mckayreedmoore/mini-moonboard/fea/code_aster_trial/contact_3d_mixed_reversed/README.md

# Reversed-order 3-D contact control

This Code_Aster 17.4 coupon repeats the frozen `mixed-active-open` geometry and loading while reversing the order of the two slave TRIA6 names in `GROUP_MA SLAVE`. The only mesh-data change from `fea/code_aster_trial/contact_3d_mixed/` is `ST00001 ST00002` to `ST00002 ST00001`; coordinates, PENTA15/TRIA6 connectivity, material, contact formulation, constraints, and time history remain unchanged.

`ST00002` is the raised, open face and comes first. `ST00001` is the flat, active face and comes last. The open face has the same 0.477881 mm minimum initial AUTO-sample gap and the same 0.447881 mm clearance after a hypothetical rigid 0.03 mm closure as the baseline order. This control tests whether the shared nodes’ final `CONT_NOEU` status and `RN` depend on the last contact face processed. Read the RN-to-cut residual as a diagnostic; this control does not require recovering a particular force increment and makes no capacity or joint-acceptance claim.

The paired active-open fixture completed at [contact-3d-mixed-attempt02](../../../docs/wood-joints-mvp/hypotheses/code-aster-candidate-checks-2026-09-27/contact-3d-mixed-attempt02/). Its independent audit found all three shared nodes open/zero after the later open face, with a 676.258 N RN-to-cut z residual. This reversed-order run is a diagnostic control; interpret it alongside that frozen result and the Code_Aster v17 documentation for [`CONT_NOEU`](https://code-aster.org/doc/v17/manuals/man_u/u2/u2.04.04/M_thodologies.html) and [`LAGS_C`](https://code-aster.org/doc/v17/manuals/man_u/u2/u2.04.04/R_solution.html).

After both native attempts are complete, `compare_order_control.py` verifies frozen input hashes, confirms only the `SLAVE` group order changed in the mesh, and compares the shared-node fields and remote reactions. The parent owns readiness review, serialized native execution, and final interpretation. Solver convergence and an order-control result do not establish joint mechanics or candidate acceptance.
