mckayreedmoore/mini-moonboard/docs/wood-joints-mvp/hypotheses/wj24-owner-design-review-2026-09-24/README.md

# WJ24 owner-directed design-review viewer

This archive records the local WJ24 viewer after switching the same URL to the isolated `owner_wood_joints_design_review_scene/v1` branch. The current revision is `lower-rear-blocks-below-plus-bottom-support-up-one-row-v1`: the middle rear blocks sit below their rails and the bottom support is raised one hold row. The current report lists lower-edge support, wire routing, and provisional G2/G6 hold-clearance items for design review. No acceptance, capacity, installation, fabrication, assembly, structural, or climbing release is asserted.

The final viewer source is [snapshotted here](snapshots/wood-joints-wj24-viewer.html.snapshot), SHA-256 `3afb271aa1403e839f6382f78d6a120e1f00429c2bd3ec870fa7c923ec138669`. Its scene payload is 9,335,595 bytes, SHA-256 `bf68c4247e1a99b1c7d5bad02b0fe5f6b9ddec34a47e1dca6d41edd2ad731389`. The source-bound revision report is [snapshotted here](snapshots/owner-wood-joints-review-report.json.snapshot), SHA-256 `bf8392ff07d213525e7032802979c887c9de53540361844aa84cc9e740ce1c33`. The scene binds source inventory SHA-256 `07af4c3eb642cf3887595fe4415eb65404cdcf74d66c5c7bb182847ef21c2d78` and parent scene SHA-256 `b80baec6b4435f4cfad724efdc25df787d04251f1a1b7203ba63782fb4b485f0`.

The overlay contains 568 solids: 16 shared hosts, 28 candidate parts, 520 hardware occupancy envelopes, and four panel replacements. The pinned baseline has 725 hashed assets; 537 render once and 188 replaced visuals are suppressed. The 66 panel-screw visual identities comprise 62 unchanged axes and four moved axes, whose baseline STL instances receive explicit display translations. Twelve starting frame-bolt arrangements remain in the baseline. These display envelopes and transforms describe nominal CAD geometry only.

The parent-run Chromium evidence is in [browser-evidence](browser-evidence/). It verified the current design-review status, 537 visible / 188 suppressed baseline visuals, all three camera buttons, all five layer controls, and the 390×844 mobile layout. The result records no page errors or failed requests. The parent visually checked the full-frame image and confirmed the middle blocks below their rails and the raised bottom support are visible. The associated screenshots and [browser-check output](browser-evidence/browser-check.json) came from the cumulative geometry before a later caption-only refresh to the two hold-clearance findings; the parent confirmed the geometry was unchanged and did not require a rerun. The final scene and report snapshots here include that refreshed text. The viewer’s frame-to-kicker-options link was then moved directly below the revision summary so it is easy to find; the archived final HTML includes that placement. The earlier browser session used the separately preserved [browser-session HTML snapshot](snapshots/wood-joints-wj24-viewer.html.browser-session.snapshot), SHA-256 `e42a6b97216c6119da89d8c90bd5b4399b4f9f3acecd426d159281f649d9a6e2`.

The new design-review branch reads only its current `revision_report`, checks the raw report and source-inventory hashes, validates the model inventory against the displayed solids and baseline replacement policy, and leaves the older diagnostic branch intact for its archived payload. Its visible status explicitly says that earlier static or diagnostic passes do not carry into this revision. The [separate frame-to-kicker options page](../../../../site/wood-joints-kicker-options.html) remains exploratory; no alternative is selected.

The previous integrated-static viewer review and its export-time/final snapshots remain unchanged in the [original WJ24 viewer archive](../wj24-viewer-review/README.md). This new folder supplements that record; it does not replace it. Screen-reader verification remains pending.
