mckayreedmoore/mini-moonboard/docs/wood-joints-mvp/hypotheses/hl35-candidate/README.md

# HL35 replacement candidate

The owner now requests a thinner successor closer to the selected
screw-and-angle frame, with structural through-bolts retained. The solid
6×8 center, 6×6 bottom rails and shaped 6×10 header below are no longer the
desired development direction. The [contract](../../../../hl35-candidate.json)
records the restored single-2×6/split-center comparison basis and open
connector selection. The [earlier kerf-right viewer](../../../../site/index.html?model=compact-floor-flush-kerf-right)
is a geometry reference with original screw hardware, not a through-bolted
successor. The [thin bolted viewer](../../../../site/index.html?model=thin-bolted-development)
now exports the original-size timber proposal with 24 B104ZN and 12 B103ZN
fittings, 70 complete bolt stacks and 66 Hillman axes. Its separate
[contract](../../../../thin-bolted-candidate.json) binds the reviewed v4 model.
The owner has viewed it and requested parallel numerical MVP work with six
GPT-6.1 Sol agents at xhigh. Geometry, access, compatible mechanics and
resistance remain distinct gates; no candidate is selected or released.
Use the [active ledger](../../completion-ledger.md#hl35-replacement-candidate)
for current results and exact missing inputs. Preserve all failed HL35 studies
and source bindings below.

The owner requested a separate candidate using HL35s instead of the wood
corner blocks on October 6, 2026, with an attempt to complete it overnight.
The candidate is **`compact-floor-flush-hl35-development`**, now at revision
**`hl35-deeper-header-seat-and-bearing-audit-v8`**, with disposition **REVISE**.
The [contract](../../../../hl35-candidate.json) remains separate from both
selected authority and the preserved reviewed wood-joint model.

Open the [preserved enlarged-frame viewer](../../../../site/index.html?model=hl35-counterbore-development),
[assessment](counterbore-fit-v8/README.md) and [preview](counterbore-fit-v8/overview.png).
It maps all 24 former block duties to 22 joints with **30 HL35s / 112 structural
planning bolt axes / 66 Hillman screws**. Eight screw moves and three wire
proposals are recorded only in this candidate; panel outlines, holds, T-nuts
and LED endpoints remain at their reviewed datums.

**Four lower outer corner joints still require revision.** The deeper washer
seats clear all checked bolt/angle, metal/metal, screw and service intersections,
but remove wood under neighboring angles. After the recesses, **112 / 120**
minimum-wood probes and **52 / 60** nominal flange seats meet the full-support
geometry comparison. The other eight flange seats retain about **86–87%**
of their nominal bearing area. This is a failed geometry criterion, not an
accepted reduced-area joint. The full catalog, wood resistance, force/moment
paths, machining and physical access remain unqualified.

The receiving-stock proposal includes a solid 6×8 center, 6×6 bottom rails,
4×6 service/top rails and a shaped 6×10 header. At an explicitly assumed
500 kg/m³, its sixteen finished receivers alone are approximately **342 lb**,
including about **69 lb center** and **62 lb header**. Legs/runners, plywood,
holds and all hardware are excluded. Heavy individual members are a drawback
for the owner's transport goal; no total mass, purchase schedule or climber
rating is supplied.

The overnight candidate-creation and bounded assessment attempt is documented;
it did not produce a build-ready design. Next redesign the four lower corner
interfaces to separate bolt/washer paths from neighboring bearing wood, then
resolve complete joint and practical machining/assembly methods before new
candidate-specific force and resistance work. The original panel concerns and
unverified no-slip floor assumption remain. No native solve or release exists.

The [first direct-swap viewer](../../../../site/index.html?model=hl35-development),
[v7 failed complete-tip query](final-fit-v7/hardware-closure.json) and all distinct
failed inputs remain preserved. Earlier claims of zero clashes covered the
listed subset; the supplemental v7 check found eight bolt/angle and four
bolt/unrelated-timber contacts. V8 includes those checks and the missing
after-recess wood assessment, rather than transferring the narrower result.

## First direct replacement: preserved failed input

The builder reconstructs the sixteen reviewed raw receiving profiles from
their authenticated snapshot. The four previously changed host positions are
retained: the two center kicker posts and two bottom rails. It removes the
24 wood blocks and their 92 candidate bolt arrangements. The starting twelve
frame-bolt arrangements and the current 66 Hillman axes remain: 58 original
axes and eight previously owner-directed moves, with no additional screw moves.
The owned panel policy, kerf-right outlines and G2 LED datum stay explicit.

Each old structural duty receives an angle on each side of its upright.
Four flange holes per angle give 192 attachments. Opposed post-flange holes
share through-bolts; four additional pairs of header attachments coincide
across duties. The model therefore has **140 new proposed physical bolt axes**
and **152 including the twelve starting axes**, rather than 192 new bolts.
Those are planning axes, including rejected paths through insufficient or
absent wood. They are not a purchase schedule or 152 qualified connections.
Each new axis has five conditional metal display roles: shaft, head, two
washers and nut. Actual products, shanks, thread windows and tools are unverified.

The fit audit uses exact CadQuery solid intersections, with a bounding-box
filter only to skip disjoint objects. It checks a nominal bearing skin behind
each flange, a complete 88.9 mm receiving-wood cylinder at every flange hole,
angle-to-angle and angle-to-raw-wood/panel intersections, and the preserved
63.5 mm screw-length envelopes. A source-bound cylinder is a geometry check;
neither its clearance diameter nor its penetration is a drilling instruction.

| Check | Direct replacement | Unadopted 3½-inch stock sensitivity |
|---|---:|---:|
| Joint duties requiring fit revision | 24 / 24 | 22 / 24 |
| Attachments lacking full 88.9 mm receiving wood | 152 / 192 | 36 / 192 |
| Flanges lacking full nominal rectangular bearing | 80 / 96 | 80 / 96 |
| Angle pairs with positive solid intersections | 5 | 5 |
| Angle-to-raw-timber/panel intersections | 0 | 12 |
| Preserved screw envelopes intersecting angle plates | 0 / 66 | 0 / 66 |
| New raw member-to-member intersections | Not a changed-stock trial | 8 |
| Recorded screw receivers absent at their original axes | 0 | 4 |

Every direct-replacement duty fails the minimum receiving-wood comparison.
Twenty-two also lack a full nominal bearing seat. Five pairs of inner angle
envelopes collide: top center, principal/header, bottom center and both service
rows. Each pair has 38,485.887 mm³ nominal overlap at the assumed plate geometry.
The 101.9 mm space between the original thin center principals cannot fit
two 82.55 mm inward-reaching flange envelopes at the same station.

The thickness-only sensitivity enlarges thin receivers to 88.9 mm, deepens
the header downward and shortens the kicker posts to its new underside. It
also realigns the angles to the changed member faces. It reduces the minimum
thickness failures, but retains unsupported opposing seats and inner collisions,
introduces eight member intersections, and loses four original upper kicker
receiver identities. Those axes may be geometrically received by a revised
header, but that reassignment and its complete load path are not adopted here.
The two center-post/header duties with no reported local fit finding remain
**UNQUALIFIED**, rather than accepted joints. The sensitivity is not the
displayed candidate or an approved stock/cut change.

## Catalog basis and limits

**HL35** is the manufacturer model name; the owner's “HL35s” is interpreted as
the plural. A distinct “HL35S” Simpson SKU has not been verified.
The readable manufacturer-authored
[C-C-2021 HL page, page 292](https://device.report/m/566c4ff6a72fec5f888f79af5915ebe858e6abbfae5c10476d7cc776ab45e1b9.pdf)
gives 3¼-inch flange reaches, 5-inch bend length, four ½-inch bolts,
3½-inch minimum receiving wood and 2½-inch hole pitch. It also requires
centered bearing on a sufficiently wide member and opposing connectors for
lateral loads in both directions. Its tabulated 740 lb uplift and 1,310 lb F1
values are at the stated 160% duration basis. These are reference entries,
**not adopted climbing capacities**.

The manufacturer [current catalog landing page](https://www.strongtie.com/resources/literature/wood-construction-connectors-catalog?source=topnav)
identifies C-C-2026. An available
[manufacturer-authored current HL page](https://dhcsupplies.s3.us-east-2.amazonaws.com/Documents/simpson-strong-tie/hl-angles.pdf)
is hosted by a supplier. Its exact current page and factory CAD must be
authenticated and read before adopting a product-specific resistance table.
The older readable page identifies 8-gauge HL35, while retailer descriptions
and historical repository envelopes use 7 gauge. This discrepancy is unresolved.
The model consequently uses an explicit **5 mm planning occupancy envelope**,
with no inferred steel yield strength or delivered thickness.

The horizontal flange hole offset is not fully dimensioned in the cited
drawing; **50.8 mm is a provisional symmetric coordinate**, inherited as an
explicit assumption from the earlier HL35 fit study. Bend radius, factory
hole dimensions, coating and tolerances are unmeasured. No custom steel
fabrication is proposed.

Two connectors may allow the cited uplift treatment when the complete
installation is applicable. **Their lateral rating may not be doubled.**
Rotating an angle with a sloped member also rotates its catalog force axes;
global horizontal or vertical force cannot simply be assigned to F1/uplift.
The HL35 table does not supply an arbitrary transverse or six-component moment
capacity. A complete joint must establish force and moment transfer through
the actual bolt group, bearing/contact and receivers, without inventing those
missing capacities or treating each angle as an independent duplicate joint.

## Remaining development work

The direct swap and thickness-only trials failed. The later revisions resolve
their nominal fit questions through changed receivers, explicit screw shifts,
offset rails, full metal checks and service-clearance proposals. The
[current packet](counterbore-fit-v8/README.md) distinguishes those usable geometry results
from the remaining engineering work; repeating any unchanged failed trial
would not add evidence.

Next establish actual product identity and installation direction,
current catalog/wood method applicability, signed force/moment paths, bolt
spacing and loaded edges, full metal/thread/washer/tool clearances and individual
member removal. The service envelopes need a practical machining/feeding plan
and net-member checks. Fresh whole-frame demand must retain the original **250 lb**,
**2× downward**, **300 N horizontal**, **100 mm hold lever** basis, with new
member/hardware dead load. The old panel head and rolling-shear deficits do
not disappear by changing the structural connector. No native solve is ready
or performed for this candidate. No-slip floor support remains unverified.

## Evidence and reproduction

The [current assessment](counterbore-fit-v8/fit-assessment.json) and
[manifest](counterbore-fit-v8/manifest.json) bind the current experiment. The preserved
[first fit assessment](fit-assessment.json) records every duty, flange, hole,
physical axis, preserved screw and intersection. The
[stock sensitivity](thickness-sensitivity.json) retains the separate failed
experiment. The [manifest](manifest.json) binds input/output bytes and the
CadQuery version; the two earlier authority files remain unchanged.

```bash
.venv/bin/python -m scripts.hl35_candidate --thickness-trial
.venv/bin/python -m scripts.hl35_counterbore_candidate
.venv/bin/pytest -q tests/test_hl35_candidate.py
node scripts/check_hl35_scene.mjs /PATH/TO/three.module.js
```

The Three.js check uses an existing dependency, performs no installation, and
authenticates/loads the actual parent and candidate scenes. It checks complete
planning stacks, shared physical axes, all 66 screws and rejection of invalid
release flags, duplicate roles, distorted transforms and incorrect bindings.
The geometry controls separately check closed-form angle volume, real solid
intersection, incomplete receiving thickness and source/axis preservation.

Active: the v8 candidate, contract, current viewer, reproduction helpers and
remaining engineering gates. The v1–v7 packets are closed failed experiments;
their helpers remain dependencies and their exact bound bytes remain available.
The reviewed wood model and corrected original-load results are preserved
references. Aluminum is a separate unselected concept. Before any later removal
of closed HL35 exports, follow the repository's external archive/restore/prune
procedure and recheck current consumers. No archive, pruning, commit or push
occurred in this task.
