mckayreedmoore/mini-moonboard/docs/wood-joints-mvp/hypotheses/mvp-integration-2026-10-01/README.md

# Current wood-joint MVP integration

For the October 1 account handoff, start at
[NEXT-AGENT-HANDOFF-2026-10-01.md](../../NEXT-AGENT-HANDOFF-2026-10-01.md).
It records the latest verified packets, stopped workers, unfinished code,
native limits, ownership, quota restrictions and precise restart points.

On October 1 the owner directed the primary to complete the full conditional
MVP-E and keep two secondary chats working on disjoint tasks, verifying each
result before integration and assigning more work when a lane finishes.
This continues the endpoint in the [completion handoff](../../luna-max-completion-handoff.md#1-endpoint-and-authority):
the same reviewed revision, complete joint duties, six valid frame cases,
47 criterion dispositions, fit/service/transport, source-backed materials and
cost, a coherent conditional shop package, and independent final review.
Finishing a source join or method fixture does not complete that endpoint.

The development revision is `led-clearance-2x6-runner-seated-blocks-v1` under
`compact-floor-flush-wood-joints-development`. The selected angle-frame
candidate remains separate. Preserve the 92 candidate bolt axes, twelve
starting frame-bolt arrangements and 66 Hillman axes, including the eight
previously directed moves. Report required changes before altering geometry.

## Current ownership

| Owner | Current task | Verification and handoff |
| --- | --- | --- |
| Primary, `01a0f821-5e03-7781-bb0e-0d15efebcbe2`, tmux `main:9.3` | Washer/contact result validation, A12 source-comparison validation, integration and remaining MVP scheduling | Check pinned solver documentation, analytical oracles, exact input freeze and independent reviews before each bounded launch. Verify raw outputs and retain failed attempts. |
| First secondary, `01a0f822-102c-74f1-bf9b-6d33a0b66ab3`, tmux `main:9.1` | Whole-boundary center-post, cleat and header actions, after verified backing audit | Preserve every boundary port, signed source action and direct-seat/cleat route distinction; no force allocation or joint qualification. |
| Second secondary, `01a0f823-860d-7b63-a57d-1917507f3b53`, tmux `main:9.2` | Finished directional edges for twelve retained bolt arrangements, after verified conditional resistance references | Authenticate finished profiles and a directional ray method, retain other cuts and distinguish stock-box distances from finished edges; send a concrete plan before any CAD extraction. |

The corrected contact preparation worker has finished and stopped. Both
preparation folders and the refused first contact freeze remain unchanged.
The primary froze attempt02 separately, obtained three fresh readiness
reviews, and executed one serialized 60-second, 1-GiB, one-CPU contact fixture.
Its frozen resultant audit and three independent result reviews pass; the
primary authenticated the final result chain. Reviewers write only their own review files and cannot launch a
solver, change a shared helper or edit the native ledger.

The A12 preparation worker has also finished and stopped. The primary froze
its final 22-input runner under `parent-input-freeze-02.json`, obtained three
independent readiness reviews, and executed the single bounded two-body
source recovery. It finished in 5.23 seconds with two factorizations and zero
refinement corrections. Both numerical method screens pass, but the recovered
table force remains outside the unchanged native RF interval. All 27 original
force-interval failures and the raw-H STOP remain. No source force is adopted;
three independent result reviews pass and the primary authenticated the
final result. This was source-matrix
recovery, not a new native solve or complete frame state.

The [exact-47 evidence audit](criterion-evidence-audit.md) passed the primary's
ID-parity, pending-status and local-reference checks. The completed
quarter-inch source packet passed the primary's byte-identical replay,
receipt hashes, seven tests and Ruff. Its wording corrections are integrated
in the [current additive source record](source-wording-reconciliation.md);
older pinned packets stay byte-preserved. Neither material scenario is
adopted and no joint resistance gate closes.

The final panel packet passed primary's full exact replay, 30 tests, Ruff
and all 171 byte/size/hash pins. Its report is
`0ac0e30d582322f8919277aabec3af134c7bf5ecb2b0523d649622bcd4a47534`.
The final review record explicitly defers a direct cross-checkout action-API
guard and optional synthetic combination; the supported producer route and
complete independent raw-source oracle cover the present join. Neither the
failed reduced mapping nor unqualified Hillman laws become accepted by the
successful physical-body endpoint projection.

The existing mechanics receipts, operators and failed-run limits remain
controlling. The shared native slot was observed idle with no live solver
on October 1 before preparation. Native readiness, input freezes, single-run
reservations, execution and final response acceptance stay parent-owned.
One new affine annulus known-answer run has now executed in
`../washer-annular-affine-native-2026-10-01-attempt01/`, under freeze
`093ab967c805858b33e3d0530cadab25625cc3b8c69f696d3c39885302fa6817`.
All three independent pre-run reviews passed or had an explicitly satisfied
parent control condition. The single run used one CPU, 1 GiB and a 60-second
limit, exited successfully and returned the native slot to idle. Its frozen
elastic displacement, stress, reaction and energy gates pass. Three independent
result reviews pass and the primary authenticated their exact hashes with
the raw outputs and execution record. This is a hypothetical software fixture,
not a contact, washer bending, material or candidate resistance qualification.
The separate first finite-sector contact attempt is frozen at
`6ccdd8cee4c499c7438aef8c07a6ee9cba8d11beb145fdb1719cde9f4b7e95c4`
and is refused before launch. The primary found that its actual deck omits
every support and gauge `*BOUNDARY` card: the generator constructs the
restraint lines but never emits them. No launch is consumed, its original
inputs remain unchanged, and the parent refusal supersedes earlier packet-ready
reviews. A separate corrected preparation packet with an actual-deck constraint test
passed fresh independent readiness review. Its native attempt02 is frozen at
`87894949d0f9aa45ca479fa290fb2ae8c354884d290b9ac0e13e2a902522c8aa`.
The single run, `wj-washer-finite-sector-contact-20261001-a02`, exited zero in
5.60 seconds and returned the native slot to idle. The frozen audit passes
with whole-model force residual `7.27e-7 N` and moment residual
`0.000715 N·mm`; both are below the original `0.1` limits. Frictionless shear
resultants are zero. The primary output receipt binds raw results, exact
oracle/verifier/coordinate identities and the execution record; independent
result reviews pass and the primary authenticated their hashes in final
parent result `8fa2c65a09395f177123ce77e7305a81f690f5e843bc69b1ff7b1e0cc9d1deea`.
The frozen verifier includes one free gauge-x RF component of `1.015614e-15 N`;
independent constrained-DOF-only reconstruction also passes, so this detail has
no effect at any declared gate. A future packet should mask constrained DOFs.
This supplies only hypothetical contact resultant/output-method evidence.
A separate source-only worker now prepares
`../current-washer-conditional-3d-contract-2026-10-01/`: candidate-specific
local-stack inputs, full/partial-seat geometry, supported or explicitly
hypothetical material/contact branches, and concrete method/sensitivity gates.
It cannot generate a native freeze or launch. A second source-only worker
completed `../a12-source-comparison-next-method-2026-10-01/`. Its saved-data
replay matches the retained force; rationalized high-precision endpoint
arithmetic shifts it by only `-3.65e-12 N`. The computed-length half-ULP scale
is not an end-to-end force-error bound. The original RF miss remains. The
worker also prepared `../ccx223-matrix-output-precision-preflight-2026-10-01/`:
a one-token stiffness-output patch and a host-C 16-value round-trip check.
Primary reproduced both checks, authenticated their pins, and verified the
patch dry-run. Mass output remains unchanged at 14 significant digits.
All three fresh independent source reviews pass. The primary authenticated
the stable packets and review hashes in
[source-next-method-parent-validation.json](source-next-method-parent-validation.json).
This does not identify export rounding as the RF discrepancy's cause or
authorize a candidate export.
The worker now prepares an isolated build/coupon packet without executing
Docker, a build, native analysis or source-matrix recovery.
Do not duplicate an old coordinator run or infer a new usable case from its
partial operator diagnostics.

The final retained-bolt source join passed the primary's byte-identical
producer and independent raw-token oracle replays, eight tests, Ruff, all
143 input pins and seven final code/review pins. Its report is
`f068cd5afc93c2b7027624b1fbec94ccb419f664833d920d2959f79bed661cc1`;
the raw oracle receipt is
`c6d43017d67f864dfc25e6a77832a542a97257a1da23f4ca3a12e82d6a829ea9`.
The verified join covers 252 signed bolt states, 504 combined receiver
wrenches and 168 complete body states. It supplies current demands only;
the missing response cases remain open. The next retained-bolt resistance
packet also passed primary byte-identical producer/oracle replay, all final
file/artifact pins, nine tests, Ruff and three final independent reviews. Its
report is `c3250f067c4590ee43f7ec7a5765d056d87e6ff5adb42837ed27710d9b4d4eb1`.
Its conditional single-fastener reference ratios peak at 0.746679, 0.359216
and 0.0705113 for upper/front/rear arrangements under the 45-ksi scenario;
all adjusted resistance fields remain null. Every saved group is oblique to
its row, so the existing aligned-row Cg method is not applicable. These are
unqualified component references, not joint passes. The second secondary now
owns finished directional edges for the same twelve arrangements.

The final center-backing packet passed primary's exact producer replay, all
302 input hashes and sizes, 42 tests, Ruff and byte-identical independent
geometry/duty oracle replays. The final three-review record and all 17 listed
artifact hashes authenticate. Parent validation is recorded in
[center-backing-parent-validation.json](center-backing-parent-validation.json).
The report is `79f7058b9067d4c0a34206d04f6c6580c005a603a42388dd00bb54ac070979ad`.
The disclosed stale historical prose pin still refuses the broad atlas closure;
only its unchanged numerical dependency chain is reused. The future authority
updater is explicitly deferred: changed prose requires a new source review.
The first secondary now owns the five center receiver bodies' whole-boundary
actions in a separate source-only packet. No direct-seat/cleat force split,
new member or criterion acceptance follows from the backing audit.

The primary verified the exact right-corner metadata plan and 180 byte,
size and hash pins, plus ten source-only tests. The
[CAD reservation](right-corner-cad-reservation.json) binds 902 point identities,
271 planes, the whole 338-interface boundary and current local code. One
300-second, 4-GiB, one-process extraction finished in 71.20 seconds, with
peak RSS 862,356 KiB. All 271 planes and 5,691 source-action cuts remain;
one terminal plane has null properties. Primary reproduced the independent
saved-point/cut and contact oracles, 13 tests and Ruff, and authenticated final
review and output hashes. The three independent reviews close with an explicit
defer of a separate pre-CAD lock/Python guard; runtime observations and exact
numerical oracle coverage are retained in the final record. No retry is authorized.
An empty or lower-dimensional terminal section remains distinct from a
kernel failure and supplies no invented section properties.

## Completion and resource boundaries

The exact criterion register still records 47 pending entries. Three
authenticated rear diagnostic exports are usable within their documented
scope; forward, left and right cases remain unresolved. The newer section,
seat and panel packets supply additional prerequisites, not six-case or
resistance acceptance. The criterion-evidence audit will reconcile those
prerequisites without altering criterion authority or importing historical
passes.

The owner explicitly prohibits credit use if included usage runs out. Stop
on included-usage exhaustion; do not enable a paid or API fallback. This
constraint applies to both secondary chats and their workers. Continue local
work on `master` while preserving other owners' edits; quiet-hours commit and
push restrictions remain in force. Physical receiving, fabrication, drilling,
candidate selection, floor qualification and climbing release remain outside
this goal. Actual inspection cells remain blank.

At 20:48 UTC the current permission profile changed. The primary's tmux
socket and direct quota RPC are unavailable, and its earlier preparation
agents no longer appear in the live tree. Fresh local `token_count` quota
events still report 97% included weekly use without a reached limit. The
read-only fallback `/tmp/mini-moonboard-included-usage-rollout-check.py`
reports only quota fields and refuses missing, older-than-120-second or
exhausted evidence; it changes no account or billing setting. The ordinary-
usage RPC flag remains unobserved under this profile. Two replacement
Luna/max workers prepare only the isolated STI17 build/coupon and exact washer
crop/mesh packets. Neither can run Docker, CAD, meshing or native analysis.
The two existing tmux chats' local records show they are holding new delegation
while resolving the quota-query restriction. New direct assignments cannot
be delivered through the current transport. Their completed packets and
already assigned scopes remain preserved.

By 21:29 UTC both existing secondary chats were progressing on their already
assigned scopes using fresh local quota evidence. Included weekly usage was
98%, with no reached limit recorded; the ordinary-usage RPC remained
unavailable. The first has produced the center receiver boundary draft and
is checking it independently against saved DAT and deck sources. Its draft
contains 212 interface groups and 105 body balances; final raw verification
and review are pending. The second has completed the numerical edge checks
and 39 tests, and is running a fresh fourth review after correcting refusal
coverage and external checker-pin handling. Primary independently reproduced
its current report and byte-identical raw-oracle receipt
`faa735bc0c386373c4639e7d7e9dcf88dbc97e28552ddc1719a66075f8efc028`.
This is provisional verification while final review remains open.

The STI17 build/coupon scripts are present and remain unexecuted. Their
source-level refusal tests and lint corrections precede independent review.
The washer preparation now uses the explicit hypothetical
[nut profile](conditional-nut-profile.json). The separate
[hardware geometry oracle](conditional_hardware_geometry_oracle.py) agrees
with independent section quadrature; no CAD or delivered-product geometry
has been established. The washer worker is preparing the concrete R75/H1
five-solid mesh producer, without running it.

The pinned 2.23 `*EL PRINT` documentation defaults stress output to the local
material frame (`GLOBAL=NO`). The existing rotated matrix coupon does not
print stress, and the affine annulus has no material orientation. Neither
qualifies that distinction. The proposed nontrivial rotated-orthotropic
[stress-frame oracle](orthotropic-stress-frame-parent-oracle.json) therefore
remains an unobserved analytical known answer for a separate small output
fixture. Candidate source-normal stress interpretation requires this explicit
frame check. No new native run, build, mesh or criterion acceptance follows
from these preparation records.

The retained edge packet subsequently completed its fourth independent review
with no current defect and an explicit defer of duplicating the mandatory
raw oracle inside pytest. Primary authenticated 165 source pins and 23 final
file/artifact pins, the exact report and byte-identical oracle receipt, all
39 tests and Ruff in
[retained-finished-edges-parent-validation.json](retained-finished-edges-parent-validation.json).
Nominal directional samples are integrated; NDS applicability, through-depth
minima, adjustment factors and joint resistance remain unresolved.
The second secondary's next assignment is recorded in
[the shared dispatch](secondary-next-assignment-2026-10-01.md); direct tmux
delivery remains unavailable.

The small [stress-frame preparation](../orthotropic-stress-frame-preparation-2026-10-01/README.md)
now contains an unfrozen input generator and pure numerical reader, with
16 synthetic tests passing. It requests 4,608 stress rows across three frame
selections and 800 displacement rows. An execution-provenance wrapper,
independent review and parent freeze are still required before readiness.
The standard read-only Docker image inspection at 21:35 UTC failed on the
current socket permissions. No new build, mesh or native execution occurred.
