mckayreedmoore/mini-moonboard/docs/wood-joints-mvp/hypotheses/washer-finite-sector-contact-native-2026-10-01-attempt01/README.md

# Frozen finite-sector contact method attempt

This parent-owned attempt contains the exact prepared hypothetical two-body
annular fixture. It is a separate method check after the single affine run.
No native launch is authorized until three independent readiness reviews,
completed affine result reviews and a parent readiness receipt bind this
freeze and the one-launch, 60-second, 1-GiB, one-CPU bounds. The primary
currently reserves heavy execution for the right-corner CAD extraction.

The load is positive inward pressure of 2 MPa on one quarter of the polygonal
upper surface: initial area 18.36880475352431 mm², force -36.73760950704862 N
in z and origin moment (-96.67494650869216, 96.67494650869219, 0) N·mm.
The final oracle integrates the same pressure over the deformed quadratic
face coordinates, since DSLOAD is follower pressure. Contact CF/CFN/CFS,
upper gauge reactions and lower support reactions retain their distinct
semantics and fixed gates. The gauges do not share pressure nodes.

Both bodies are diagnostic isotropic linear-elastic solids with Poisson
ratio zero. The receiver is not wood. The normal penalty is an assumed
software law, not wood indentation stiffness. The result scope is load
transfer, moments and output extraction; pressure distribution, washer
bending stress, strain, crushing, plasticity, partial-seat resistance, actual
properties and candidate acceptance remain outside this check. Preserve a
failed launch or fixed gate; no retry of this freeze is authorized.
