mckayreedmoore/mini-moonboard/docs/wood-joints-mvp/mvp-acceleration-2026-09-28/nds-screen/README.md

# Preserved preliminary calculation draft

The agent created these two draft files in a separate directory while the
parent assembled the final packet. They are preserved as preliminary work,
not adopted candidate evidence. The completed, checked calculation and its
limitations are in the [assessment packet](../../hypotheses/mvp-acceleration-2026-09-28/nds-screen/README.md).
