mckayreedmoore/mini-moonboard/docs/round-reinforcement-browser/selected-t-nut.png

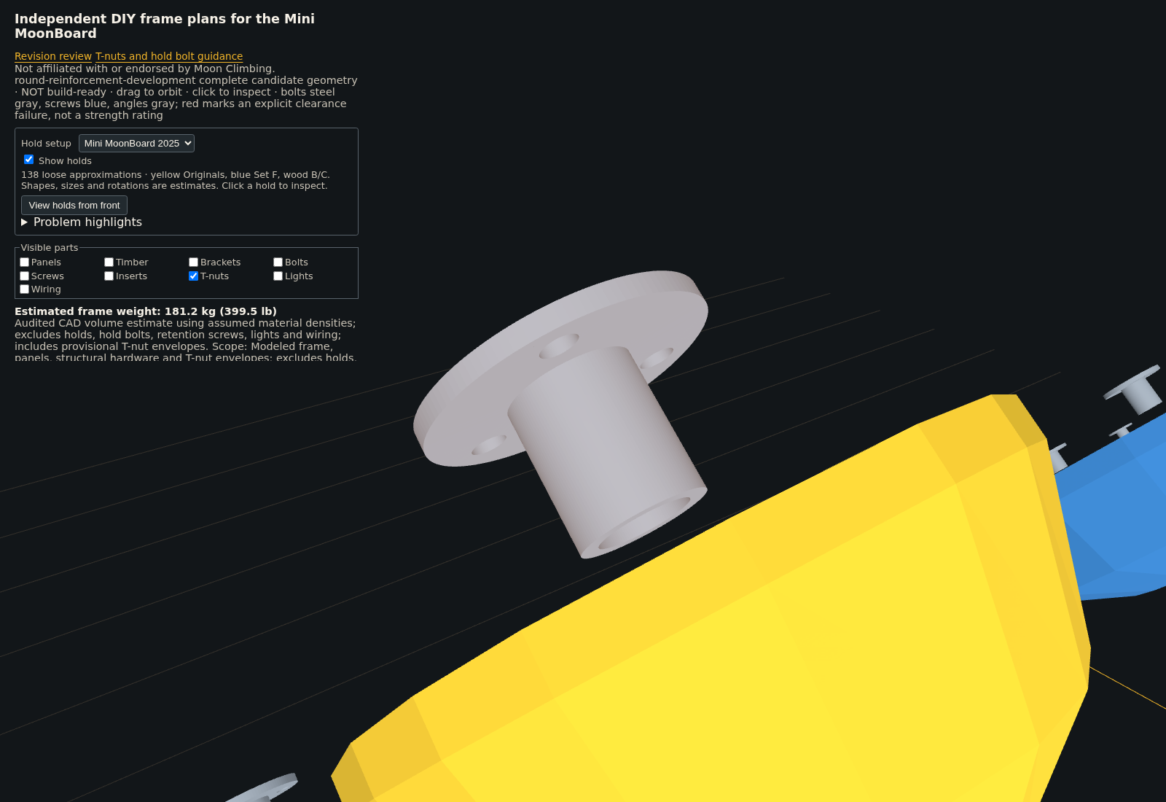
docs/round-reinforcement-browser/selected-t-nut.png
