mckayreedmoore/mini-moonboard/docs/round-reinforcement-review/lower-frame.png

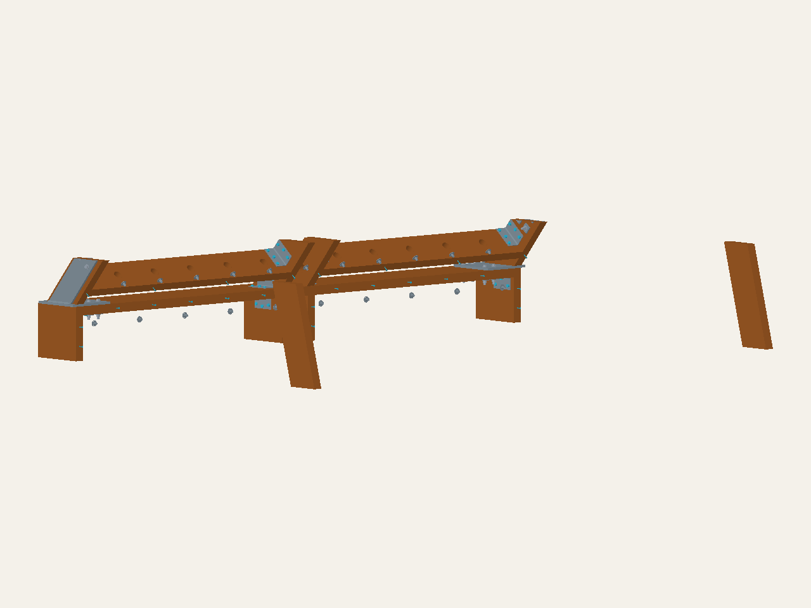
docs/round-reinforcement-review/lower-frame.png
