mckayreedmoore/mini-moonboard/docs/wood-joints-mvp/hypotheses/bottom-support-above-tnuts-2026-09-24/viewer.png

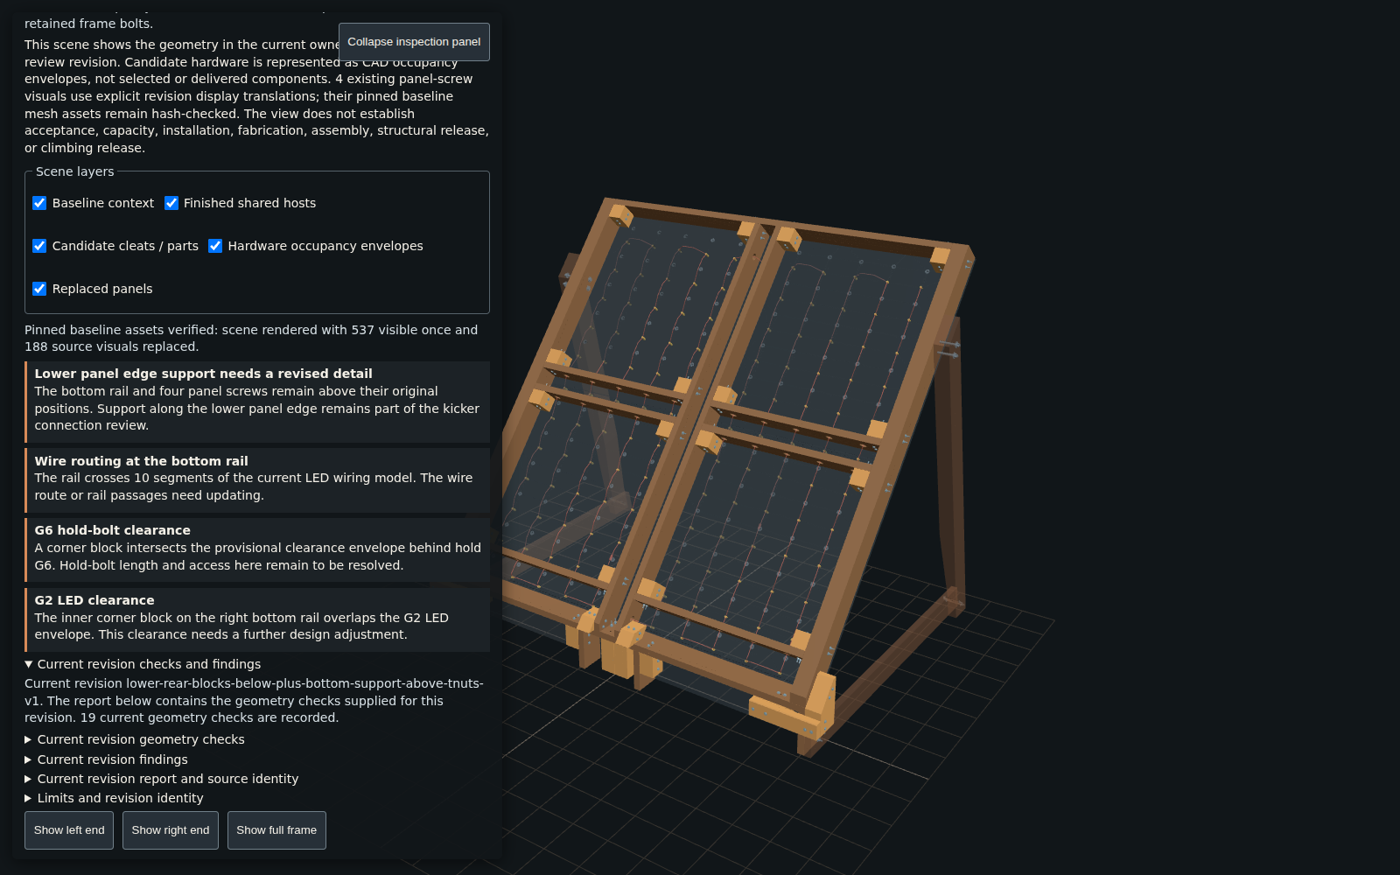
docs/wood-joints-mvp/hypotheses/bottom-support-above-tnuts-2026-09-24/viewer.png
