mckayreedmoore/mini-moonboard/docs/wood-joints-mvp/hypotheses/hl35-candidate/thin-frame-comparison/eoere-successor-v1/source-drawing.jpg

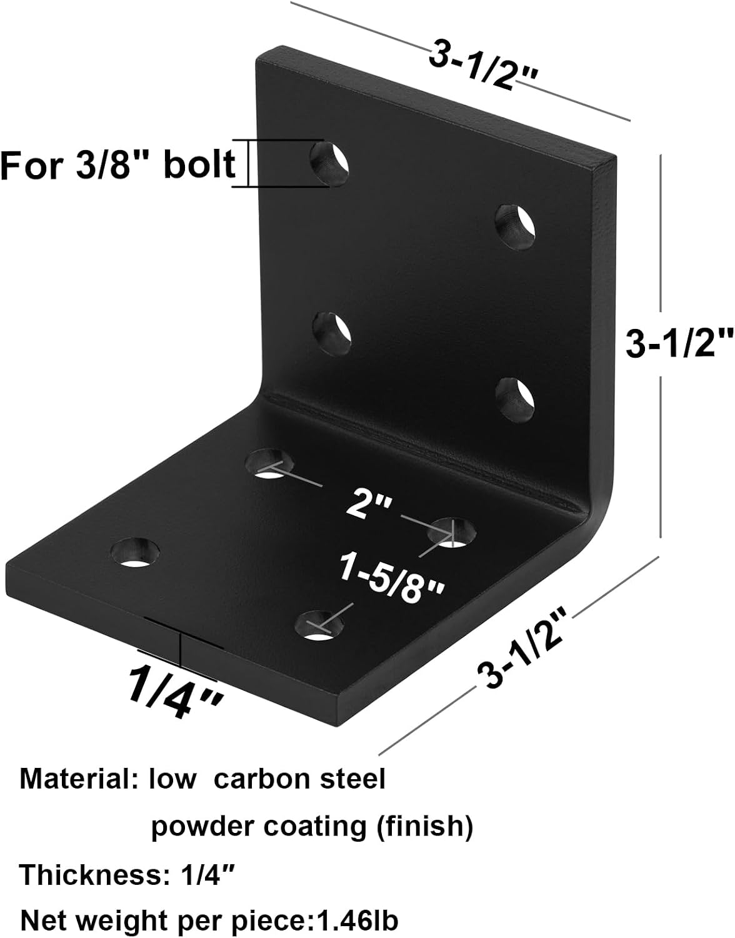
docs/wood-joints-mvp/hypotheses/hl35-candidate/thin-frame-comparison/eoere-successor-v1/source-drawing.jpg
