mckayreedmoore/mini-moonboard/docs/wood-joints-mvp/hypotheses/midpoint-clearance-2026-09-24/maps.png

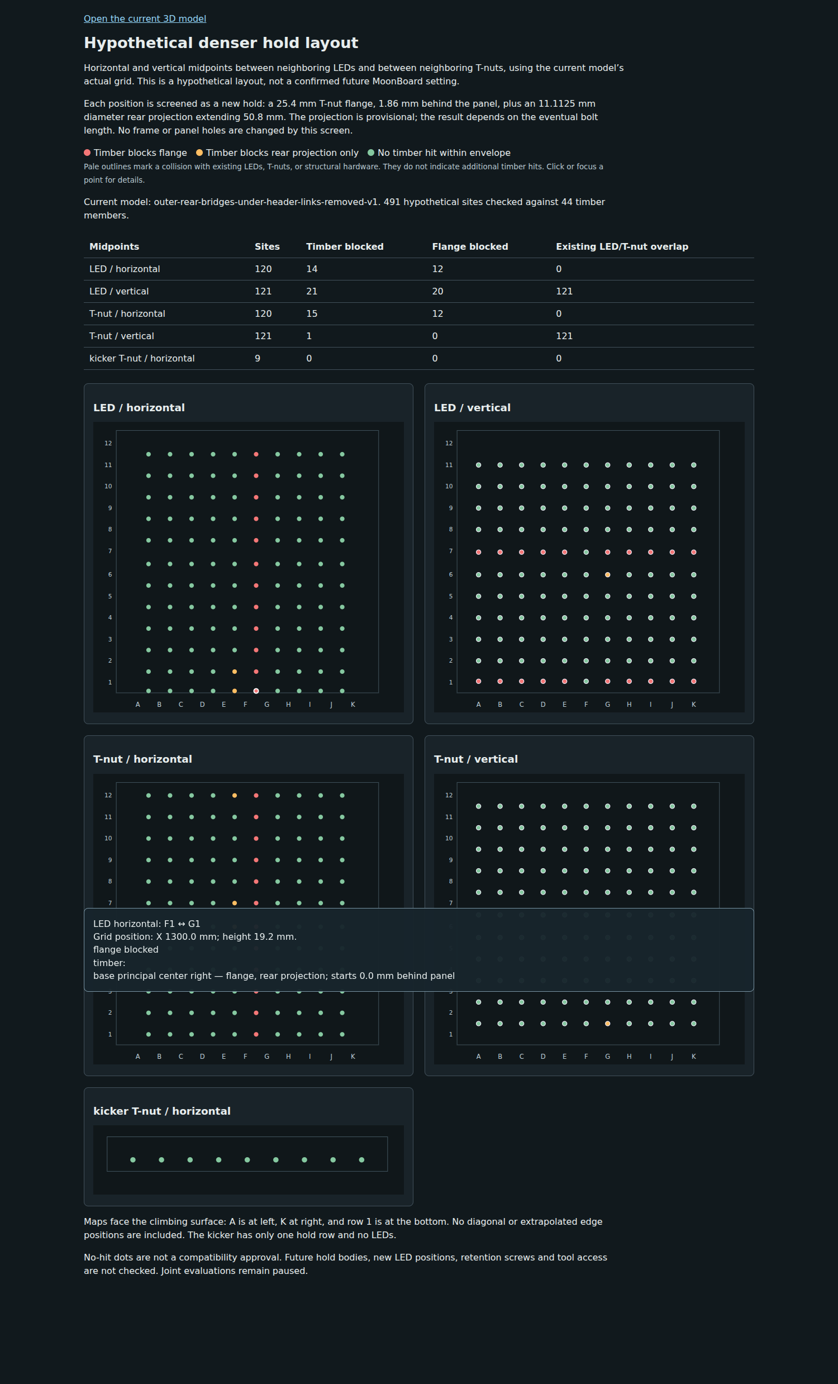
docs/wood-joints-mvp/hypotheses/midpoint-clearance-2026-09-24/maps.png
