mckayreedmoore/mini-moonboard/docs/wood-joints-mvp/hypotheses/outer-links-removed-2026-09-24/viewer.png

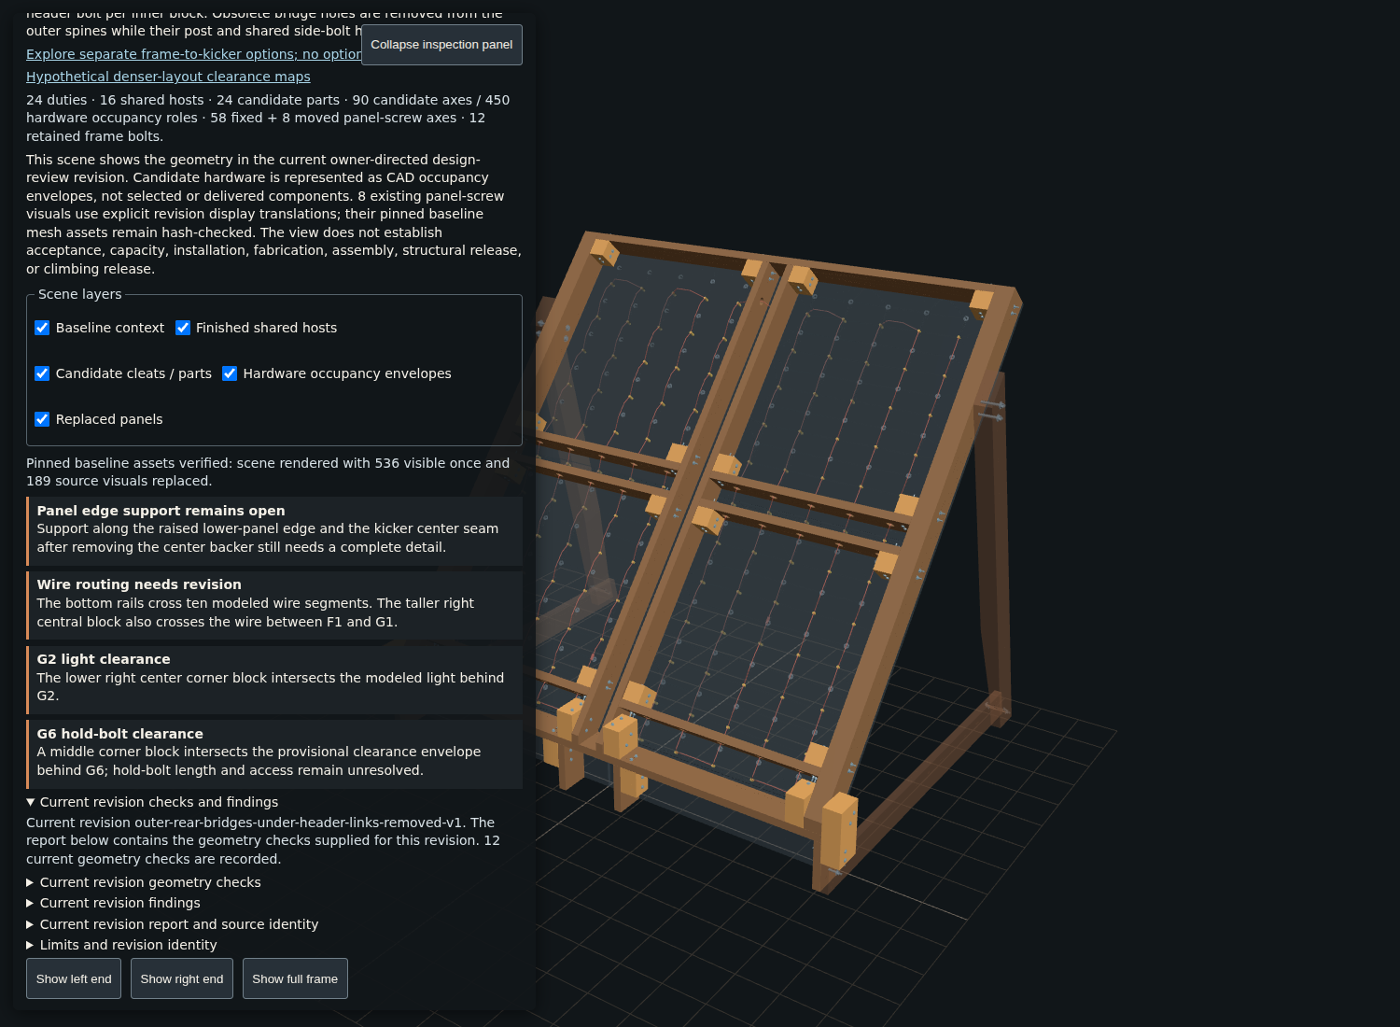
docs/wood-joints-mvp/hypotheses/outer-links-removed-2026-09-24/viewer.png
