mckayreedmoore/mini-moonboard/docs/wood-joints-mvp/hypotheses/owner-geometry-review-2026-09-24/browser/mobile.png

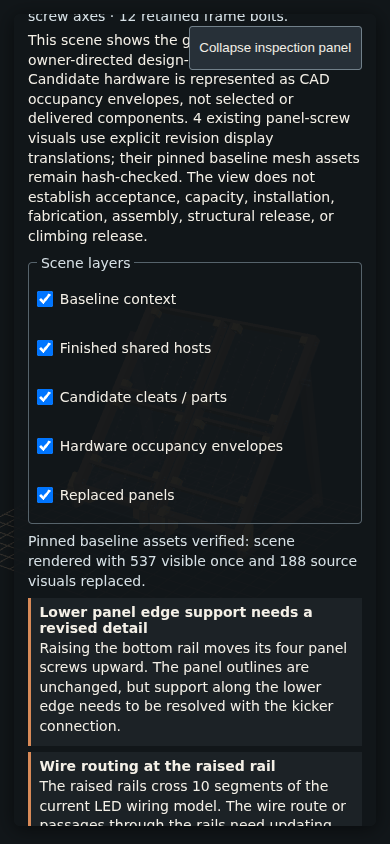
docs/wood-joints-mvp/hypotheses/owner-geometry-review-2026-09-24/browser/mobile.png
