mckayreedmoore/mini-moonboard/docs/wood-joints-mvp/hypotheses/wj24-viewer-review/browser-evidence/final/desktop-left-end.png

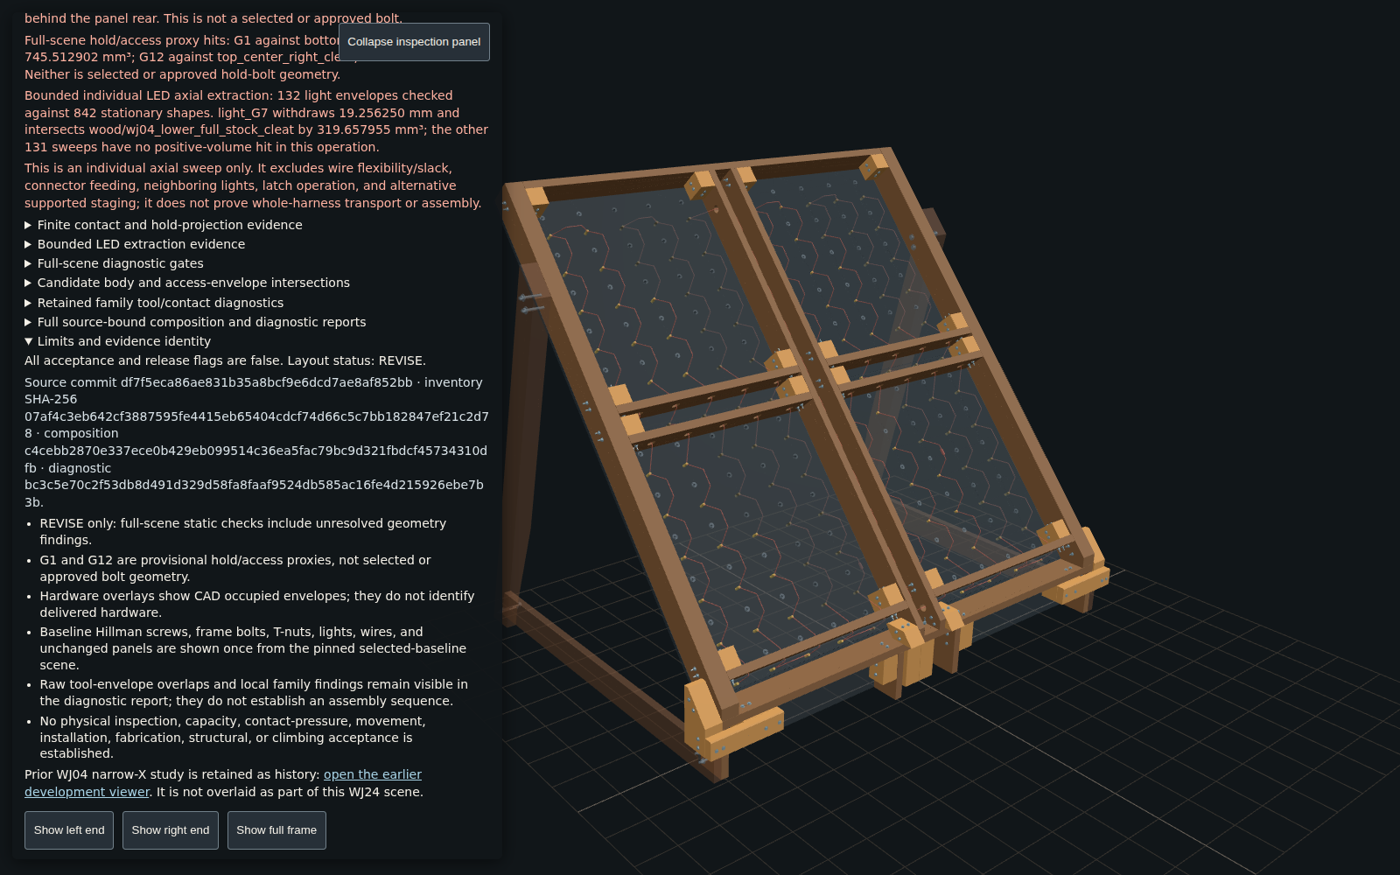
docs/wood-joints-mvp/hypotheses/wj24-viewer-review/browser-evidence/final/desktop-left-end.png
