mckayreedmoore/mini-moonboard/docs/wood-joints-mvp/hypotheses/wj24-viewer-review/browser-evidence/final/desktop-right-end.png

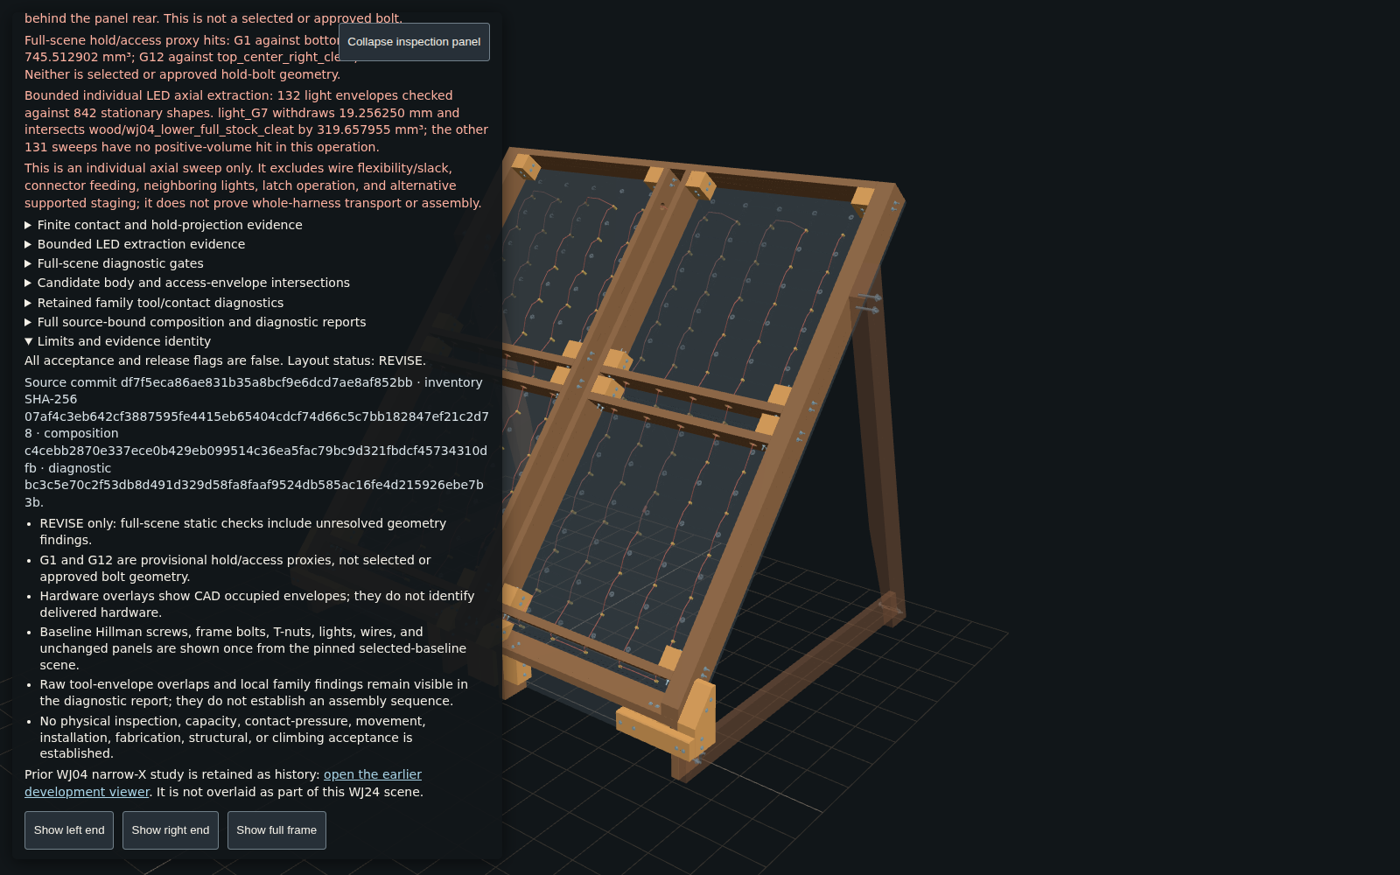
docs/wood-joints-mvp/hypotheses/wj24-viewer-review/browser-evidence/final/desktop-right-end.png
