mckayreedmoore/mini-moonboard/docs/wood-joints-mvp/hypotheses/wj24-viewer-review/browser-evidence/final/keyboard-arrow-down.png

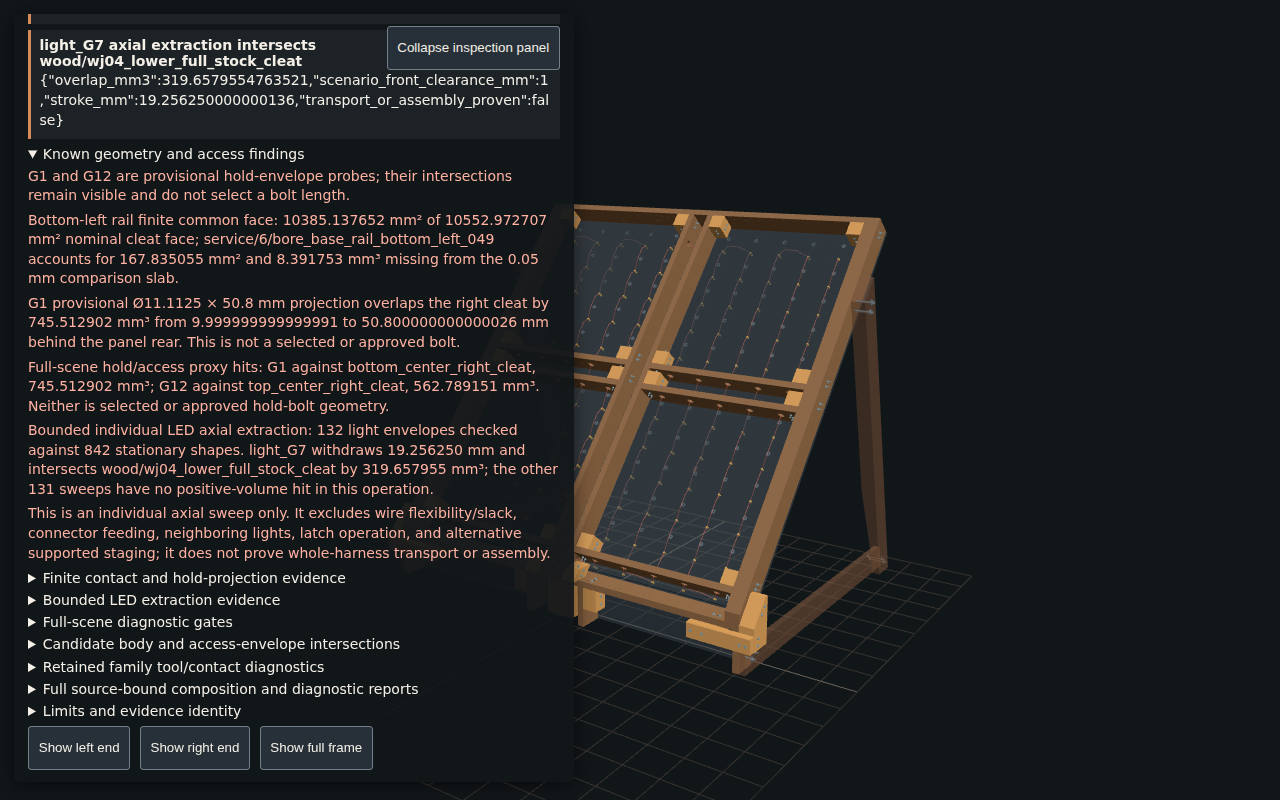
docs/wood-joints-mvp/hypotheses/wj24-viewer-review/browser-evidence/final/keyboard-arrow-down.png
