mckayreedmoore/mini-moonboard/docs/wood-joints-mvp/hypotheses/wj24-viewer-review/browser-evidence/final/keyboard-arrow-right.png

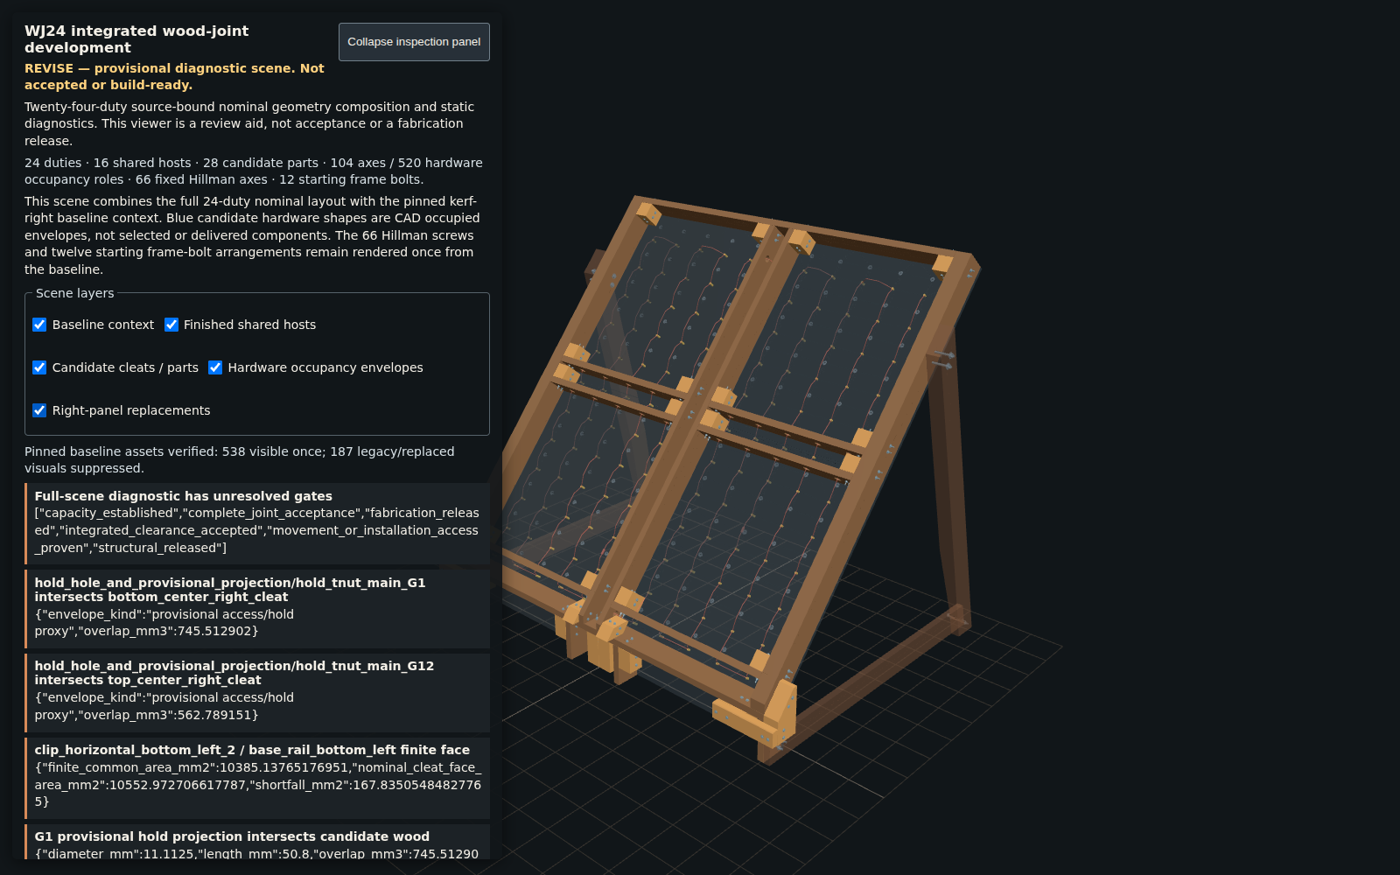
docs/wood-joints-mvp/hypotheses/wj24-viewer-review/browser-evidence/final/keyboard-arrow-right.png
