mckayreedmoore/mini-moonboard/docs/wood-joints-mvp/hypotheses/wj24-viewer-review/browser-evidence/final/layer-finished_host-hidden.png

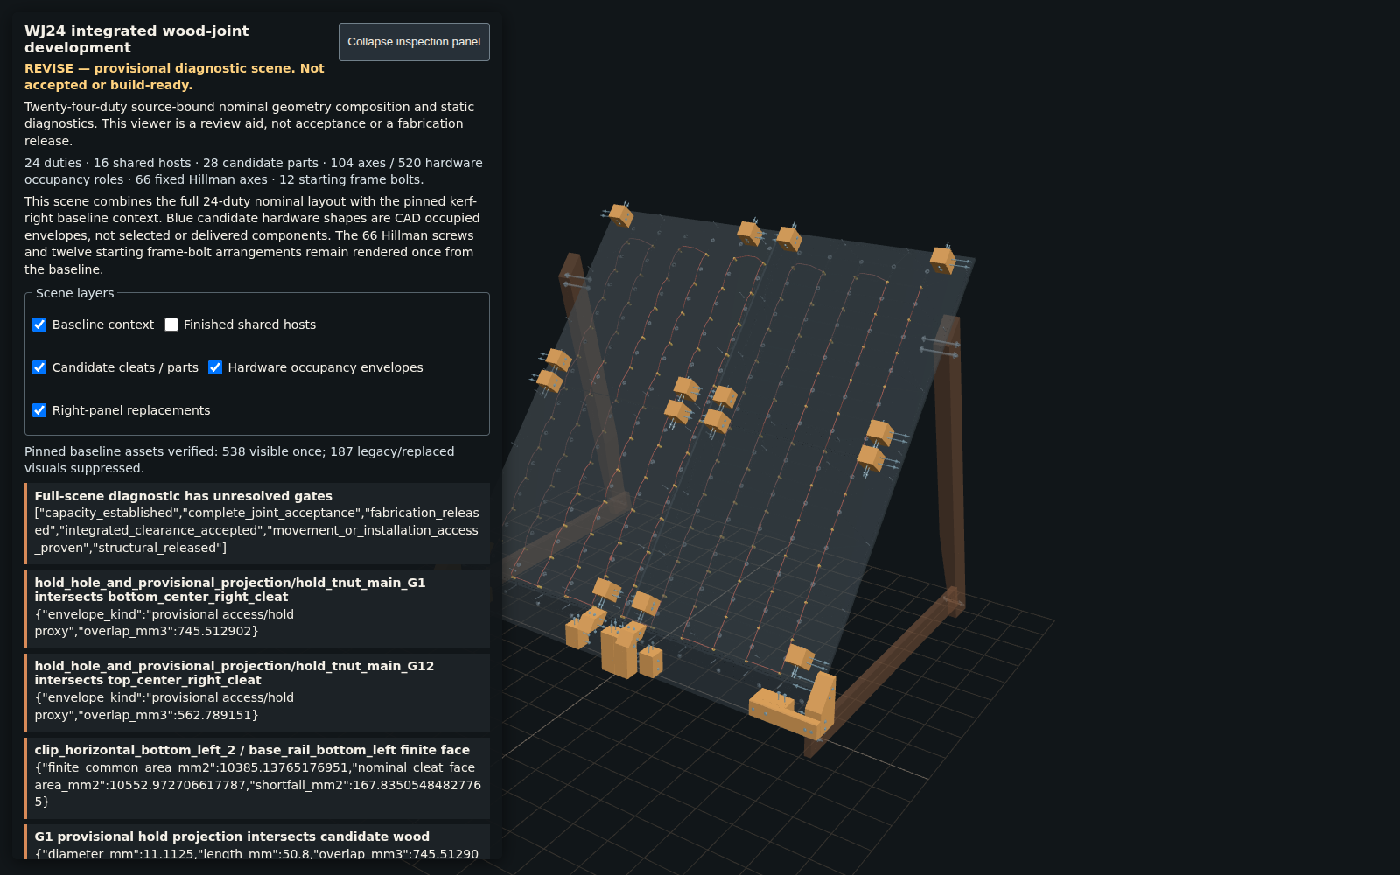
docs/wood-joints-mvp/hypotheses/wj24-viewer-review/browser-evidence/final/layer-finished_host-hidden.png
