mckayreedmoore/mini-moonboard/docs/wood-joints-mvp/hypotheses/wj24-viewer-review/browser-evidence/final/mobile-390.png

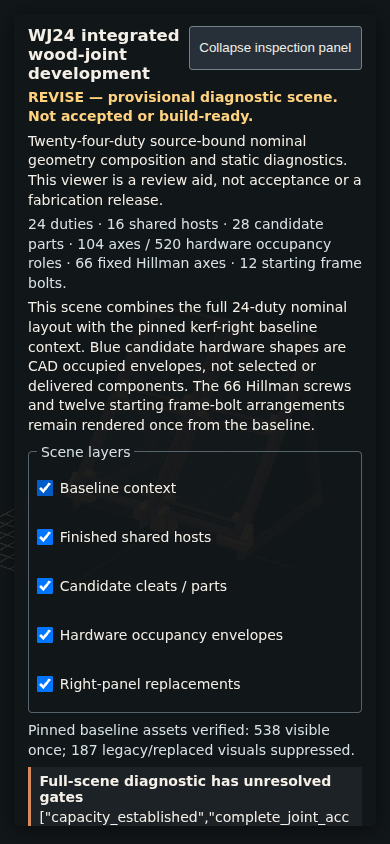
docs/wood-joints-mvp/hypotheses/wj24-viewer-review/browser-evidence/final/mobile-390.png
