mckayreedmoore/mini-moonboard/docs/wood-joints-mvp/hypotheses/wj24-viewer-review/browser-evidence/intermediate/mobile-collapsed-before-final-resize.png

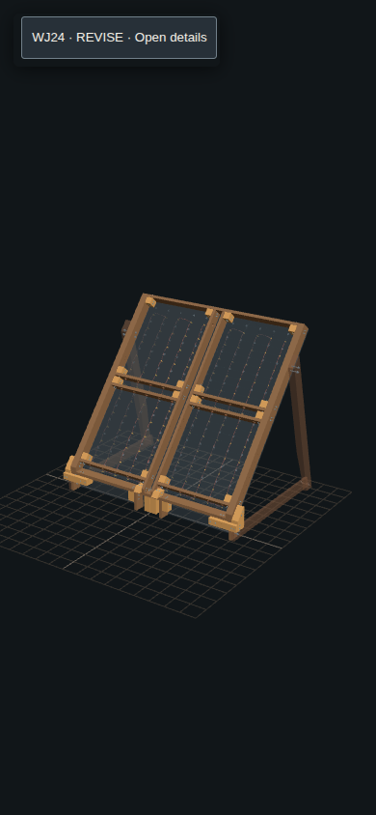
docs/wood-joints-mvp/hypotheses/wj24-viewer-review/browser-evidence/intermediate/mobile-collapsed-before-final-resize.png
