mckayreedmoore/mini-moonboard/exports/base-bearing-concept/base-bearing-concept_front.png

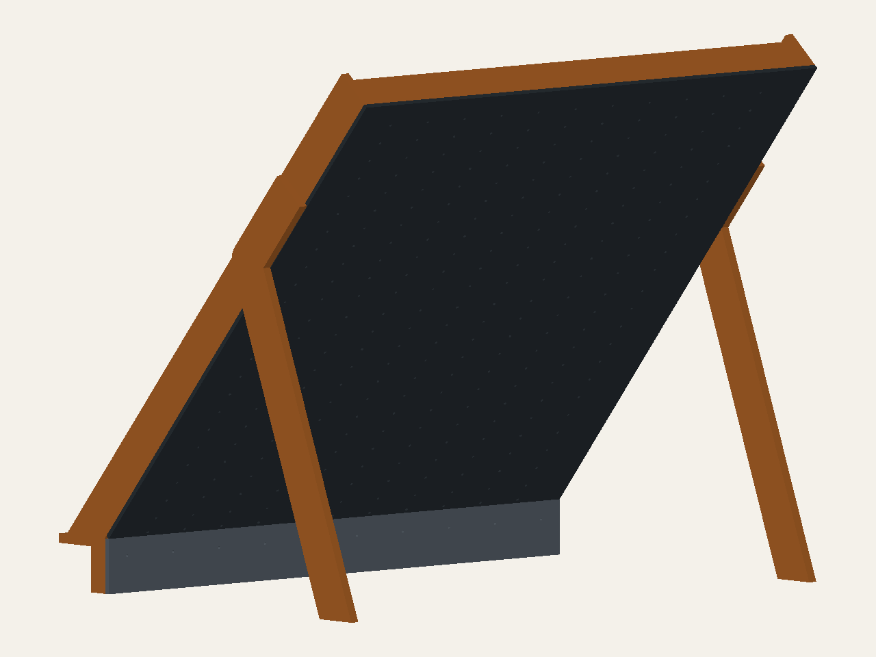
exports/base-bearing-concept/base-bearing-concept_front.png
