mckayreedmoore/mini-moonboard/exports/footprint-frame/2x8-foot100_rear.png

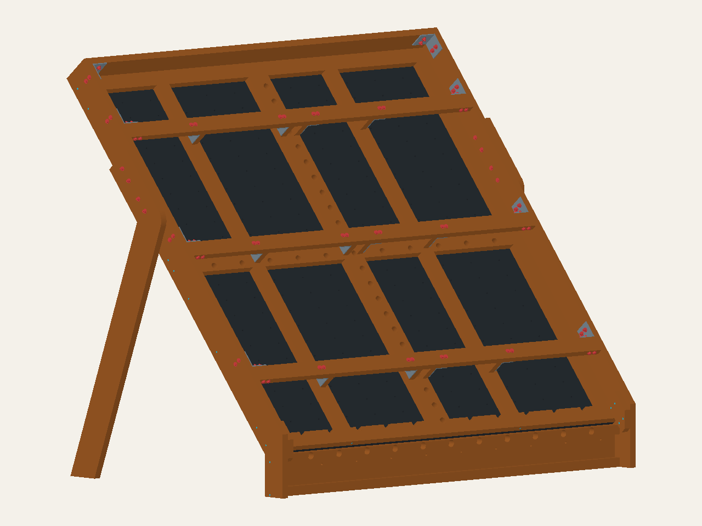
exports/footprint-frame/2x8-foot100_rear.png
