mckayreedmoore/mini-moonboard/exports/hybrid-full/2x10_front.png

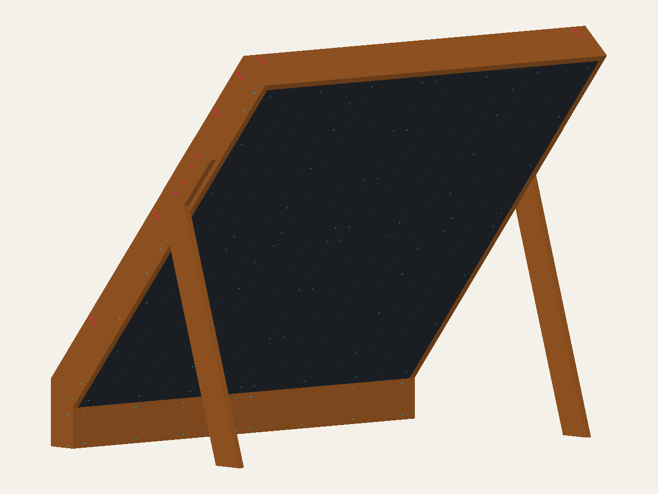
exports/hybrid-full/2x10_front.png
