mckayreedmoore/mini-moonboard/exports/panel-plate-trial/section.png

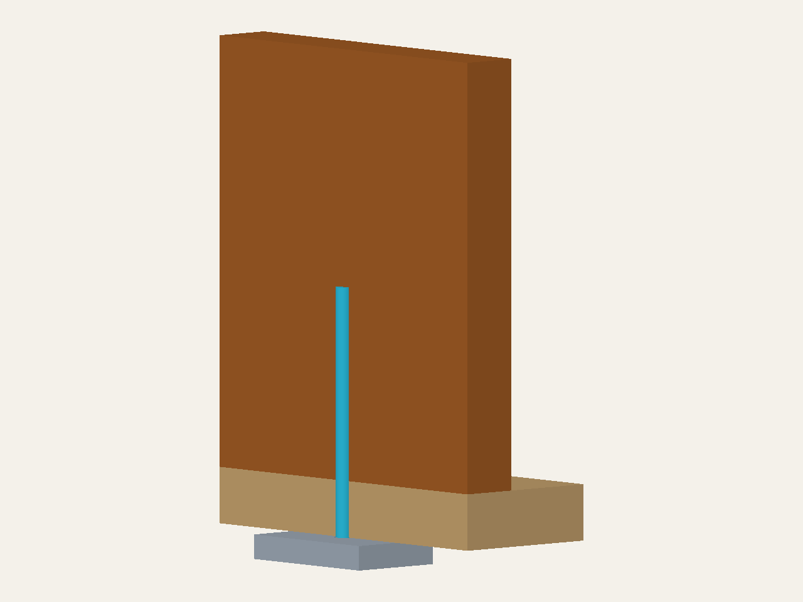
exports/panel-plate-trial/section.png
