mckayreedmoore/mini-moonboard/exports/round-insert-development/base-connection.png

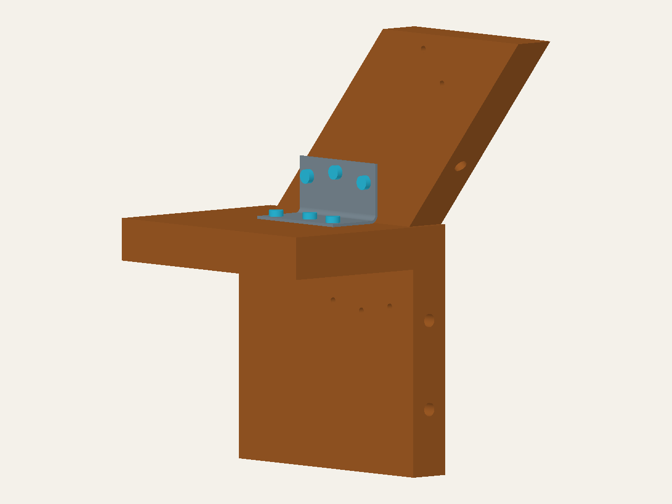
exports/round-insert-development/base-connection.png
