mckayreedmoore/mini-moonboard/exports/round-insert-development/bolt-ends-cutaway.png

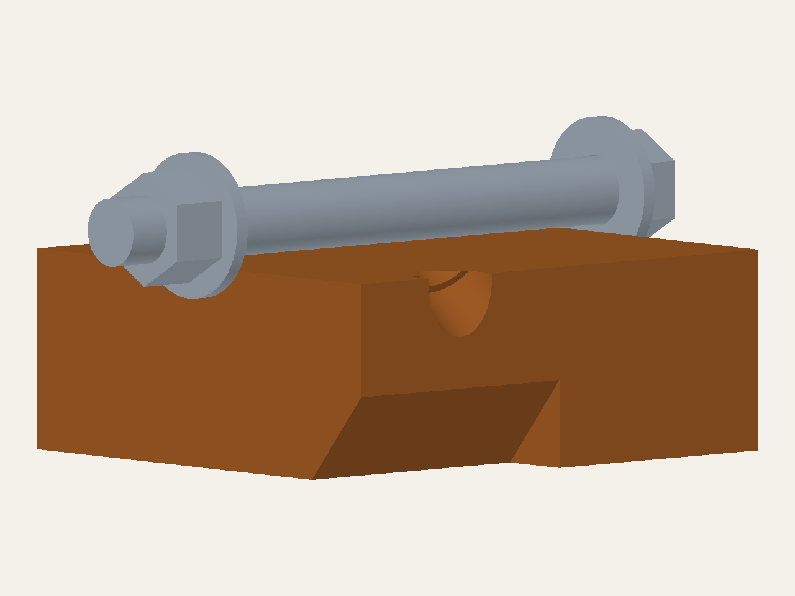
exports/round-insert-development/bolt-ends-cutaway.png
