mckayreedmoore/mini-moonboard/exports/round-insert-development/open-frame.png

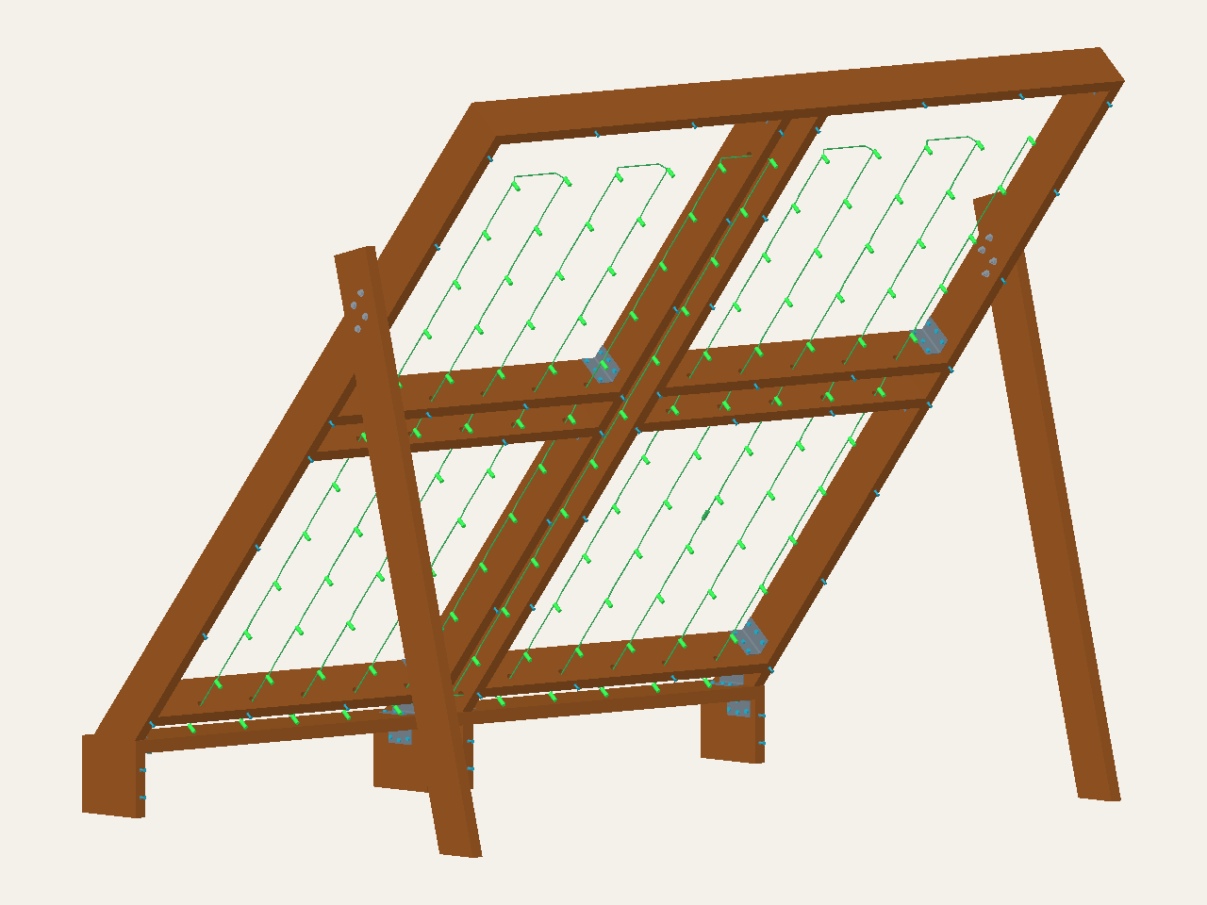
exports/round-insert-development/open-frame.png
