mckayreedmoore/mini-moonboard/docs/current-panel-screw-purchase.md

# Purchased panel screw record

The owner purchased Lowe's item 755741, Fas-n-Tite/Hillman model 42605,
UPC 00038902075949, for the 66 panel and kicker attachment locations in
`compact-floor-flush-development`. The retailer identifies it as a #10 ×
2 1/2-inch carbon-steel exterior deck screw with a gray ceramic coating, coarse
thread, flat head and #2 Phillips drive. It is sold for wood-to-wood use and is
listed as compatible with ACQ, CA and CCA treated lumber.

This purchase does not replace any of the 144 Simpson SDS25112 screws installed
through the 24 ML24Z angles. It therefore neither supplies nor changes the
missing ML24Z separation or force-parallel-couple resistance.

## Current disposition

The purchased screw is selected for the 66 attachments within the owner's
accepted panel-construction scope. Public product information does not provide
actual major/root/shank or head dimensions, thread length, bending yield,
withdrawal, lateral, head-pull-through or plywood-specific design values.
Hillman states in its product Q&A that no tensile-strength rating is listed for
this product. Do not transfer values from SPAX or from other Hillman
structural-screw families.

CAD axis intersections confirm that all 66 screws enter the 139.7 mm wide
dimension of their nominal 2x6 receivers. A 63.5 mm screw through the assumed
18.25625 mm panel has 45.24375 mm nominal timber penetration and terminates
94.45625 mm before the receiver's rear face. No rear tip projection occurs.

The current viewer now shows 66 nominal-length Hillman 42605 screw visuals,
using nominal #10 body diameter. Actual head, thread and pilot dimensions are
unpublished and not represented. Historical archives retain their own SPAX
stiffness assumptions; fresh floor-runner cases use the recorded proxy
connection stiffness, not invented model 42605 stiffness or resistance.
This is not a claim that model 42605 has SPAX resistance or stiffness.

The owner has selected a **lead-hole pilot plus plywood-face countersink** for
all 66 axes so the flat head seats flush. The chosen tool is Lowe’s item
1208451, Kobalt 80277, a 4-piece countersink/twist set. Retailer copy lists
#6 (3/32 in), #8 (7/64 in), **#10 (1/8 in pilot)** and #12 (1/8 in) inserts;
the matching #10 bit is also sold as 1/8 in pilot with a **3/8 in
countersink**. Use the **#10 / 1/8 in** insert on Hillman 42605. That is an
owner tool choice labeled for #10 wood screws, not a Hillman structural value
and not a transfer of SPAX “no lead holes.” Occupied CAD 4.1402 mm is not the
pilot. The hole remains a lead hole. Do not use this 1/8 in insert for
SDS25112 (those use 5/32 in through the ML24Z). Record the offcut trial on the
[shop checklist](floor-flush-shop-checklist.md) before the 66 production holes.

Sources also include:

- [Kobalt 4-piece countersink set, Lowe’s 1208451](https://www.lowes.com/pd/Kobalt-4-Piece-1-8-in-x-1-5-8-in-High-Speed-Steel-Twist-Drill-Bit-Set/1208451)

Sources:

- [Lowe's product listing](https://www.lowes.com/pd/Hillman-10-x-2-1-2-in-Ceramic-Deck-Screws-50-Count/999995042)
- [Hillman response stating that no tensile-strength rating is listed](https://www.lowes.com/questions/fas-n-tite-42605-deck-screws/999995042/f4fd545e-48c7-5ada-90ea-db1169f463ee)
