mckayreedmoore/mini-moonboard/fea/results/diagnostics/wj04-full-stock-patch-geometry-v1/wood/wj04_lower_full_stock_cleat.step

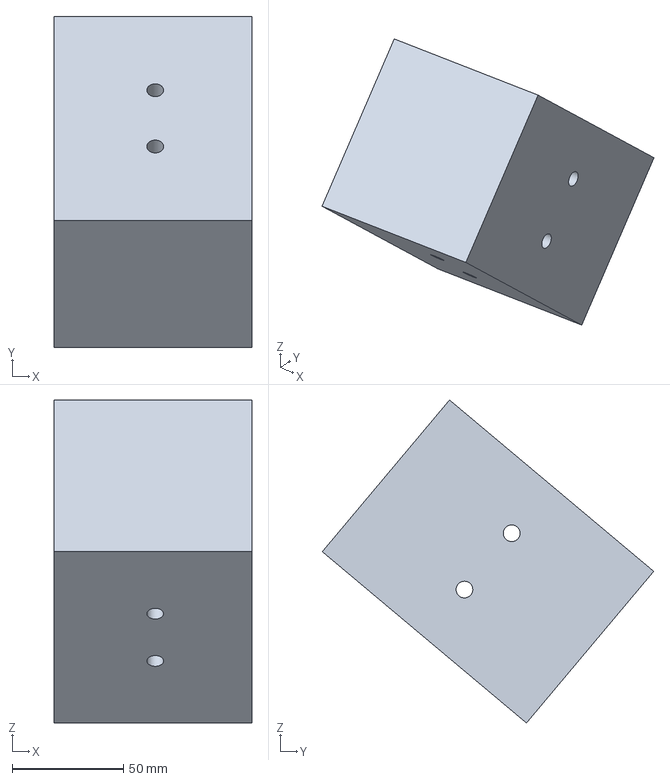
[picture p40: CAD file, 2026-09-25]
fea/results/diagnostics/wj04-full-stock-patch-geometry-v1/wood/wj04_lower_full_stock_cleat.step
88.9 x 148.8 x 145.0 mm
