mckayreedmoore/mini-moonboard/site/hybrid/lower-transition-development/models/transition_main_angle_right.stl

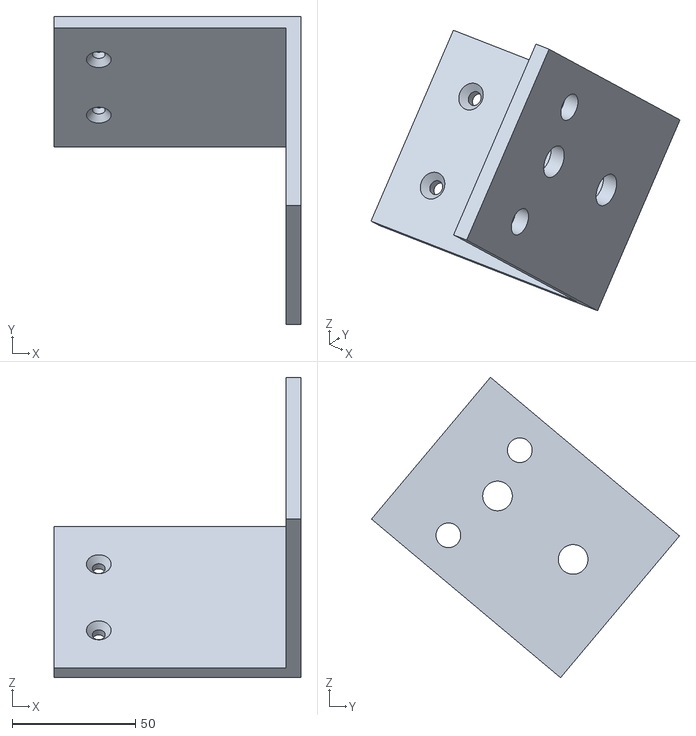
[picture p41: CAD file, 2026-09-07]
site/hybrid/lower-transition-development/models/transition_main_angle_right.stl
100.0 x 124.8 x 121.7
