mckayreedmoore/mini-moonboard/site/hybrid/bearing-lean-frame/models/lean_beam_lower_full.stl

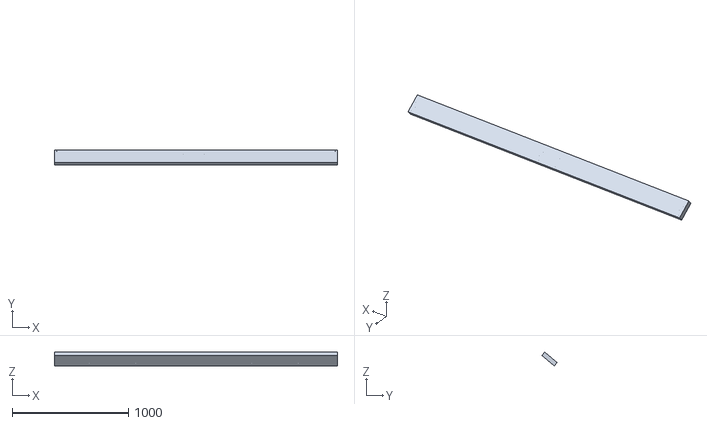
[picture p42: CAD file, 2026-09-08]
site/hybrid/bearing-lean-frame/models/lean_beam_lower_full.stl
2438.4 x 131.5 x 119.0
