mckayreedmoore/mini-moonboard/site/hybrid/compact-floor-flush-kerf-right/models/hold_tnut_main_E2.stl

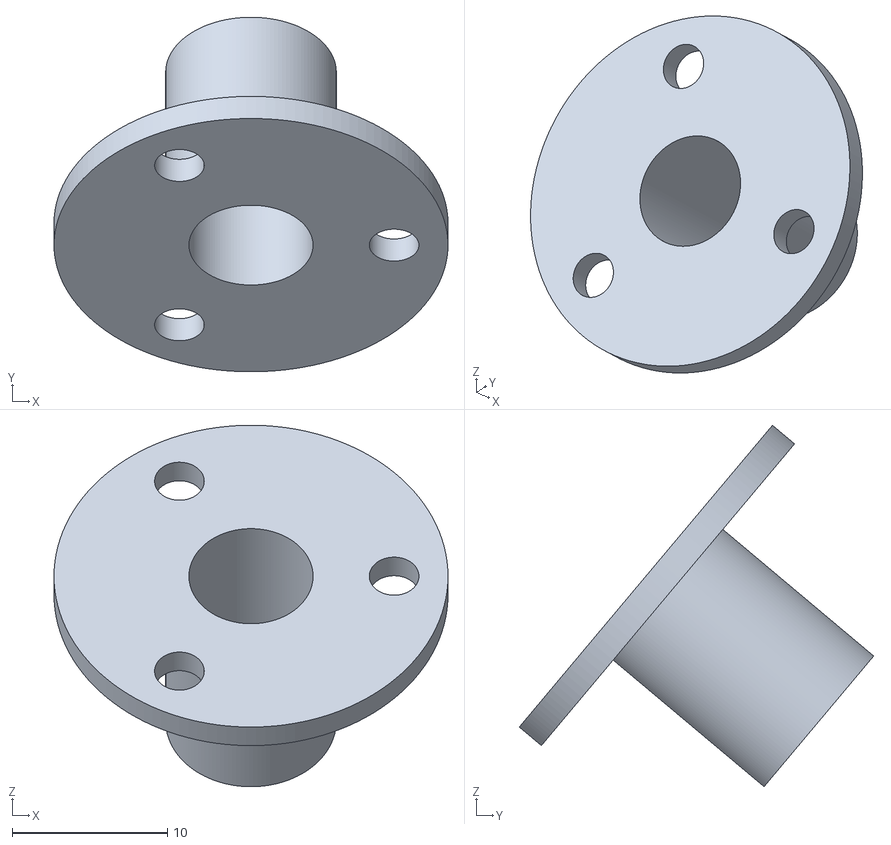
[picture p43: CAD file, 2026-09-13]
site/hybrid/compact-floor-flush-kerf-right/models/hold_tnut_main_E2.stl
25.4 x 22.8 x 23.3
