mckayreedmoore/mini-moonboard/docs/floor-flush-build-package.md

# Flush-end floor-beam revision

**Mechanics applicability:** the current model relocates two split-center header
clips from Y=-135 to Y=-124.9 mm (10.1 mm). Numerical pass statements below describe the
preceding clip stations in the frozen six-case evidence. Current-layout mechanics
are unverified. See the [checked applicability record](current-candidate-status.md)
and [exact disclosure](../current-candidate-applicability.json). The selected
candidate identity is unchanged; no historical pass or fabrication release transfers.

Selected DIY frame. See the [shop checklist](floor-flush-shop-checklist.md) for
cut and inspect steps.

Current work is governed by the [floor-runner MVP master
plan](floor-runner-mvp-master-plan.md) and [frozen criteria
ledger](floor-runner-mvp-criteria.md). [Six fresh no-slip cases](floor-runner-mvp-evidence.json)
converge and meet all 36 frozen checks. The [24-angle ledger](floor-runner-mvp-angle-demands.json)
records unlisted separation and parallel-couple demands without assigning
catalog capacity. The finite-friction A12-left result below is historical.
The [completion ledger](floor-runner-mvp-completion-ledger.md) separates
calculated and nominal artifact evidence from browser checks, installation
observations and analytical limitations.

`compact-floor-flush-development` implements the owner's requested finish of
`compact-floor-taper-development`: floor-runner front ends terminate at the
outer-post plane; rear ends follow the rear legs' inclined back faces. Lower
rim ends terminate at the post/header plane, and leg tops terminate at the
rear faces of the rims. Whole kicker panels and the 1:12 leg recess remain.

The old 7 mm rim-end and 18 mm leg-top reserves are removed. Current
receiver/placement, end-cut/bearing, bracket listed-force, floor contact and
assembled-response checks are documented in the six-case evidence. The
preserved taper cases do not qualify this revision. Existing bracket stations are retained. Front and rear runner bolt
pairs are also relocated to preserve end distances within the shortened beams.
The upper bolt pair is relocated downward and slightly rotated within the
joined timber, retaining 56 mm pitch. Current forces support the adopted
force-directed edge and connection checks under the frozen criteria.

Work tracking is in the [floor-runner MVP master plan](floor-runner-mvp-master-plan.md).
Check delivered bolts and lumber against the shop checklist; a passing
calculation does not skip that.

## Workshop planning and procurement

The [candidate-specific assembly guide](floor-flush-assembly-guide.md) and
[shop checklist](floor-flush-shop-checklist.md) consolidate the 20 timber
pieces, six panels, 24 angles, 144 angle screws, 66 panel screws and twelve
complete bolt stacks. They record the current cut datums, hole-type
instructions, saw options, delivered-hardware checks and proposed assembly
order. Use them with the matching
[construction sheets](floor-flush-construction/). Fill inspection cells when
you see the real parts.

If you **buy 4×4** plywood, use
[https://github.com/mckayreedmoore/mini-moonboard/tree/master/docs/floor-flush-construction](https://github.com/mckayreedmoore/mini-moonboard/tree/master/docs/floor-flush-construction).
If you **cut 4×8** sheets, use
[https://github.com/mckayreedmoore/mini-moonboard/tree/master/docs/floor-flush-construction-kerf-right](https://github.com/mckayreedmoore/mini-moonboard/tree/master/docs/floor-flush-construction-kerf-right).
See [which plywood packet](https://github.com/mckayreedmoore/mini-moonboard/blob/master/docs/floor-flush-width-option.md).
3D models:
[https://mckayreedmoore.github.io/mini-moonboard/](https://mckayreedmoore.github.io/mini-moonboard/)
and
[https://mckayreedmoore.github.io/mini-moonboard/?model=compact-floor-flush-kerf-right](https://mckayreedmoore.github.io/mini-moonboard/?model=compact-floor-flush-kerf-right).
Do not mix the folders.

## FR-3 shop acceptance rules

FR-3 nominal CAD/shop geometry is complete; these rules make delivered-item
inspection decisions reproducible without claiming a fabrication
release. For each mirrored front runner/post pair, use a registered paired-hole
fixture and accept only finished 39.0–40.0 mm centre pitch, pair midpoint within
0.5 mm of the datum, and each hole within 0.5 mm perpendicular to the pair
line. Reject and reassess otherwise; never elongate holes. Apply the same
receiver, edge/end-distance and maximum-washer-seat checks to all 24 receivers.

Inspect delivered bolts against the recorded budgets: minimum full-body lengths
to first thread transition are 158.928 mm upper, 69.317 mm front and 78.842 mm
rear; extra thread/runout budgets are 1.600, 5.359 and 7.518 mm; and shortest
stack tip budgets beyond the nut are 2.743, 10.033 and 9.017 mm. Measure actual
shank, runout, grip, nut engagement and washer dimensions. Require complete,
flat seating of the maximum washer envelope on sound stock; reject incompatible
hardware or unsupported/rocking seats and do not improvise spacers.

The 1:12 recess must have sound, check-free stock, a smooth continuous
transition, no overcut, and no split or damaged bearing surface. Reject or
reassess defects. Contain all 66 purchased Hillman 42605 panel/kicker screws in
their receivers with no tip protrusion; do not transfer SPAX capacity claims.
Place two 48 × 72 × 5 inch pads side by side with the seam front-to-back; pads
remain non-structural and viewer/layout items. Record those observations on the
[shop checklist](floor-flush-shop-checklist.md); do not fill the form from CAD.

## Historical finite-friction force evidence

The historical finite-friction A12-left case converged with 72 explicit timber face contacts and
18 clearance monitors. Its [assessment](floor-flush-a12-left-assessment.json)
meets 37 of 38 implemented criteria, with bolt lateral ratio 0.8792 and sampled
net-member ratio 0.7488. Its historical rim projected-seat scalar is negative
and now retained as a non-adopted sensitivity. The
[cut-method review](history/flush-cut-method-review.md) and
[taper-method review](history/taper-method-applicability-review.md) preserve earlier
method questions. This historical one-case response does not replace the six
fresh current no-slip cases.

## Initial geometry result

All 24 bolt receivers fit the requested geometry, including complete washer
seats. This does not establish joint resistance. The lower rim ends have
102.805 mm retained normal depth. The historical quarter-depth projected-seat
screen has a **negative 4.970 mm margin** on both rims. It remains recorded as
a non-adopted sensitivity because its mapping to this supported terminal bevel
was not established. Adopted retained-section, bearing, contact and gross/net
checks are frozen in the [criteria ledger](floor-runner-mvp-criteria.md).
With the original upper axes, the upper leg bolt had only 67.102 mm adjusted
distance to the newly flush end. The revised pair addresses that geometric
shortfall; the old force response does not establish its resistance.

The complete bracket envelopes remain within the header footprint. Listed
SDS/ML24Z force interactions pass in all six current cases; unlisted separation
and couple actions are disclosed, not manufacturer-qualified.

## Relocated upper bolt layout

Both sides use the same Y/Z positions, mirrored only through the board width.
The pair centre is Y = 1134.25 mm, Z = 1761.5 mm in assembly coordinates. Its
56 mm separation follows the normalized Y/Z direction (18, 53). This is fresh
stock drilling; do not add these holes to timber drilled for an older pattern.
The candidate retains four half-inch upper bolts and twelve bolt stacks total.

Layout screening uses 7D end distances with the existing 3 mm inward-boundary
allowance, 4D on both rear-leg depth edges, and the preceding six cases' rim
load direction (4D loaded, 1.5D unloaded). Current joint forces and directional
edge checks are recorded in the six-case evidence. A screen assuming 4D on both rim edges is more restrictive
and is not claimed to pass for this pair.

## Relocated runner bolt layouts

Front pair: centre Y = -91.5625 mm, Z = 84.1375 mm, with 39.5 mm spacing
along the normalized Y/Z direction (1, 1). Rear pair: Y/Z = (1551, 69) and
(1517, 97.5) mm. Both sides mirror these locations through the board width.
Both runner pairs are screened for 7D end distances, 4D on both depth edges
and at least 4D pair spacing, with the existing 3 mm boundary allowance.
Bolt lengths and wood grips are unchanged. Current joint force, local
resistance and receiver-fit checks are recorded; delivered bolt dimensions
and finished-hole positions remain inspection conditions.

## Preserved construction basis

Solid 4x6 legs and rims, compact 2x6 header/posts, two full 2x6 outboard runners,
66 panel/kicker screws and twelve complete bolt stacks remain. Upper bolts
retain 56 mm pitch. The main-face datum remains 277 mm above the floor, including
127 mm pad allowance and 150 mm exposed kicker. Two 48 x 72 x 5-inch crash pads
sit side by side with their centre seam running front to back. They remain
separate from the structural assembly and weight.

The [preceding taper hardware requirements](floor-runner-taper-hardware.md)
provide the initial bolt specification: four half-inch x 8-inch upper bolts,
four three-eighths x 4-inch front bolts and four three-eighths x 4.5-inch rear
bolts. Actual shank coverage, nut seating and washers must meet the documented
conditions; those specifications alone do not qualify the shortened ends.

Previous tapered and exterior-brace designs remain available as historical
comparisons. Use the model identifier, not a generic "floor beam" label, to
identify a drawing or analysis.
