mckayreedmoore/mini-moonboard/docs/round-reinforcement-browser/assembly-rear.png

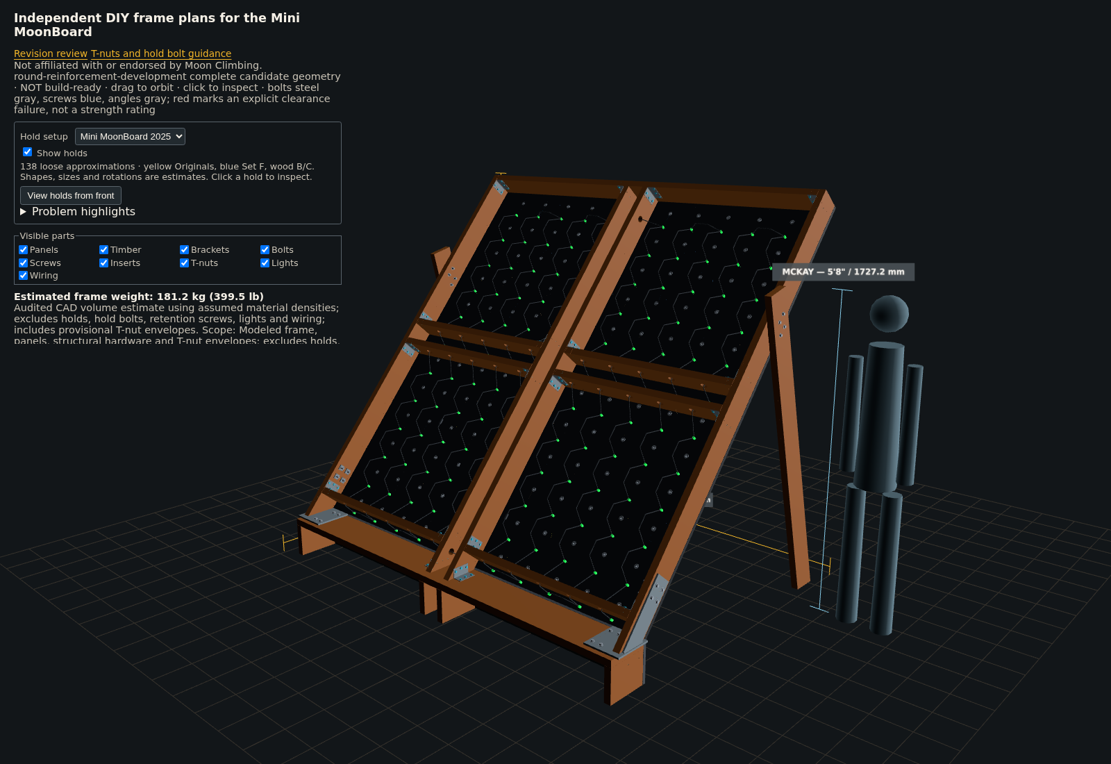
docs/round-reinforcement-browser/assembly-rear.png
