mckayreedmoore/mini-moonboard/fea/results/clear-space-exterior-trials/README.md

# Superseded exterior-brace trial

The first exterior brace used the preceding 40 mm splice-pair spacing. Its first actual native case passed strength but failed the thicker 4x6 member spacing comparison by 7.625 mm. Preserve this as a failed geometric trial; it does not qualify the revised splice.

The revised 51 mm splice A12-left run seeded from the forward case repeated a contact set without convergence. `contact-seeded-a12-left` retains that numerically rejected diagnostic; it is excluded from current case acceptance. A fresh-contact retry uses identical geometry, loads, material properties and numerical limits.

The all-contact cold start also cycled (`contact-cold-a12-left`). The existing one-contact-per-floor-body strategy subsequently cycled too; its final rejected result is retained as the current exterior A12-left diagnostic. No numerical tolerances or physical stiffnesses were relaxed. The exterior branch remains unaccepted; the completed floor-rail route is unaffected.
