mckayreedmoore/mini-moonboard/fea/results/clear-space-floor-trials/README.md

# Superseded floor-rail trials

The 1910 mm trial exceeded the retained member slenderness limit. The subsequent
1880 mm trials included floor rails and their kicker cutouts in CAD but retained
full rectangular kicker panels in the native idealization. These are diagnostic
iterations only. They do not qualify the actual notched kicker assembly; use the
new explicit-cutout cases in `../clear-space-floor`.
