mckayreedmoore/mini-moonboard/docs/wood-joints-mvp/hypotheses/evaluation-resume-2026-09-24/README.md

# Evaluation resumed on the reviewed geometry

The owner explicitly approved resuming joint evaluation after reviewing
`led-clearance-2x6-runner-seated-blocks-v1`, commit `b1e8707d`. The current
[geometry snapshot](geometry-snapshot.json) binds 40 changed timber/block
solids and 92 candidate bolt stacks to the saved scene and report. It is an
input snapshot, not a geometry or structural pass. Four unchanged source
frame timbers and the panels remain in the complete scene; the 40-member
snapshot is not the full board inventory.

Thirteen newly assigned Luna/max workers and reused review workers cover
fastener geometry, receivers, access, retained frame bolts, loads and mechanics
methods. The available thread slots have been used for implementation and
independent review. The parent owns current CAD, input freezing, integration
and serialized native execution. Completed reviews do not need to remain busy
when their dependent inputs are not ready.

## Completed evaluation checkpoints

- [Current rigid-motion preflight](ordinary-rigid-preflight-attempt01/README.md):
  the declared maximum-restraint, closed-face tangent still has 52 free
  rigid-body motions after six global gauges. The timber projection spans
  four independent motions, including slip; accessory spins are distinct.
  Independent matrix reconstruction agrees. Open bolt-hole clearances and
  assumed axial engagement do not define a unique initial force-controlled
  stiffness. This diagnoses the stated model, not failure of the assembled
  board. Clearance seating and engagement must be represented before general
  current-joint response can be interpreted.
- [Current contact classification](ordinary-patch-contact-classification-attempt01/README.md):
  three wood interfaces, sixteen hardware seats and sixteen open radial bore
  walls are classified. Four displayed nuts have no internal bore, so their
  solid interiors cannot supply physical metal occupancy or thread behavior.
  Mesh-area lumping and its geometric tolerance remain separate from response
  accuracy. Complete contact and engagement laws are still pending.
- [Current material map](ordinary-patch-materials-attempt01/README.md):
  source-bound grain and elastic scenarios now cover the nineteen mesh owners,
  with two radial/tangential alternatives and explicitly limited nut branches.
  Four focused tests pass, including reading authenticated mesh artifacts from
  the archive on a fresh checkout. These are input assignments, not native
  response or measured material properties.
- [Complete timber/panel contact graph](../../current-contact-graph.md):
  all 44 timbers and six panels are inventoried, with all 1,225 unordered
  member pairs classified. The 147 exact BRep candidates yield 115 finite
  opposed face contacts and no positive-volume overlaps; six tangencies have
  no finite bearing area. All 92 candidate bolt, twelve retained frame bolt,
  and 66 panel-screw memberships reconcile. Attempt 02 corrects one unchanged
  plywood panel's kind label; pair geometry and contact states are unchanged.
  Graph connectivity does not establish force transfer or capacity.
- [Scalar axial MPC benchmark](axial-mpc-benchmark-attempt01/parent-audit.json):
  the independent guided elastic-bar fixture reproduces the 0.005 mm
  extension under 1,000 N, the area-weighted force transfer and all 32 stress
  and strain integration-point values within its frozen tolerances. Fixture
  support forces and moments balance the applied load. This validates one
  numerical axial mean constraint, not physical thread engagement or current
  joint response. The reference node's printed RF is zero; the independently
  checked bolt-face forces carry the transfer and must not be double-counted
  as additional external load.
- [Current ordinary-joint mesh audit](ordinary-patch-mesh-attempt02/parent-audit.json):
  the pinned Gmsh run completed in 13.50 seconds and produced 19 disjoint body
  owners, 116,162 nodes and 57,643 C3D10 elements. Independent saved-deck
  reconstruction verifies exterior TRI6 ownership and all 807,002 Gauss5
  Jacobians as positive. Maximum relative body-volume error is
  `5.6912050e-5` (about 0.0057%). The two distortion warnings precede high-order
  optimization; the audit checks the final deck. Attempt 01 preserves a
  container-launch failure because the image has `python3`, not `python`.
  This establishes mesh geometry at the sampled integration points only;
  contact behavior, materials, response and capacity remain unaccepted.
  Subsequent classification identifies the four nuts as solid display
  envelopes without internal bores; their physical mechanics representation
  remains unresolved despite successful meshing.
- [Current ordinary-joint inputs](ordinary-patch-inputs-attempt01/inventory.json):
  exact STEP export of the bottom-center right cleat, rail and principal,
  four current bolt stacks and all three finite wood contacts. The 27 STEP
  artifacts preserve the 20 source hardware roles and four verified
  head/shaft unions; the physical mesh inventory is three wood and sixteen
  metal bodies. The exporter uses current live axis datums rather than stale
  historical stack rows. All artifact hashes and eight focused exporter tests
  pass. These are geometry inputs, not contact laws or joint response.
- [Geometry replay](geometry-replay-audit.json): the current construction
  entrypoint reproduces 683 shape metric records, and all 40 changed finished
  timber/block solids have negligible symmetric difference from the reviewed
  live geometry. This reuses the live historical starting assembly; it does
  not claim a new from-scratch composition or full viewer-report reproduction.
- [Receiver screen](receiver-screen-attempt04.json): all 66 modeled screw
  envelopes intersect their raw receivers. The 22 checked panel/receiver
  pairs and 52 named frame/block interfaces have finite planar contact.
  These measurements do not prove screw engagement, force transfer or
  continuous backing beneath the central kicker seam. Attempts 01–03 remain
  as development evidence; attempt 01 was rejected for double translation.
- [Contact-output benchmark](contact-benchmark-attempt01/reaudit02/audit-record.json):
  both native cases completed and the corrected auditor passes their frozen
  outputs, including the 100 N force, moment, location and fixture equilibrium.
  The original parser rejection and all raw outputs are preserved. This is
  a solver-output method check, not a candidate-joint solve or capacity result.
- [Current load contract](current-load-cases.json): six load cases use the
  explicitly extracted [current face and midplane datums](current-load-datums.json).
  These are applied forces and moments, not member demands or reactions.
- [Access screen](access-screen-attempt03-exact-components.json): all 92
  candidate stacks were screened against 1,231 live scene obstacles. Exact
  source-cylinder and annular-cylinder sweeps remove most intersections from
  attempt02's box enclosures. All shaft/head/head-washer withdrawal paths are
  clear in this CAD screen; four nut and two nut-washer axial-slide paths
  retain overlaps. Provisional wrench results are unchanged. The twelve
  retained frame-bolt operations, real tools, capture and full staging remain
  outside this result. No geometry changed during the screen.
- [Grip screen](grip-screen-attempt02.json): all 92 finite shaft envelopes
  cover the independent long-probe intersections with their raw receivers
  and span their modeled nut envelopes. Twenty-eight axes, including all 16
  priority axes, lack an exact match to the existing partial-thread length
  comparators. This does not select a purchased bolt or establish actual
  shank length, thread transition or engagement.

The historical representative mesh and contact inputs predate the current
24-block, 92-axis geometry. Current receiver and joint evidence must be
regenerated or explicitly reconciled before use. All release flags remain
false. The original selected angle-frame authority is unchanged.
