mckayreedmoore/mini-moonboard/docs/wood-joints-mvp/hypotheses/evaluation-resume-2026-09-24/ordinary-contact-iteration-audit-attempt01/endpoint-pair-counts.csv

pair_id | category | master_owner | slave_owner | first_aligned_step | first_aligned_increment | first_aligned_attempt | first_aligned_iteration | last_aligned_step | last_aligned_increment | last_aligned_attempt | last_aligned_iteration | first_aligned_contact_element_count | last_aligned_contact_element_count | count_delta
base_rail_bottom_right_to_base_principal_center_right::wood_to_wood | wood_wood_finite_interface | W02_BASE_PRINCIPAL_CENTER_RIGHT | W01_BASE_RAIL_BOTTOM_RIGHT | 1 | 1 | 1 | 1 | 1 | 1 | 1 | 34 | 1319 | 65 | -1254
bottom_center/clip_horizontal_bottom_right_1/principal_1/head_washer_to_first_receiver | head_washer_to_first_receiver | W00_BOTTOM_CENTER_RIGHT_CLEAT | M09_A02_HEAD_WASHER | 1 | 1 | 1 | 1 | 1 | 1 | 1 | 34 | 5316 | 3115 | -2201
bottom_center/clip_horizontal_bottom_right_1/principal_1/head_washer_to_head | head_washer_to_head | M08_A02_BOLT_HEAD_PLUS_SHAFT_UNION | M09_A02_HEAD_WASHER | 1 | 1 | 1 | 1 | 1 | 1 | 1 | 34 | 7436 | 2394 | -5042
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
