mckayreedmoore/mini-moonboard/docs/wood-joints-mvp/hypotheses/evaluation-resume-2026-09-24/ordinary-contact-iteration-audit-attempt01/iteration-pair-counts.csv

step | increment | attempt | iteration | pair_id | category | master_owner | slave_owner | contact_element_count | active_face_pair_signature_count
1 | 1 | 1 | 1 | base_rail_bottom_right_to_base_principal_center_right::wood_to_wood | wood_wood_finite_interface | W02_BASE_PRINCIPAL_CENTER_RIGHT | W01_BASE_RAIL_BOTTOM_RIGHT | 1319 | 54
1 | 1 | 1 | 1 | bottom_center/clip_horizontal_bottom_right_1/principal_1/head_washer_to_first_receiver | head_washer_to_first_receiver | W00_BOTTOM_CENTER_RIGHT_CLEAT | M09_A02_HEAD_WASHER | 5316 | 242
1 | 1 | 1 | 1 | bottom_center/clip_horizontal_bottom_right_1/principal_1/head_washer_to_head | head_washer_to_head | M08_A02_BOLT_HEAD_PLUS_SHAFT_UNION | M09_A02_HEAD_WASHER | 7436 | 312
1 | 1 | 1 | 1 | bottom_center/clip_horizontal_bottom_right_1/principal_1/nut_washer_to_last_receiver | nut_washer_to_last_receiver | W02_BASE_PRINCIPAL_CENTER_RIGHT | M10_A02_NUT_WASHER | 4381 | 199
1 | 1 | 1 | 1 | bottom_center/clip_horizontal_bottom_right_1/principal_1/nut_washer_to_nut | nut_washer_to_nut | M11_A02_NUT | M10_A02_NUT_WASHER | 6782 | 284
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
