mckayreedmoore/mini-moonboard/docs/wood-joints-mvp/hypotheses/evaluation-resume-2026-09-24/ordinary-contact-iteration-audit-attempt01/pair-switching-transitions.csv

step | increment | attempt | iteration_before | iteration_after | iteration_gap | comparison_status | pair_id | category | master_owner | slave_owner | contact_element_count_before | contact_element_count_after | contact_element_count_delta | retained_face_pair_signature_multiplicity | appeared_face_pair_signature_multiplicity | disappeared_face_pair_signature_multiplicity
1 | 1 | 1 | 1 | 2 | 1 | cvg_aligned | base_rail_bottom_right_to_base_principal_center_right::wood_to_wood | wood_wood_finite_interface | W02_BASE_PRINCIPAL_CENTER_RIGHT | W01_BASE_RAIL_BOTTOM_RIGHT | 1319 | 1241 | -78 | 1059 | 182 | 260
1 | 1 | 1 | 1 | 2 | 1 | cvg_aligned | bottom_center/clip_horizontal_bottom_right_1/principal_1/head_washer_to_first_receiver | head_washer_to_first_receiver | W00_BOTTOM_CENTER_RIGHT_CLEAT | M09_A02_HEAD_WASHER | 5316 | 4715 | -601 | 3303 | 1412 | 2013
1 | 1 | 1 | 1 | 2 | 1 | cvg_aligned | bottom_center/clip_horizontal_bottom_right_1/principal_1/head_washer_to_head | head_washer_to_head | M08_A02_BOLT_HEAD_PLUS_SHAFT_UNION | M09_A02_HEAD_WASHER | 7436 | 7044 | -392 | 4254 | 2790 | 3182
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
