mckayreedmoore/mini-moonboard/docs/wood-joints-mvp/hypotheses/evaluation-resume-2026-09-24/aligned-first-knot-contact-audit-attempt01/pair-contact-forces.csv

pair_index | set_pair | pair_id | category | master_owner | slave_owner | reports_observed | report_state | cf_force_x_n | cf_force_y_n | cf_force_z_n | cf_force_magnitude_n | cf_centroid_x_mm | cf_centroid_y_mm | cf_centroid_z_mm | cf_mean_normal_x | cf_mean_normal_y | cf_mean_normal_z | cf_area_mm2 | cf_normal_force_signed_n | cf_shear_force_magnitude_n | cfn_force_x_n | cfn_force_y_n | cfn_force_z_n | cfn_centroid_xyz_mm | cfn_mean_normal_xyz | cfn_area_mm2 | cfn_normal_force_signed_n | cfn_shear_force_magnitude_n | cfn_duplicate_of_cf | cfs_force_x_n | cfs_force_y_n | cfs_force_z_n | cfs_centroid_xyz_mm | cfs_mean_normal_xyz | cfs_area_mm2 | cfs_normal_force_signed_n | cfs_shear_force_magnitude_n | cfs_force_zero | cf_fields_complete | complete_triplet
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
