mckayreedmoore/mini-moonboard/docs/wood-joints-mvp/hypotheses/evaluation-resume-2026-09-24/aligned-first-knot-penalty-contact-comparison-attempt01/contact-comparison.csv

pair_index | set_pair | pair_id | category | master_owner | slave_owner | quantity | comparison_status | baseline_time_s | child_time_s | baseline_force_vector_n | child_force_vector_n | delta_vector_child_minus_baseline_n | abs_linf_delta_n | baseline_linf_force_n | relative_linf_delta | triage_flag_r_gt_10pct | baseline_report_fields_complete | child_report_fields_complete | baseline_CFN_is_CF_duplicate | child_CFN_is_CF_duplicate | CFN_counted_separately_not_added
1 | WJCP_001 | bottom_center_right_cleat_to_base_rail_bottom_right::wood_to_wood | wood_wood_finite_interface | W01_BASE_RAIL_BOTTOM_RIGHT | W00_BOTTOM_CENTER_RIGHT_CLEAT | CF | matched_force_vector | 0.001 | 0.001 | [9.172473e-17,0.0002489072,0.000296636] | [-1.151316e-17,0.0006217101,0.0007409253] | [-1.0323789e-16,0.00037280289999999997,0.0004442893] | 0.0004442893 | 0.000296636 | 1.4977592065696677 | True | True | True |  |  | False
1 | WJCP_001 | bottom_center_right_cleat_to_base_rail_bottom_right::wood_to_wood | wood_wood_finite_interface | W01_BASE_RAIL_BOTTOM_RIGHT | W00_BOTTOM_CENTER_RIGHT_CLEAT | CFN | matched_force_vector | 0.001 | 0.001 | [9.172473e-17,0.0002489072,0.000296636] | [-1.151316e-17,0.0006217101,0.0007409253] | [-1.0323789e-16,0.00037280289999999997,0.0004442893] | 0.0004442893 | 0.000296636 | 1.4977592065696677 | True | True | True | True | True | True
1 | WJCP_001 | bottom_center_right_cleat_to_base_rail_bottom_right::wood_to_wood | wood_wood_finite_interface | W01_BASE_RAIL_BOTTOM_RIGHT | W00_BOTTOM_CENTER_RIGHT_CLEAT | CFS | matched_force_vector | 0.001 | 0.001 | [0.0,0.0,0.0] | [0.0,0.0,0.0] | [0.0,0.0,0.0] | 0.0 | 0.0 | 0.0 | False | True | True |  |  | False
2 | WJCP_002 | bottom_center_right_cleat_to_base_principal_center_right::wood_to_wood | wood_wood_finite_interface | W02_BASE_PRINCIPAL_CENTER_RIGHT | W00_BOTTOM_CENTER_RIGHT_CLEAT | CF | matched_force_vector | 0.001 | 0.001 | [0.002506931,-8.320125e-18,-2.69594e-18] | [0.0144352,1.535387e-20,1.067087e-19] | [0.011928269,8.33547887e-18,2.8026487000000003e-18] | 0.011928269 | 0.002506931 | 4.75811619865086 | True | True | True |  |  | False
2 | WJCP_002 | bottom_center_right_cleat_to_base_principal_center_right::wood_to_wood | wood_wood_finite_interface | W02_BASE_PRINCIPAL_CENTER_RIGHT | W00_BOTTOM_CENTER_RIGHT_CLEAT | CFN | matched_force_vector | 0.001 | 0.001 | [0.002506931,-8.320125e-18,-2.69594e-18] | [0.0144352,1.535387e-20,1.067087e-19] | [0.011928269,8.33547887e-18,2.8026487000000003e-18] | 0.011928269 | 0.002506931 | 4.75811619865086 | True | True | True | True | True | True
2 | WJCP_002 | bottom_center_right_cleat_to_base_principal_center_right::wood_to_wood | wood_wood_finite_interface | W02_BASE_PRINCIPAL_CENTER_RIGHT | W00_BOTTOM_CENTER_RIGHT_CLEAT | CFS | matched_force_vector | 0.001 | 0.001 | [0.0,0.0,0.0] | [0.0,0.0,0.0] | [0.0,0.0,0.0] | 0.0 | 0.0 | 0.0 | False | True | True |  |  | False
3 | WJCP_003 | base_rail_bottom_right_to_base_principal_center_right::wood_to_wood | wood_wood_finite_interface | W02_BASE_PRINCIPAL_CENTER_RIGHT | W01_BASE_RAIL_BOTTOM_RIGHT | CF | matched_force_vector | 0.001 | 0.001 | [0.007460538,2.348462e-18,1.266474e-18] | [0.008097693,1.190455e-18,1.68472e-18] | [0.0006371549999999995,-1.158007e-18,4.182460000000001e-19] | 0.0006371549999999995 | 0.007460538 | 0.08540335831008428 | False | True | True |  |  | False
3 | WJCP_003 | base_rail_bottom_right_to_base_principal_center_right::wood_to_wood | wood_wood_finite_interface | W02_BASE_PRINCIPAL_CENTER_RIGHT | W01_BASE_RAIL_BOTTOM_RIGHT | CFN | matched_force_vector | 0.001 | 0.001 | [0.007460538,2.348462e-18,1.266474e-18] | [0.008097693,1.190455e-18,1.68472e-18] | [0.0006371549999999995,-1.158007e-18,4.182460000000001e-19] | 0.0006371549999999995 | 0.007460538 | 0.08540335831008428 | False | True | True | True | True | True
3 | WJCP_003 | base_rail_bottom_right_to_base_principal_center_right::wood_to_wood | wood_wood_finite_interface | W02_BASE_PRINCIPAL_CENTER_RIGHT | W01_BASE_RAIL_BOTTOM_RIGHT | CFS | matched_force_vector | 0.001 | 0.001 | [0.0,0.0,0.0] | [0.0,0.0,0.0] | [0.0,0.0,0.0] | 0.0 | 0.0 | 0.0 | False | True | True |  |  | False
4 | WJCP_004 | bottom_center/clip_horizontal_bottom_right_1/rail_1/head_washer_to_head | head_washer_to_head | M00_A00_BOLT_HEAD_PLUS_SHAFT_UNION | M01_A00_HEAD_WASHER | CF | matched_force_vector | 0.001 | 0.001 | [2.016365e-18,-0.0001059173,-0.0001262273] | [2.336692e-18,-0.0002953555,-0.000351991] | [3.2032700000000005e-19,-0.00018943819999999996,-0.00022576370000000002] | 0.00022576370000000002 | 0.0001262273 | 1.7885489113686186 | True | True | True |  |  | False
4 | WJCP_004 | bottom_center/clip_horizontal_bottom_right_1/rail_1/head_washer_to_head | head_washer_to_head | M00_A00_BOLT_HEAD_PLUS_SHAFT_UNION | M01_A00_HEAD_WASHER | CFN | matched_force_vector | 0.001 | 0.001 | [2.016365e-18,-0.0001059173,-0.0001262273] | [2.336692e-18,-0.0002953555,-0.000351991] | [3.2032700000000005e-19,-0.00018943819999999996,-0.00022576370000000002] | 0.00022576370000000002 | 0.0001262273 | 1.7885489113686186 | True | True | True | True | True | True
4 | WJCP_004 | bottom_center/clip_horizontal_bottom_right_1/rail_1/head_washer_to_head | head_washer_to_head | M00_A00_BOLT_HEAD_PLUS_SHAFT_UNION | M01_A00_HEAD_WASHER | CFS | matched_force_vector | 0.001 | 0.001 | [0.0,0.0,0.0] | [0.0,0.0,0.0] | [0.0,0.0,0.0] | 0.0 | 0.0 | 0.0 | False | True | True |  |  | False
5 | WJCP_005 | bottom_center/clip_horizontal_bottom_right_1/rail_1/head_washer_to_first_receiver | head_washer_to_first_receiver | W00_BOTTOM_CENTER_RIGHT_CLEAT | M01_A00_HEAD_WASHER | CF | matched_force_vector | 0.001 | 0.001 | [-1.54321e-17,0.0001065706,0.0001270059] | [-1.408746e-16,0.0002959624,0.0003527143] | [-1.254425e-16,0.00018939180000000002,0.0002257084] | 0.0002257084 | 0.0001270059 | 1.7771489356006296 | True | True | True |  |  | False
5 | WJCP_005 | bottom_center/clip_horizontal_bottom_right_1/rail_1/head_washer_to_first_receiver | head_washer_to_first_receiver | W00_BOTTOM_CENTER_RIGHT_CLEAT | M01_A00_HEAD_WASHER | CFN | matched_force_vector | 0.001 | 0.001 | [-1.54321e-17,0.0001065706,0.0001270059] | [-1.408746e-16,0.0002959624,0.0003527143] | [-1.254425e-16,0.00018939180000000002,0.0002257084] | 0.0002257084 | 0.0001270059 | 1.7771489356006296 | True | True | True | True | True | True
5 | WJCP_005 | bottom_center/clip_horizontal_bottom_right_1/rail_1/head_washer_to_first_receiver | head_washer_to_first_receiver | W00_BOTTOM_CENTER_RIGHT_CLEAT | M01_A00_HEAD_WASHER | CFS | matched_force_vector | 0.001 | 0.001 | [0.0,0.0,0.0] | [0.0,0.0,0.0] | [0.0,0.0,0.0] | 0.0 | 0.0 | 0.0 | False | True | True |  |  | False
6 | WJCP_006 | bottom_center/clip_horizontal_bottom_right_1/rail_1/nut_washer_to_nut | nut_washer_to_nut | M03_A00_NUT | M02_A00_NUT_WASHER | CF | matched_force_vector | 0.001 | 0.001 | [-2.710199e-18,9.888899e-05,0.0001178513] | [-7.903625e-19,0.0002894224,0.0003449202] | [1.9198365000000003e-18,0.00019053341,0.00022706889999999998] | 0.00022706889999999998 | 0.0001178513 | 1.9267407317526406 | True | True | True |  |  | False
6 | WJCP_006 | bottom_center/clip_horizontal_bottom_right_1/rail_1/nut_washer_to_nut | nut_washer_to_nut | M03_A00_NUT | M02_A00_NUT_WASHER | CFN | matched_force_vector | 0.001 | 0.001 | [-2.710199e-18,9.888899e-05,0.0001178513] | [-7.903625e-19,0.0002894224,0.0003449202] | [1.9198365000000003e-18,0.00019053341,0.00022706889999999998] | 0.00022706889999999998 | 0.0001178513 | 1.9267407317526406 | True | True | True | True | True | True
6 | WJCP_006 | bottom_center/clip_horizontal_bottom_right_1/rail_1/nut_washer_to_nut | nut_washer_to_nut | M03_A00_NUT | M02_A00_NUT_WASHER | CFS | matched_force_vector | 0.001 | 0.001 | [0.0,0.0,0.0] | [0.0,0.0,0.0] | [0.0,0.0,0.0] | 0.0 | 0.0 | 0.0 | False | True | True |  |  | False
7 | WJCP_007 | bottom_center/clip_horizontal_bottom_right_1/rail_1/nut_washer_to_last_receiver | nut_washer_to_last_receiver | W01_BASE_RAIL_BOTTOM_RIGHT | M02_A00_NUT_WASHER | CF | matched_force_vector | 0.001 | 0.001 | [-6.583577e-17,-9.828088e-05,-0.0001171266] | [-9.177185e-17,-0.0002889535,-0.0003443613] | [-2.593608e-17,-0.00019067262,-0.0002272347] | 0.0002272347 | 0.0001171266 | 1.940077659558119 | True | True | True |  |  | False
7 | WJCP_007 | bottom_center/clip_horizontal_bottom_right_1/rail_1/nut_washer_to_last_receiver | nut_washer_to_last_receiver | W01_BASE_RAIL_BOTTOM_RIGHT | M02_A00_NUT_WASHER | CFN | matched_force_vector | 0.001 | 0.001 | [-6.583577e-17,-9.828088e-05,-0.0001171266] | [-9.177185e-17,-0.0002889535,-0.0003443613] | [-2.593608e-17,-0.00019067262,-0.0002272347] | 0.0002272347 | 0.0001171266 | 1.940077659558119 | True | True | True | True | True | True
7 | WJCP_007 | bottom_center/clip_horizontal_bottom_right_1/rail_1/nut_washer_to_last_receiver | nut_washer_to_last_receiver | W01_BASE_RAIL_BOTTOM_RIGHT | M02_A00_NUT_WASHER | CFS | matched_force_vector | 0.001 | 0.001 | [0.0,0.0,0.0] | [0.0,0.0,0.0] | [0.0,0.0,0.0] | 0.0 | 0.0 | 0.0 | False | True | True |  |  | False
8 | WJCP_008 | bottom_center/clip_horizontal_bottom_right_1/rail_2/head_washer_to_head | head_washer_to_head | M04_A01_BOLT_HEAD_PLUS_SHAFT_UNION | M05_A01_HEAD_WASHER | CF | matched_force_vector | 0.001 | 0.001 | [-5.74594e-19,-2.670913e-05,-3.183071e-05] | [-3.049677e-18,-0.0002297308,-0.0002737825] | [-2.4750830000000002e-18,-0.00020302167,-0.00024195178999999998] | 0.00024195178999999998 | 3.183071e-05 | 7.601206193641297 | True | True | True |  |  | False
8 | WJCP_008 | bottom_center/clip_horizontal_bottom_right_1/rail_2/head_washer_to_head | head_washer_to_head | M04_A01_BOLT_HEAD_PLUS_SHAFT_UNION | M05_A01_HEAD_WASHER | CFN | matched_force_vector | 0.001 | 0.001 | [-5.74594e-19,-2.670913e-05,-3.183071e-05] | [-3.049677e-18,-0.0002297308,-0.0002737825] | [-2.4750830000000002e-18,-0.00020302167,-0.00024195178999999998] | 0.00024195178999999998 | 3.183071e-05 | 7.601206193641297 | True | True | True | True | True | True
8 | WJCP_008 | bottom_center/clip_horizontal_bottom_right_1/rail_2/head_washer_to_head | head_washer_to_head | M04_A01_BOLT_HEAD_PLUS_SHAFT_UNION | M05_A01_HEAD_WASHER | CFS | matched_force_vector | 0.001 | 0.001 | [0.0,0.0,0.0] | [0.0,0.0,0.0] | [0.0,0.0,0.0] | 0.0 | 0.0 | 0.0 | False | True | True |  |  | False
9 | WJCP_009 | bottom_center/clip_horizontal_bottom_right_1/rail_2/head_washer_to_first_receiver | head_washer_to_first_receiver | W00_BOTTOM_CENTER_RIGHT_CLEAT | M05_A01_HEAD_WASHER | CF | matched_force_vector | 0.001 | 0.001 | [-2.25858e-17,2.745864e-05,3.272393e-05] | [-1.038261e-17,0.000230404,0.0002745848] | [1.2203189999999999e-17,0.00020294536,0.00024186086999999998] | 0.00024186086999999998 | 3.272393e-05 | 7.390948153232205 | True | True | True |  |  | False
9 | WJCP_009 | bottom_center/clip_horizontal_bottom_right_1/rail_2/head_washer_to_first_receiver | head_washer_to_first_receiver | W00_BOTTOM_CENTER_RIGHT_CLEAT | M05_A01_HEAD_WASHER | CFN | matched_force_vector | 0.001 | 0.001 | [-2.25858e-17,2.745864e-05,3.272393e-05] | [-1.038261e-17,0.000230404,0.0002745848] | [1.2203189999999999e-17,0.00020294536,0.00024186086999999998] | 0.00024186086999999998 | 3.272393e-05 | 7.390948153232205 | True | True | True | True | True | True
9 | WJCP_009 | bottom_center/clip_horizontal_bottom_right_1/rail_2/head_washer_to_first_receiver | head_washer_to_first_receiver | W00_BOTTOM_CENTER_RIGHT_CLEAT | M05_A01_HEAD_WASHER | CFS | matched_force_vector | 0.001 | 0.001 | [0.0,0.0,0.0] | [0.0,0.0,0.0] | [0.0,0.0,0.0] | 0.0 | 0.0 | 0.0 | False | True | True |  |  | False
10 | WJCP_010 | bottom_center/clip_horizontal_bottom_right_1/rail_2/nut_washer_to_nut | nut_washer_to_nut | M07_A01_NUT | M06_A01_NUT_WASHER | CF | matched_force_vector | 0.001 | 0.001 | [-7.919551e-19,1.805325e-05,2.151502e-05] | [-1.225942e-19,0.0002228802,0.0002656183] | [6.693609e-19,0.00020482695,0.00024410328] | 0.00024410328 | 2.151502e-05 | 11.345714761129667 | True | True | True |  |  | False
10 | WJCP_010 | bottom_center/clip_horizontal_bottom_right_1/rail_2/nut_washer_to_nut | nut_washer_to_nut | M07_A01_NUT | M06_A01_NUT_WASHER | CFN | matched_force_vector | 0.001 | 0.001 | [-7.919551e-19,1.805325e-05,2.151502e-05] | [-1.225942e-19,0.0002228802,0.0002656183] | [6.693609e-19,0.00020482695,0.00024410328] | 0.00024410328 | 2.151502e-05 | 11.345714761129667 | True | True | True | True | True | True
10 | WJCP_010 | bottom_center/clip_horizontal_bottom_right_1/rail_2/nut_washer_to_nut | nut_washer_to_nut | M07_A01_NUT | M06_A01_NUT_WASHER | CFS | matched_force_vector | 0.001 | 0.001 | [0.0,0.0,0.0] | [0.0,0.0,0.0] | [0.0,0.0,0.0] | 0.0 | 0.0 | 0.0 | False | True | True |  |  | False
11 | WJCP_011 | bottom_center/clip_horizontal_bottom_right_1/rail_2/nut_washer_to_last_receiver | nut_washer_to_last_receiver | W01_BASE_RAIL_BOTTOM_RIGHT | M06_A01_NUT_WASHER | CF | matched_force_vector | 0.001 | 0.001 | [2.006105e-17,-1.722867e-05,-2.053233e-05] | [-9.79279e-18,-0.000222323,-0.0002649542] | [-2.985384e-17,-0.00020509433,-0.00024442187] | 0.00024442187 | 2.053233e-05 | 11.904244184659023 | True | True | True |  |  | False
11 | WJCP_011 | bottom_center/clip_horizontal_bottom_right_1/rail_2/nut_washer_to_last_receiver | nut_washer_to_last_receiver | W01_BASE_RAIL_BOTTOM_RIGHT | M06_A01_NUT_WASHER | CFN | matched_force_vector | 0.001 | 0.001 | [2.006105e-17,-1.722867e-05,-2.053233e-05] | [-9.79279e-18,-0.000222323,-0.0002649542] | [-2.985384e-17,-0.00020509433,-0.00024442187] | 0.00024442187 | 2.053233e-05 | 11.904244184659023 | True | True | True | True | True | True
11 | WJCP_011 | bottom_center/clip_horizontal_bottom_right_1/rail_2/nut_washer_to_last_receiver | nut_washer_to_last_receiver | W01_BASE_RAIL_BOTTOM_RIGHT | M06_A01_NUT_WASHER | CFS | matched_force_vector | 0.001 | 0.001 | [0.0,0.0,0.0] | [0.0,0.0,0.0] | [0.0,0.0,0.0] | 0.0 | 0.0 | 0.0 | False | True | True |  |  | False
12 | WJCP_012 | bottom_center/clip_horizontal_bottom_right_1/principal_1/head_washer_to_head | head_washer_to_head | M08_A02_BOLT_HEAD_PLUS_SHAFT_UNION | M09_A02_HEAD_WASHER | CF | matched_force_vector | 0.001 | 0.001 | [-0.00186622,3.75326e-18,-3.930684e-18] | [-0.007228814,4.229215e-19,-6.531331e-18] | [-0.005362594,-3.3303385000000004e-18,-2.600647e-18] | 0.005362594 | 0.00186622 | 2.873505803174331 | True | True | True |  |  | False
12 | WJCP_012 | bottom_center/clip_horizontal_bottom_right_1/principal_1/head_washer_to_head | head_washer_to_head | M08_A02_BOLT_HEAD_PLUS_SHAFT_UNION | M09_A02_HEAD_WASHER | CFN | matched_force_vector | 0.001 | 0.001 | [-0.00186622,3.75326e-18,-3.930684e-18] | [-0.007228814,4.229215e-19,-6.531331e-18] | [-0.005362594,-3.3303385000000004e-18,-2.600647e-18] | 0.005362594 | 0.00186622 | 2.873505803174331 | True | True | True | True | True | True
12 | WJCP_012 | bottom_center/clip_horizontal_bottom_right_1/principal_1/head_washer_to_head | head_washer_to_head | M08_A02_BOLT_HEAD_PLUS_SHAFT_UNION | M09_A02_HEAD_WASHER | CFS | matched_force_vector | 0.001 | 0.001 | [0.0,0.0,0.0] | [0.0,0.0,0.0] | [0.0,0.0,0.0] | 0.0 | 0.0 | 0.0 | False | True | True |  |  | False
13 | WJCP_013 | bottom_center/clip_horizontal_bottom_right_1/principal_1/head_washer_to_first_receiver | head_washer_to_first_receiver | W00_BOTTOM_CENTER_RIGHT_CLEAT | M09_A02_HEAD_WASHER | CF | matched_force_vector | 0.001 | 0.001 | [0.001858126,8.993298e-19,6.466934e-19] | [0.007223932,5.98167e-19,3.348486e-19] | [0.005365806,-3.011628000000001e-19,-3.118448e-19] | 0.005365806 | 0.001858126 | 2.887751422669937 | True | True | True |  |  | False
13 | WJCP_013 | bottom_center/clip_horizontal_bottom_right_1/principal_1/head_washer_to_first_receiver | head_washer_to_first_receiver | W00_BOTTOM_CENTER_RIGHT_CLEAT | M09_A02_HEAD_WASHER | CFN | matched_force_vector | 0.001 | 0.001 | [0.001858126,8.993298e-19,6.466934e-19] | [0.007223932,5.98167e-19,3.348486e-19] | [0.005365806,-3.011628000000001e-19,-3.118448e-19] | 0.005365806 | 0.001858126 | 2.887751422669937 | True | True | True | True | True | True
13 | WJCP_013 | bottom_center/clip_horizontal_bottom_right_1/principal_1/head_washer_to_first_receiver | head_washer_to_first_receiver | W00_BOTTOM_CENTER_RIGHT_CLEAT | M09_A02_HEAD_WASHER | CFS | matched_force_vector | 0.001 | 0.001 | [0.0,0.0,0.0] | [0.0,0.0,0.0] | [0.0,0.0,0.0] | 0.0 | 0.0 | 0.0 | False | True | True |  |  | False
14 | WJCP_014 | bottom_center/clip_horizontal_bottom_right_1/principal_1/nut_washer_to_nut | nut_washer_to_nut | M11_A02_NUT | M10_A02_NUT_WASHER | CF | matched_force_vector | 0.001 | 0.001 | [0.001952292,-9.452305e-19,-1.327101e-18] | [0.007304073,-8.33021e-20,-1.726521e-18] | [0.005351781,8.619283999999999e-19,-3.9942000000000003e-19] | 0.005351781 | 0.001952292 | 2.741281017388792 | True | True | True |  |  | False
14 | WJCP_014 | bottom_center/clip_horizontal_bottom_right_1/principal_1/nut_washer_to_nut | nut_washer_to_nut | M11_A02_NUT | M10_A02_NUT_WASHER | CFN | matched_force_vector | 0.001 | 0.001 | [0.001952292,-9.452305e-19,-1.327101e-18] | [0.007304073,-8.33021e-20,-1.726521e-18] | [0.005351781,8.619283999999999e-19,-3.9942000000000003e-19] | 0.005351781 | 0.001952292 | 2.741281017388792 | True | True | True | True | True | True
14 | WJCP_014 | bottom_center/clip_horizontal_bottom_right_1/principal_1/nut_washer_to_nut | nut_washer_to_nut | M11_A02_NUT | M10_A02_NUT_WASHER | CFS | matched_force_vector | 0.001 | 0.001 | [0.0,0.0,0.0] | [0.0,0.0,0.0] | [0.0,0.0,0.0] | 0.0 | 0.0 | 0.0 | False | True | True |  |  | False
15 | WJCP_015 | bottom_center/clip_horizontal_bottom_right_1/principal_1/nut_washer_to_last_receiver | nut_washer_to_last_receiver | W02_BASE_PRINCIPAL_CENTER_RIGHT | M10_A02_NUT_WASHER | CF | matched_force_vector | 0.001 | 0.001 | [-0.001960431,2.327811e-20,-3.665115e-20] | [-0.00731259,-3.240626e-19,-1.477413e-19] | [-0.005352159,-3.4734071000000003e-19,-1.1109015e-19] | 0.005352159 | 0.001960431 | 2.7300930254622586 | True | True | True |  |  | False
15 | WJCP_015 | bottom_center/clip_horizontal_bottom_right_1/principal_1/nut_washer_to_last_receiver | nut_washer_to_last_receiver | W02_BASE_PRINCIPAL_CENTER_RIGHT | M10_A02_NUT_WASHER | CFN | matched_force_vector | 0.001 | 0.001 | [-0.001960431,2.327811e-20,-3.665115e-20] | [-0.00731259,-3.240626e-19,-1.477413e-19] | [-0.005352159,-3.4734071000000003e-19,-1.1109015e-19] | 0.005352159 | 0.001960431 | 2.7300930254622586 | True | True | True | True | True | True
15 | WJCP_015 | bottom_center/clip_horizontal_bottom_right_1/principal_1/nut_washer_to_last_receiver | nut_washer_to_last_receiver | W02_BASE_PRINCIPAL_CENTER_RIGHT | M10_A02_NUT_WASHER | CFS | matched_force_vector | 0.001 | 0.001 | [0.0,0.0,0.0] | [0.0,0.0,0.0] | [0.0,0.0,0.0] | 0.0 | 0.0 | 0.0 | False | True | True |  |  | False
16 | WJCP_016 | bottom_center/clip_horizontal_bottom_right_1/principal_2/head_washer_to_head | head_washer_to_head | M12_A03_BOLT_HEAD_PLUS_SHAFT_UNION | M13_A03_HEAD_WASHER | CF | matched_force_vector | 0.001 | 0.001 | [-0.001658325,4.704113e-18,-4.812192e-18] | [-0.007027263,-8.288936e-19,-6.642524e-18] | [-0.005368938,-5.5330066e-18,-1.830332e-18] | 0.005368938 | 0.001658325 | 3.237566821943829 | True | True | True |  |  | False
16 | WJCP_016 | bottom_center/clip_horizontal_bottom_right_1/principal_2/head_washer_to_head | head_washer_to_head | M12_A03_BOLT_HEAD_PLUS_SHAFT_UNION | M13_A03_HEAD_WASHER | CFN | matched_force_vector | 0.001 | 0.001 | [-0.001658325,4.704113e-18,-4.812192e-18] | [-0.007027263,-8.288936e-19,-6.642524e-18] | [-0.005368938,-5.5330066e-18,-1.830332e-18] | 0.005368938 | 0.001658325 | 3.237566821943829 | True | True | True | True | True | True
16 | WJCP_016 | bottom_center/clip_horizontal_bottom_right_1/principal_2/head_washer_to_head | head_washer_to_head | M12_A03_BOLT_HEAD_PLUS_SHAFT_UNION | M13_A03_HEAD_WASHER | CFS | matched_force_vector | 0.001 | 0.001 | [0.0,0.0,0.0] | [0.0,0.0,0.0] | [0.0,0.0,0.0] | 0.0 | 0.0 | 0.0 | False | True | True |  |  | False
17 | WJCP_017 | bottom_center/clip_horizontal_bottom_right_1/principal_2/head_washer_to_first_receiver | head_washer_to_first_receiver | W00_BOTTOM_CENTER_RIGHT_CLEAT | M13_A03_HEAD_WASHER | CF | matched_force_vector | 0.001 | 0.001 | [0.001650365,1.133039e-18,1.07142e-19] | [0.007023787,2.070779e-18,1.468237e-18] | [0.005373422,9.3774e-19,1.3610950000000002e-18] | 0.005373422 | 0.001650365 | 3.255899149582062 | True | True | True |  |  | False
17 | WJCP_017 | bottom_center/clip_horizontal_bottom_right_1/principal_2/head_washer_to_first_receiver | head_washer_to_first_receiver | W00_BOTTOM_CENTER_RIGHT_CLEAT | M13_A03_HEAD_WASHER | CFN | matched_force_vector | 0.001 | 0.001 | [0.001650365,1.133039e-18,1.07142e-19] | [0.007023787,2.070779e-18,1.468237e-18] | [0.005373422,9.3774e-19,1.3610950000000002e-18] | 0.005373422 | 0.001650365 | 3.255899149582062 | True | True | True | True | True | True
17 | WJCP_017 | bottom_center/clip_horizontal_bottom_right_1/principal_2/head_washer_to_first_receiver | head_washer_to_first_receiver | W00_BOTTOM_CENTER_RIGHT_CLEAT | M13_A03_HEAD_WASHER | CFS | matched_force_vector | 0.001 | 0.001 | [0.0,0.0,0.0] | [0.0,0.0,0.0] | [0.0,0.0,0.0] | 0.0 | 0.0 | 0.0 | False | True | True |  |  | False
18 | WJCP_018 | bottom_center/clip_horizontal_bottom_right_1/principal_2/nut_washer_to_nut | nut_washer_to_nut | M15_A03_NUT | M14_A03_NUT_WASHER | CF | matched_force_vector | 0.001 | 0.001 | [0.001737724,1.336152e-18,-2.932207e-19] | [0.007086457,2.054021e-18,1.042318e-18] | [0.005348733,7.178690000000002e-19,1.3355386999999999e-18] | 0.005348733 | 0.001737724 | 3.0780106622225394 | True | True | True |  |  | False
18 | WJCP_018 | bottom_center/clip_horizontal_bottom_right_1/principal_2/nut_washer_to_nut | nut_washer_to_nut | M15_A03_NUT | M14_A03_NUT_WASHER | CFN | matched_force_vector | 0.001 | 0.001 | [0.001737724,1.336152e-18,-2.932207e-19] | [0.007086457,2.054021e-18,1.042318e-18] | [0.005348733,7.178690000000002e-19,1.3355386999999999e-18] | 0.005348733 | 0.001737724 | 3.0780106622225394 | True | True | True | True | True | True
18 | WJCP_018 | bottom_center/clip_horizontal_bottom_right_1/principal_2/nut_washer_to_nut | nut_washer_to_nut | M15_A03_NUT | M14_A03_NUT_WASHER | CFS | matched_force_vector | 0.001 | 0.001 | [0.0,0.0,0.0] | [0.0,0.0,0.0] | [0.0,0.0,0.0] | 0.0 | 0.0 | 0.0 | False | True | True |  |  | False
19 | WJCP_019 | bottom_center/clip_horizontal_bottom_right_1/principal_2/nut_washer_to_last_receiver | nut_washer_to_last_receiver | W02_BASE_PRINCIPAL_CENTER_RIGHT | M14_A03_NUT_WASHER | CF | matched_force_vector | 0.001 | 0.001 | [-0.001744951,-1.253718e-19,7.469477e-20] | [-0.007093492,-2.862612e-19,2.379348e-19] | [-0.005348541,-1.608894e-19,1.6324003e-19] | 0.005348541 | 0.001744951 | 3.0651525458308 | True | True | True |  |  | False
19 | WJCP_019 | bottom_center/clip_horizontal_bottom_right_1/principal_2/nut_washer_to_last_receiver | nut_washer_to_last_receiver | W02_BASE_PRINCIPAL_CENTER_RIGHT | M14_A03_NUT_WASHER | CFN | matched_force_vector | 0.001 | 0.001 | [-0.001744951,-1.253718e-19,7.469477e-20] | [-0.007093492,-2.862612e-19,2.379348e-19] | [-0.005348541,-1.608894e-19,1.6324003e-19] | 0.005348541 | 0.001744951 | 3.0651525458308 | True | True | True | True | True | True
19 | WJCP_019 | bottom_center/clip_horizontal_bottom_right_1/principal_2/nut_washer_to_last_receiver | nut_washer_to_last_receiver | W02_BASE_PRINCIPAL_CENTER_RIGHT | M14_A03_NUT_WASHER | CFS | matched_force_vector | 0.001 | 0.001 | [0.0,0.0,0.0] | [0.0,0.0,0.0] | [0.0,0.0,0.0] | 0.0 | 0.0 | 0.0 | False | True | True |  |  | False
20 | WJCP_020 | bottom_center/clip_horizontal_bottom_right_1/rail_1::bottom_center_right_cleat::shaft_to_wood_bore | open_bolt_shank_to_wood_bore | W00_BOTTOM_CENTER_RIGHT_CLEAT | M00_A00_BOLT_HEAD_PLUS_SHAFT_UNION | CF | matched_force_vector | 0.001 | 0.001 | [0.0,0.0,0.0] | [0.0,0.0,0.0] | [0.0,0.0,0.0] | 0.0 | 0.0 | 0.0 | False | True | True |  |  | False
20 | WJCP_020 | bottom_center/clip_horizontal_bottom_right_1/rail_1::bottom_center_right_cleat::shaft_to_wood_bore | open_bolt_shank_to_wood_bore | W00_BOTTOM_CENTER_RIGHT_CLEAT | M00_A00_BOLT_HEAD_PLUS_SHAFT_UNION | CFN | matched_force_vector | 0.001 | 0.001 | [0.0,0.0,0.0] | [0.0,0.0,0.0] | [0.0,0.0,0.0] | 0.0 | 0.0 | 0.0 | False | True | True | True | True | True
20 | WJCP_020 | bottom_center/clip_horizontal_bottom_right_1/rail_1::bottom_center_right_cleat::shaft_to_wood_bore | open_bolt_shank_to_wood_bore | W00_BOTTOM_CENTER_RIGHT_CLEAT | M00_A00_BOLT_HEAD_PLUS_SHAFT_UNION | CFS | matched_force_vector | 0.001 | 0.001 | [0.0,0.0,0.0] | [0.0,0.0,0.0] | [0.0,0.0,0.0] | 0.0 | 0.0 | 0.0 | False | True | True |  |  | False
21 | WJCP_021 | bottom_center/clip_horizontal_bottom_right_1/rail_1::base_rail_bottom_right::shaft_to_wood_bore | open_bolt_shank_to_wood_bore | W01_BASE_RAIL_BOTTOM_RIGHT | M00_A00_BOLT_HEAD_PLUS_SHAFT_UNION | CF | matched_force_vector | 0.001 | 0.001 | [0.0,0.0,0.0] | [0.0,0.0,0.0] | [0.0,0.0,0.0] | 0.0 | 0.0 | 0.0 | False | True | True |  |  | False
21 | WJCP_021 | bottom_center/clip_horizontal_bottom_right_1/rail_1::base_rail_bottom_right::shaft_to_wood_bore | open_bolt_shank_to_wood_bore | W01_BASE_RAIL_BOTTOM_RIGHT | M00_A00_BOLT_HEAD_PLUS_SHAFT_UNION | CFN | matched_force_vector | 0.001 | 0.001 | [0.0,0.0,0.0] | [0.0,0.0,0.0] | [0.0,0.0,0.0] | 0.0 | 0.0 | 0.0 | False | True | True | True | True | True
21 | WJCP_021 | bottom_center/clip_horizontal_bottom_right_1/rail_1::base_rail_bottom_right::shaft_to_wood_bore | open_bolt_shank_to_wood_bore | W01_BASE_RAIL_BOTTOM_RIGHT | M00_A00_BOLT_HEAD_PLUS_SHAFT_UNION | CFS | matched_force_vector | 0.001 | 0.001 | [0.0,0.0,0.0] | [0.0,0.0,0.0] | [0.0,0.0,0.0] | 0.0 | 0.0 | 0.0 | False | True | True |  |  | False
22 | WJCP_022 | bottom_center/clip_horizontal_bottom_right_1/rail_2::bottom_center_right_cleat::shaft_to_wood_bore | open_bolt_shank_to_wood_bore | W00_BOTTOM_CENTER_RIGHT_CLEAT | M04_A01_BOLT_HEAD_PLUS_SHAFT_UNION | CF | matched_force_vector | 0.001 | 0.001 | [0.0,0.0,0.0] | [0.0,0.0,0.0] | [0.0,0.0,0.0] | 0.0 | 0.0 | 0.0 | False | True | True |  |  | False
22 | WJCP_022 | bottom_center/clip_horizontal_bottom_right_1/rail_2::bottom_center_right_cleat::shaft_to_wood_bore | open_bolt_shank_to_wood_bore | W00_BOTTOM_CENTER_RIGHT_CLEAT | M04_A01_BOLT_HEAD_PLUS_SHAFT_UNION | CFN | matched_force_vector | 0.001 | 0.001 | [0.0,0.0,0.0] | [0.0,0.0,0.0] | [0.0,0.0,0.0] | 0.0 | 0.0 | 0.0 | False | True | True | True | True | True
22 | WJCP_022 | bottom_center/clip_horizontal_bottom_right_1/rail_2::bottom_center_right_cleat::shaft_to_wood_bore | open_bolt_shank_to_wood_bore | W00_BOTTOM_CENTER_RIGHT_CLEAT | M04_A01_BOLT_HEAD_PLUS_SHAFT_UNION | CFS | matched_force_vector | 0.001 | 0.001 | [0.0,0.0,0.0] | [0.0,0.0,0.0] | [0.0,0.0,0.0] | 0.0 | 0.0 | 0.0 | False | True | True |  |  | False
23 | WJCP_023 | bottom_center/clip_horizontal_bottom_right_1/rail_2::base_rail_bottom_right::shaft_to_wood_bore | open_bolt_shank_to_wood_bore | W01_BASE_RAIL_BOTTOM_RIGHT | M04_A01_BOLT_HEAD_PLUS_SHAFT_UNION | CF | matched_force_vector | 0.001 | 0.001 | [0.0,0.0,0.0] | [0.0,0.0,0.0] | [0.0,0.0,0.0] | 0.0 | 0.0 | 0.0 | False | True | True |  |  | False
23 | WJCP_023 | bottom_center/clip_horizontal_bottom_right_1/rail_2::base_rail_bottom_right::shaft_to_wood_bore | open_bolt_shank_to_wood_bore | W01_BASE_RAIL_BOTTOM_RIGHT | M04_A01_BOLT_HEAD_PLUS_SHAFT_UNION | CFN | matched_force_vector | 0.001 | 0.001 | [0.0,0.0,0.0] | [0.0,0.0,0.0] | [0.0,0.0,0.0] | 0.0 | 0.0 | 0.0 | False | True | True | True | True | True
23 | WJCP_023 | bottom_center/clip_horizontal_bottom_right_1/rail_2::base_rail_bottom_right::shaft_to_wood_bore | open_bolt_shank_to_wood_bore | W01_BASE_RAIL_BOTTOM_RIGHT | M04_A01_BOLT_HEAD_PLUS_SHAFT_UNION | CFS | matched_force_vector | 0.001 | 0.001 | [0.0,0.0,0.0] | [0.0,0.0,0.0] | [0.0,0.0,0.0] | 0.0 | 0.0 | 0.0 | False | True | True |  |  | False
24 | WJCP_024 | bottom_center/clip_horizontal_bottom_right_1/principal_1::bottom_center_right_cleat::shaft_to_wood_bore | open_bolt_shank_to_wood_bore | W00_BOTTOM_CENTER_RIGHT_CLEAT | M08_A02_BOLT_HEAD_PLUS_SHAFT_UNION | CF | matched_force_vector | 0.001 | 0.001 | [0.0,0.0,0.0] | [0.0,0.0,0.0] | [0.0,0.0,0.0] | 0.0 | 0.0 | 0.0 | False | True | True |  |  | False
24 | WJCP_024 | bottom_center/clip_horizontal_bottom_right_1/principal_1::bottom_center_right_cleat::shaft_to_wood_bore | open_bolt_shank_to_wood_bore | W00_BOTTOM_CENTER_RIGHT_CLEAT | M08_A02_BOLT_HEAD_PLUS_SHAFT_UNION | CFN | matched_force_vector | 0.001 | 0.001 | [0.0,0.0,0.0] | [0.0,0.0,0.0] | [0.0,0.0,0.0] | 0.0 | 0.0 | 0.0 | False | True | True | True | True | True
24 | WJCP_024 | bottom_center/clip_horizontal_bottom_right_1/principal_1::bottom_center_right_cleat::shaft_to_wood_bore | open_bolt_shank_to_wood_bore | W00_BOTTOM_CENTER_RIGHT_CLEAT | M08_A02_BOLT_HEAD_PLUS_SHAFT_UNION | CFS | matched_force_vector | 0.001 | 0.001 | [0.0,0.0,0.0] | [0.0,0.0,0.0] | [0.0,0.0,0.0] | 0.0 | 0.0 | 0.0 | False | True | True |  |  | False
25 | WJCP_025 | bottom_center/clip_horizontal_bottom_right_1/principal_1::base_principal_center_right::shaft_to_wood_bore | open_bolt_shank_to_wood_bore | W02_BASE_PRINCIPAL_CENTER_RIGHT | M08_A02_BOLT_HEAD_PLUS_SHAFT_UNION | CF | matched_force_vector | 0.001 | 0.001 | [0.0,0.0,0.0] | [0.0,0.0,0.0] | [0.0,0.0,0.0] | 0.0 | 0.0 | 0.0 | False | True | True |  |  | False
25 | WJCP_025 | bottom_center/clip_horizontal_bottom_right_1/principal_1::base_principal_center_right::shaft_to_wood_bore | open_bolt_shank_to_wood_bore | W02_BASE_PRINCIPAL_CENTER_RIGHT | M08_A02_BOLT_HEAD_PLUS_SHAFT_UNION | CFN | matched_force_vector | 0.001 | 0.001 | [0.0,0.0,0.0] | [0.0,0.0,0.0] | [0.0,0.0,0.0] | 0.0 | 0.0 | 0.0 | False | True | True | True | True | True
25 | WJCP_025 | bottom_center/clip_horizontal_bottom_right_1/principal_1::base_principal_center_right::shaft_to_wood_bore | open_bolt_shank_to_wood_bore | W02_BASE_PRINCIPAL_CENTER_RIGHT | M08_A02_BOLT_HEAD_PLUS_SHAFT_UNION | CFS | matched_force_vector | 0.001 | 0.001 | [0.0,0.0,0.0] | [0.0,0.0,0.0] | [0.0,0.0,0.0] | 0.0 | 0.0 | 0.0 | False | True | True |  |  | False
26 | WJCP_026 | bottom_center/clip_horizontal_bottom_right_1/principal_2::bottom_center_right_cleat::shaft_to_wood_bore | open_bolt_shank_to_wood_bore | W00_BOTTOM_CENTER_RIGHT_CLEAT | M12_A03_BOLT_HEAD_PLUS_SHAFT_UNION | CF | matched_force_vector | 0.001 | 0.001 | [0.0,0.0,0.0] | [0.0,0.0,0.0] | [0.0,0.0,0.0] | 0.0 | 0.0 | 0.0 | False | True | True |  |  | False
26 | WJCP_026 | bottom_center/clip_horizontal_bottom_right_1/principal_2::bottom_center_right_cleat::shaft_to_wood_bore | open_bolt_shank_to_wood_bore | W00_BOTTOM_CENTER_RIGHT_CLEAT | M12_A03_BOLT_HEAD_PLUS_SHAFT_UNION | CFN | matched_force_vector | 0.001 | 0.001 | [0.0,0.0,0.0] | [0.0,0.0,0.0] | [0.0,0.0,0.0] | 0.0 | 0.0 | 0.0 | False | True | True | True | True | True
26 | WJCP_026 | bottom_center/clip_horizontal_bottom_right_1/principal_2::bottom_center_right_cleat::shaft_to_wood_bore | open_bolt_shank_to_wood_bore | W00_BOTTOM_CENTER_RIGHT_CLEAT | M12_A03_BOLT_HEAD_PLUS_SHAFT_UNION | CFS | matched_force_vector | 0.001 | 0.001 | [0.0,0.0,0.0] | [0.0,0.0,0.0] | [0.0,0.0,0.0] | 0.0 | 0.0 | 0.0 | False | True | True |  |  | False
27 | WJCP_027 | bottom_center/clip_horizontal_bottom_right_1/principal_2::base_principal_center_right::shaft_to_wood_bore | open_bolt_shank_to_wood_bore | W02_BASE_PRINCIPAL_CENTER_RIGHT | M12_A03_BOLT_HEAD_PLUS_SHAFT_UNION | CF | matched_force_vector | 0.001 | 0.001 | [0.0,0.0,0.0] | [0.0,0.0,0.0] | [0.0,0.0,0.0] | 0.0 | 0.0 | 0.0 | False | True | True |  |  | False
27 | WJCP_027 | bottom_center/clip_horizontal_bottom_right_1/principal_2::base_principal_center_right::shaft_to_wood_bore | open_bolt_shank_to_wood_bore | W02_BASE_PRINCIPAL_CENTER_RIGHT | M12_A03_BOLT_HEAD_PLUS_SHAFT_UNION | CFN | matched_force_vector | 0.001 | 0.001 | [0.0,0.0,0.0] | [0.0,0.0,0.0] | [0.0,0.0,0.0] | 0.0 | 0.0 | 0.0 | False | True | True | True | True | True
27 | WJCP_027 | bottom_center/clip_horizontal_bottom_right_1/principal_2::base_principal_center_right::shaft_to_wood_bore | open_bolt_shank_to_wood_bore | W02_BASE_PRINCIPAL_CENTER_RIGHT | M12_A03_BOLT_HEAD_PLUS_SHAFT_UNION | CFS | matched_force_vector | 0.001 | 0.001 | [0.0,0.0,0.0] | [0.0,0.0,0.0] | [0.0,0.0,0.0] | 0.0 | 0.0 | 0.0 | False | True | True |  |  | False
28 | WJCP_028 | bottom_center/clip_horizontal_bottom_right_1/rail_1::shaft_to_head_washer_bore | open_bolt_shank_to_washer_bore | M01_A00_HEAD_WASHER | M00_A00_BOLT_HEAD_PLUS_SHAFT_UNION | CF | matched_force_vector | 0.001 | 0.001 | [0.0,0.0,0.0] | [0.0,0.0,0.0] | [0.0,0.0,0.0] | 0.0 | 0.0 | 0.0 | False | True | True |  |  | False
28 | WJCP_028 | bottom_center/clip_horizontal_bottom_right_1/rail_1::shaft_to_head_washer_bore | open_bolt_shank_to_washer_bore | M01_A00_HEAD_WASHER | M00_A00_BOLT_HEAD_PLUS_SHAFT_UNION | CFN | matched_force_vector | 0.001 | 0.001 | [0.0,0.0,0.0] | [0.0,0.0,0.0] | [0.0,0.0,0.0] | 0.0 | 0.0 | 0.0 | False | True | True | True | True | True
28 | WJCP_028 | bottom_center/clip_horizontal_bottom_right_1/rail_1::shaft_to_head_washer_bore | open_bolt_shank_to_washer_bore | M01_A00_HEAD_WASHER | M00_A00_BOLT_HEAD_PLUS_SHAFT_UNION | CFS | matched_force_vector | 0.001 | 0.001 | [0.0,0.0,0.0] | [0.0,0.0,0.0] | [0.0,0.0,0.0] | 0.0 | 0.0 | 0.0 | False | True | True |  |  | False
29 | WJCP_029 | bottom_center/clip_horizontal_bottom_right_1/rail_1::shaft_to_nut_washer_bore | open_bolt_shank_to_washer_bore | M02_A00_NUT_WASHER | M00_A00_BOLT_HEAD_PLUS_SHAFT_UNION | CF | matched_force_vector | 0.001 | 0.001 | [0.0,0.0,0.0] | [0.0,0.0,0.0] | [0.0,0.0,0.0] | 0.0 | 0.0 | 0.0 | False | True | True |  |  | False
29 | WJCP_029 | bottom_center/clip_horizontal_bottom_right_1/rail_1::shaft_to_nut_washer_bore | open_bolt_shank_to_washer_bore | M02_A00_NUT_WASHER | M00_A00_BOLT_HEAD_PLUS_SHAFT_UNION | CFN | matched_force_vector | 0.001 | 0.001 | [0.0,0.0,0.0] | [0.0,0.0,0.0] | [0.0,0.0,0.0] | 0.0 | 0.0 | 0.0 | False | True | True | True | True | True
29 | WJCP_029 | bottom_center/clip_horizontal_bottom_right_1/rail_1::shaft_to_nut_washer_bore | open_bolt_shank_to_washer_bore | M02_A00_NUT_WASHER | M00_A00_BOLT_HEAD_PLUS_SHAFT_UNION | CFS | matched_force_vector | 0.001 | 0.001 | [0.0,0.0,0.0] | [0.0,0.0,0.0] | [0.0,0.0,0.0] | 0.0 | 0.0 | 0.0 | False | True | True |  |  | False
30 | WJCP_030 | bottom_center/clip_horizontal_bottom_right_1/rail_2::shaft_to_head_washer_bore | open_bolt_shank_to_washer_bore | M05_A01_HEAD_WASHER | M04_A01_BOLT_HEAD_PLUS_SHAFT_UNION | CF | matched_force_vector | 0.001 | 0.001 | [0.0,0.0,0.0] | [0.0,0.0,0.0] | [0.0,0.0,0.0] | 0.0 | 0.0 | 0.0 | False | True | True |  |  | False
30 | WJCP_030 | bottom_center/clip_horizontal_bottom_right_1/rail_2::shaft_to_head_washer_bore | open_bolt_shank_to_washer_bore | M05_A01_HEAD_WASHER | M04_A01_BOLT_HEAD_PLUS_SHAFT_UNION | CFN | matched_force_vector | 0.001 | 0.001 | [0.0,0.0,0.0] | [0.0,0.0,0.0] | [0.0,0.0,0.0] | 0.0 | 0.0 | 0.0 | False | True | True | True | True | True
30 | WJCP_030 | bottom_center/clip_horizontal_bottom_right_1/rail_2::shaft_to_head_washer_bore | open_bolt_shank_to_washer_bore | M05_A01_HEAD_WASHER | M04_A01_BOLT_HEAD_PLUS_SHAFT_UNION | CFS | matched_force_vector | 0.001 | 0.001 | [0.0,0.0,0.0] | [0.0,0.0,0.0] | [0.0,0.0,0.0] | 0.0 | 0.0 | 0.0 | False | True | True |  |  | False
31 | WJCP_031 | bottom_center/clip_horizontal_bottom_right_1/rail_2::shaft_to_nut_washer_bore | open_bolt_shank_to_washer_bore | M06_A01_NUT_WASHER | M04_A01_BOLT_HEAD_PLUS_SHAFT_UNION | CF | matched_force_vector | 0.001 | 0.001 | [0.0,0.0,0.0] | [0.0,0.0,0.0] | [0.0,0.0,0.0] | 0.0 | 0.0 | 0.0 | False | True | True |  |  | False
31 | WJCP_031 | bottom_center/clip_horizontal_bottom_right_1/rail_2::shaft_to_nut_washer_bore | open_bolt_shank_to_washer_bore | M06_A01_NUT_WASHER | M04_A01_BOLT_HEAD_PLUS_SHAFT_UNION | CFN | matched_force_vector | 0.001 | 0.001 | [0.0,0.0,0.0] | [0.0,0.0,0.0] | [0.0,0.0,0.0] | 0.0 | 0.0 | 0.0 | False | True | True | True | True | True
31 | WJCP_031 | bottom_center/clip_horizontal_bottom_right_1/rail_2::shaft_to_nut_washer_bore | open_bolt_shank_to_washer_bore | M06_A01_NUT_WASHER | M04_A01_BOLT_HEAD_PLUS_SHAFT_UNION | CFS | matched_force_vector | 0.001 | 0.001 | [0.0,0.0,0.0] | [0.0,0.0,0.0] | [0.0,0.0,0.0] | 0.0 | 0.0 | 0.0 | False | True | True |  |  | False
32 | WJCP_032 | bottom_center/clip_horizontal_bottom_right_1/principal_1::shaft_to_head_washer_bore | open_bolt_shank_to_washer_bore | M09_A02_HEAD_WASHER | M08_A02_BOLT_HEAD_PLUS_SHAFT_UNION | CF | matched_force_vector | 0.001 | 0.001 | [0.0,0.0,0.0] | [0.0,0.0,0.0] | [0.0,0.0,0.0] | 0.0 | 0.0 | 0.0 | False | True | True |  |  | False
32 | WJCP_032 | bottom_center/clip_horizontal_bottom_right_1/principal_1::shaft_to_head_washer_bore | open_bolt_shank_to_washer_bore | M09_A02_HEAD_WASHER | M08_A02_BOLT_HEAD_PLUS_SHAFT_UNION | CFN | matched_force_vector | 0.001 | 0.001 | [0.0,0.0,0.0] | [0.0,0.0,0.0] | [0.0,0.0,0.0] | 0.0 | 0.0 | 0.0 | False | True | True | True | True | True
32 | WJCP_032 | bottom_center/clip_horizontal_bottom_right_1/principal_1::shaft_to_head_washer_bore | open_bolt_shank_to_washer_bore | M09_A02_HEAD_WASHER | M08_A02_BOLT_HEAD_PLUS_SHAFT_UNION | CFS | matched_force_vector | 0.001 | 0.001 | [0.0,0.0,0.0] | [0.0,0.0,0.0] | [0.0,0.0,0.0] | 0.0 | 0.0 | 0.0 | False | True | True |  |  | False
33 | WJCP_033 | bottom_center/clip_horizontal_bottom_right_1/principal_1::shaft_to_nut_washer_bore | open_bolt_shank_to_washer_bore | M10_A02_NUT_WASHER | M08_A02_BOLT_HEAD_PLUS_SHAFT_UNION | CF | matched_force_vector | 0.001 | 0.001 | [0.0,0.0,0.0] | [0.0,0.0,0.0] | [0.0,0.0,0.0] | 0.0 | 0.0 | 0.0 | False | True | True |  |  | False
33 | WJCP_033 | bottom_center/clip_horizontal_bottom_right_1/principal_1::shaft_to_nut_washer_bore | open_bolt_shank_to_washer_bore | M10_A02_NUT_WASHER | M08_A02_BOLT_HEAD_PLUS_SHAFT_UNION | CFN | matched_force_vector | 0.001 | 0.001 | [0.0,0.0,0.0] | [0.0,0.0,0.0] | [0.0,0.0,0.0] | 0.0 | 0.0 | 0.0 | False | True | True | True | True | True
33 | WJCP_033 | bottom_center/clip_horizontal_bottom_right_1/principal_1::shaft_to_nut_washer_bore | open_bolt_shank_to_washer_bore | M10_A02_NUT_WASHER | M08_A02_BOLT_HEAD_PLUS_SHAFT_UNION | CFS | matched_force_vector | 0.001 | 0.001 | [0.0,0.0,0.0] | [0.0,0.0,0.0] | [0.0,0.0,0.0] | 0.0 | 0.0 | 0.0 | False | True | True |  |  | False
34 | WJCP_034 | bottom_center/clip_horizontal_bottom_right_1/principal_2::shaft_to_head_washer_bore | open_bolt_shank_to_washer_bore | M13_A03_HEAD_WASHER | M12_A03_BOLT_HEAD_PLUS_SHAFT_UNION | CF | matched_force_vector | 0.001 | 0.001 | [0.0,0.0,0.0] | [0.0,0.0,0.0] | [0.0,0.0,0.0] | 0.0 | 0.0 | 0.0 | False | False | True |  |  | False
34 | WJCP_034 | bottom_center/clip_horizontal_bottom_right_1/principal_2::shaft_to_head_washer_bore | open_bolt_shank_to_washer_bore | M13_A03_HEAD_WASHER | M12_A03_BOLT_HEAD_PLUS_SHAFT_UNION | CFN | child_only |  | 0.001 |  | [0.0,0.0,0.0] |  |  |  |  |  |  | True |  | True | True
34 | WJCP_034 | bottom_center/clip_horizontal_bottom_right_1/principal_2::shaft_to_head_washer_bore | open_bolt_shank_to_washer_bore | M13_A03_HEAD_WASHER | M12_A03_BOLT_HEAD_PLUS_SHAFT_UNION | CFS | child_only |  | 0.001 |  | [0.0,0.0,0.0] |  |  |  |  |  |  | True |  |  | False
35 | WJCP_035 | bottom_center/clip_horizontal_bottom_right_1/principal_2::shaft_to_nut_washer_bore | open_bolt_shank_to_washer_bore | M14_A03_NUT_WASHER | M12_A03_BOLT_HEAD_PLUS_SHAFT_UNION | CF | child_only |  | 0.001 |  | [0.0,0.0,0.0] |  |  |  |  |  |  | True |  |  | False
35 | WJCP_035 | bottom_center/clip_horizontal_bottom_right_1/principal_2::shaft_to_nut_washer_bore | open_bolt_shank_to_washer_bore | M14_A03_NUT_WASHER | M12_A03_BOLT_HEAD_PLUS_SHAFT_UNION | CFN | child_only |  | 0.001 |  | [0.0,0.0,0.0] |  |  |  |  |  |  | True |  | True | True
35 | WJCP_035 | bottom_center/clip_horizontal_bottom_right_1/principal_2::shaft_to_nut_washer_bore | open_bolt_shank_to_washer_bore | M14_A03_NUT_WASHER | M12_A03_BOLT_HEAD_PLUS_SHAFT_UNION | CFS | missing_both |  |  |  |  |  |  |  |  |  |  |  |  |  | False
