mckayreedmoore/mini-moonboard/docs/wood-joints-mvp/hypotheses/evaluation-resume-2026-09-24/current-midpoint-clearance-map-attempt01/current-midpoint-clearance-map.png

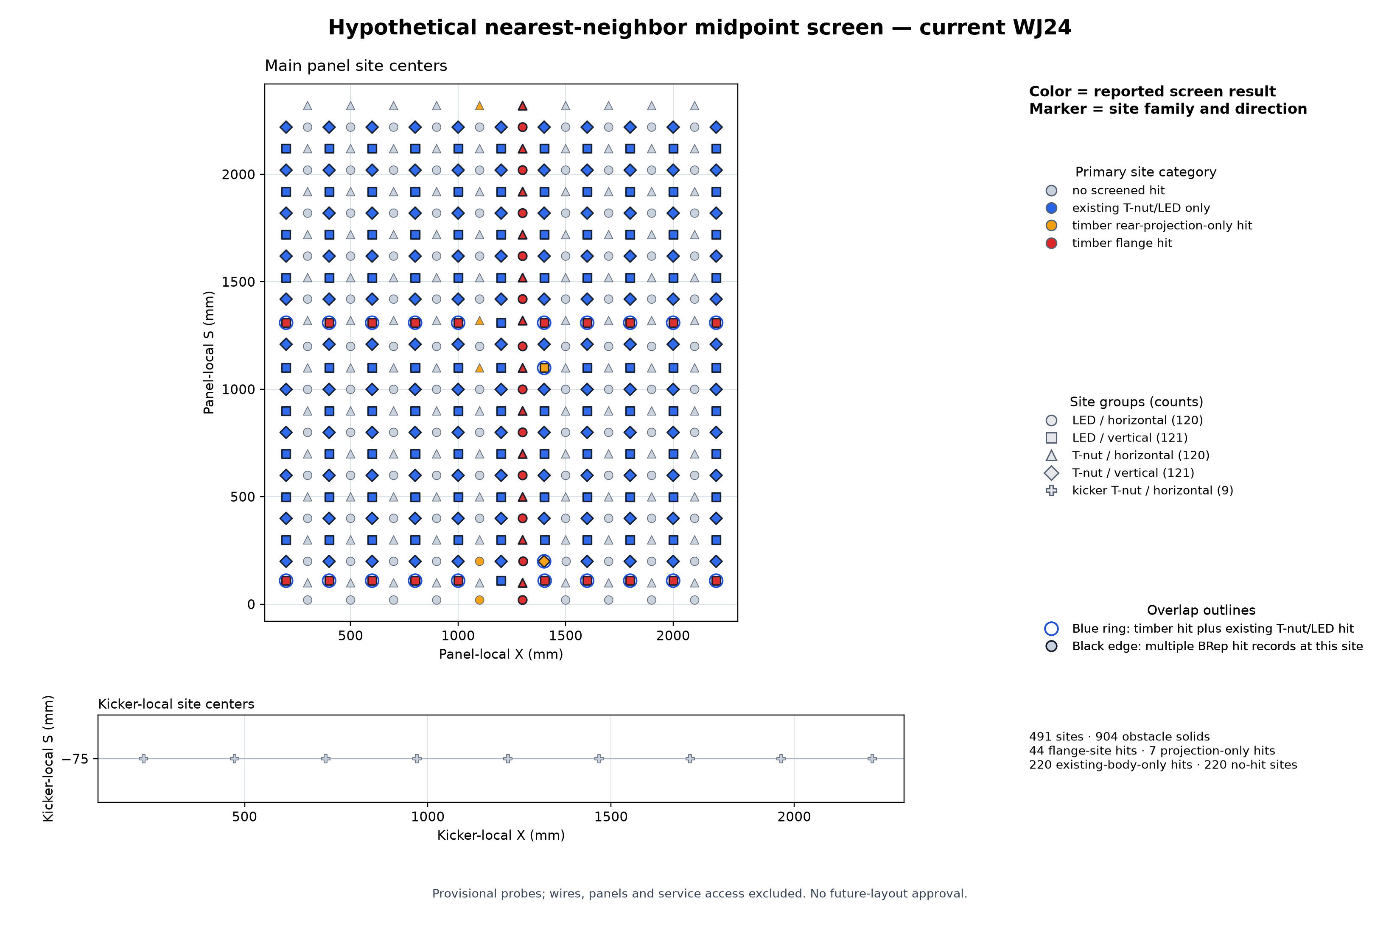
docs/wood-joints-mvp/hypotheses/evaluation-resume-2026-09-24/current-midpoint-clearance-map-attempt01/current-midpoint-clearance-map.png
