mckayreedmoore/mini-moonboard/docs/history/current-diy-completion-record.md

# Current completion record: flush floor-runner development

The selected development is `compact-floor-flush-development`: solid 4×6
legs/rims, compact 2×6 base members, two outboard floor runners, whole kickers,
the 1:12 rear recess, twelve complete outward-facing bolt stacks and 66
panel/kicker axes. Authority and criteria are frozen. Six fresh no-slip cases
meet all 36 adopted checks in the [authenticated aggregate](floor-runner-mvp-evidence.json).
The [MVP master plan](floor-runner-mvp-master-plan.md) retains final verification
and installation checks. Unrated commercial-angle separation and independent
flange couples remain disclosed limitations under the master plan, not
qualified capacities or automatic redesign prerequisites. This is not a
fabrication release.

The [floor-runner completion ledger](floor-runner-mvp-completion-ledger.md)
records all 36 adopted checks, installation controls and analytical limits.
FR-7 artifacts were rebuilt; selected-candidate browser interaction remains
the FR-8 task. Post-edit verification is in the ledger. Historical records
below do not transfer.

## Preserved spliced flush-top completion record

The following record is historical and does not qualify the selected
floor-runner assembly.

Six fresh assembled no-slip cases meet the listed conditional checks. This is
engineer-unreviewed conditional DIY evidence, not a construction release or
unconditional climber rating. The 0.361 mm directional placement margin and
1.9 mm group-spacing margin are tight installation limits. Full-root lateral
values above 1.0 are non-adopted sensitivities. Retained ML24Z/SDS separation
capacity and independent flange-couple applicability remain an open connection
gate, so finite completion is not established. Earlier floor-flush/taper and
compact-spliced-kicker evidence remains historical and does not transfer.

## Preserved preceding completion record

The following is historical. Its references to "current" or "selected" apply
to the candidate described there, not the flush revision above.

# Current DIY completion record

The selected candidate is **`compact-floor-rail-development`**, September 14,
2026. Its [study and conditional fabrication package](clear-space-study.md)
are the current authorities. The agreed endpoint remains documented,
engineer-unreviewed DIY design under explicit assumptions, not certification
or an unconditional climber weight rating.

## Selected detail and finite completion

Two continuous single 2×6 floor rails replace the raised knees. Retain the
solid 4×6 legs and flush rims, compact 2×6 header/posts, two centered ½-inch
upper bolts per leg at 56 mm pitch, and two ⅜-inch bolts at each rail end:
**12 complete bolt stacks**. The floor-specific package includes moved outer
posts, shifted clips and kicker screws, and the required kicker notches.
The 277 mm main-face datum, 127 mm pad allowance, accepted panel/T-nut basis
and 66 panel/kicker screws remain. Pads do not support the timber.

| Deliverable | Evidence and disposition |
| --- | --- |
| Current assembled response | Six corrected floor cases meet all 25 listed conditional criteria per case; maximum adopted bolt ratio 0.825. Earlier notch-omitted runs are superseded diagnostics. |
| Contact sensitivity | The separate 14×2 rail-contact refinement also meets all 25 criteria. Global bolt/deflection results are stable in this comparison; local pressure is not converged. |
| Hardware and installation | Use the [floor hardware schedule](clear-space-hardware.md). Full-body/thread-transition conditions govern the passing nominal-diameter route; the 1.038 full-thread-root sensitivity does not qualify fully threaded substitutes. |
| Matching fabrication | The [floor packet](clear-space-study.md#candidate-specific-fabrication-packages) supplies stock, actual profiles, connection axes, notch sheets, hardware and assembly guidance for this exact candidate. Do not mix it with knee or exterior-brace schedules. |
| Software/artifact evidence | The [study](clear-space-study.md#software-and-artifact-verification) records clean exports, checksum and browser checks for the floor geometry. These checks do not add structural qualification. |

The finite floor-rail assessment and conditional package are complete under
their stated scope. **Commercial-angle unlisted separation and independent
flange couples remain unqualified**; rated component-force checks do not
supply those capacities. No-slip support remains an explicit analytical
assumption, not measured floor friction or an installed anchor. Accepted
panel construction is retained. No new general panel campaign, floor-friction
test, external engineer review or failure-weight search is added.

The previous spliced-knee selection and its completed evidence remain below
as a reference. They do not transfer acceptance to the floor assembly. A
separate 2×4 floor-rail trial is not selected or accepted by this record;
optional exploration does not reopen the completed 2×6 package.

## Preserved spliced-knee completion record, September 13

The following records the preceding selection, including its original
completion and subsequent installation changes. References to “current” or
“selected” within this historical record apply to the spliced-knee candidate,
not today's floor-rail assembly.

The selected candidate is **`compact-spliced-knee-development`**, September 13,
2026. Its [study](compact-splice-study.md) and [build package](compact-spliced-build-package.md)
are the current authorities. The agreed endpoint is a documented
**engineer-unreviewed DIY design**, not professional certification, physical
inspection or an unconditional climber weight rating.

### Selected detail and scope

The frame uses solid 4×6 legs and flush outer rims, a compact 2×6 header/posts,
and two centered ½-inch upper bolts per leg at 56 mm pitch. Four independent
unnotched diagonal 2×6 pieces form the knees. Each side has four ⅜-inch splice
bolts and two ⅜-inch bolts at each endpoint, giving 20 complete bolt stacks.
The paired pieces have an explicit lap connection; composite action is not
assumed. Earlier notched braces and failed upper-joint layouts are historical.

Retain the 277 mm main-face datum (150 mm exposed kicker plus a 127 mm pad
allowance), accepted panel/T-nut construction and 66 panel/kicker screws.
Timber supports bear on the floor under the stated no-slip assumption; padding
is not a structural support. Specified lumber is dry, unincised Douglas
Fir–Larch No. 2. Catalog hardware, dimensional bounds and conditional material
properties are documented in the study and matching hardware assessments.

The selected load cases include the 250 lb design inquiry with stated downward
multipliers and 300 N horizontal scenarios. The study defines their exact
positions, directions and equipment assumptions. These finite scenarios are
not a measured impact spectrum or every possible climbing action.

### Finite completion gates

| Deliverable | Evidence and disposition |
| --- | --- |
| Current assembled response | Final case ledger and numerical acceptance in the [study](compact-splice-study.md). All six current cases converged and passed all 21 listed conditional criteria; the highest adopted bolt ratio is 0.674. |
| Connections, members and hardware | Current forces, finite-contact assumptions, spacing, local sections and catalog-dimension resistance comparisons are reported together in the study and pass their listed gates. No acceptance transfers from predecessor models. |
| Matching instructions | The [build package](compact-spliced-build-package.md) identifies this exact geometry, cuts, fresh drilling, complete hardware and assembly sequence. |
| Final consistency | The clean CAD rebuild matches all 769 viewer/STEP artifacts; all 17 construction artifacts and source hashes match. Default tests: 441 passed, 15 historical tests deselected; lint and CadQuery smoke check passed. The functional browser check also passes: 767 meshes, all 20 complete bolt stacks, current selection, documents and floor datums. The rear view and representative leg/knee drilling sheets were visually inspected. |

The owner does not require external engineer review, floor-friction testing,
a general panel qualification campaign or a destructive failure-weight search.
Those are not added completion gates. Explicit analytical/material/installation
assumptions remain limitations of the DIY package; owner acceptance does not
turn a failed calculation into a passing one.

### Historical evidence

The [original response](current-frame-response.md), [compact three-bolt study](compact-thick-study.md),
[solid-4×6 pivot study](thick-leg-pivot-study.md) and intervening knee trials
remain preserved. Their reported shortcomings explain the revisions; they are
not the current joint's result. Do not repeat an earlier three-bolt failure as
the current authority, and do not transfer a historical pivot pass.

The finite task ends when this selected detail has its supported recorded
result, matching instructions and explicit scope limits. Speculative further
improvements are not unfinished requirements.

### Completion

Completed September 13, 2026. The selected detail meets the finite analytical
gates and has matching CAD, viewer, dimensional sheets, stock and hardware
schedules, assembly instructions and CI freshness checks. No design alternative
or additional planning task remains open within the agreed scope. The documented
material, hardware-fit and installation conditions still apply to fabrication.

Browser validation used `CAD_VIEWER_SCREENSHOTS=0` for its final functional
run after screenshot capture stalled during viewport changes in the local
headless renderer. The current rear image was inspected separately; leg and
knee SVG sheets were rendered independently for visual inspection. No browser
JavaScript errors occurred during the passing functional run.

### End-finish and bolt-installation update

The current viewer and drawings use `compact_spliced_trimmed`, wrapping the
outward-bolt installation and the frozen `compact_spliced_knee_frame` analysis
definition. Sixteen inward-facing stacks were reversed; four already-outward
endpoint stacks were retained. All 40 actual receivers/washer seats pass after
the end cuts. Knee tips are flush; leg tops retain 18 mm projection.

[Current trim checks](compact-spliced-construction/end-trim-check.json) reapply
the six saved force cases to current end geometry and hardware. The highest
bolt ratio remains 0.674; updated local parallel ratio is 0.276. Cuts remove
1.410 kg of modeled wood and remain beyond every bolt bore's full-section span.
Original native stiffness and gravity placement are retained as an explicit
small exterior-tail approximation. These are not six newly solved trimmed
assemblies. See the matching build package for tighter rim-end bolt shank
acceptance, cutting datums and the retained geometric tolerances.

Validation for this update: 445 default tests passed, 15 historical tests
deselected; lint and clean current CAD regeneration passed. Functional browser
checks confirmed all 767 meshes and every outward-facing head/nut pair. Updated
leg and knee drawings were independently rendered and visually inspected.

### Lower kicker row update

The current export adapter is `compact_spliced_kicker`. Four lower kicker screws
move from Z112 to Z60 mm; all other axes, stock sizes and hardware counts remain
fixed. Fresh-stock drilling and schedules reflect the relocation. Local receiver
and interference checks apply; the accepted panel basis is retained. The frozen
six native cases still contain the preceding screw locations. This update does
not claim a new assembled response or new panel qualification. See the
[kicker placement review](kicker-screw-placement-review.md).

Validation: 448 default tests passed, 15 historical checks deselected; Ruff and
the clean current export rebuild passed. Browser checks loaded all 767 parts
and confirmed the four lower screw meshes at Z60. The construction packet and
current mass record were regenerated; historical model outputs remain unchanged.
