mckayreedmoore/mini-moonboard/docs/history/prototype-weights.md

# Prototype weight estimates

All 60 viewer prototypes display their modeled weights in kg and lb, both in the
design menu and beside the selected model. These are estimates, not measured
weights or load ratings. Current candidates include modeled T-nut envelopes;
holds, hold bolts, unmodeled retention screws, LEDs and wiring are excluded.
Historical concepts include only hardware represented in their geometry.
The two displayed crash pads are separate user equipment and excluded from
these structural model weight estimates.

Seven recent totals use authenticated CAD mass inventories with unioned fastener
components. Other totals integrate closed, oriented STL surfaces. Mesh estimates
retain overlapping compound hardware envelopes and coarse tessellation, so they
are less accurate. Assumed densities: wood/plywood 600 kg/m³, steel 7,850 kg/m³,
and die-cast zinc inserts 6,700 kg/m³. Actual stock moisture, species and hardware
can change the built weight.

| Prototype | kg | lb | Basis |
| --- | ---: | ---: | --- |
| [compact-floor-taper-development](https://mckayreedmoore.github.io/mini-moonboard/?model=compact-floor-taper-development) | 211.5 | 466.2 | mesh estimate; development trial |
| [compact-floor-recess-development](https://mckayreedmoore.github.io/mini-moonboard/?model=compact-floor-recess-development) | 213.0 | 469.7 | mesh estimate; unaccepted trial |
| [compact-floor-rail-2x4-development](https://mckayreedmoore.github.io/mini-moonboard/?model=compact-floor-rail-2x4-development) | 209.2 | 461.3 | mesh estimate; unaccepted trial |
| [compact-floor-rail-development](https://mckayreedmoore.github.io/mini-moonboard/?model=compact-floor-rail-development) | 213.9 | 471.6 | mesh estimate |
| [compact-exterior-brace-development](https://mckayreedmoore.github.io/mini-moonboard/?model=compact-exterior-brace-development) | 215.1 | 474.2 | mesh estimate |
| [compact-spliced-knee-development](https://mckayreedmoore.github.io/mini-moonboard/?model=compact-spliced-knee-development) | 209.5 | 461.8 | mesh estimate |
| [round-insert-development](https://mckayreedmoore.github.io/mini-moonboard/?model=round-insert-development) | 167.6 | 369.5 | audited CAD |
| [round-bore-service-development](https://mckayreedmoore.github.io/mini-moonboard/?model=round-bore-service-development) | 167.1 | 368.3 | audited CAD |
| [horizontal-service-development](https://mckayreedmoore.github.io/mini-moonboard/?model=horizontal-service-development) | 167.5 | 369.2 | audited CAD |
| [angle-base-development](https://mckayreedmoore.github.io/mini-moonboard/?model=angle-base-development) | 192.7 | 424.7 | audited CAD |
| [infill-panel-development](https://mckayreedmoore.github.io/mini-moonboard/?model=infill-panel-development) | 195.6 | 431.3 | audited CAD |
| [split-center-development](https://mckayreedmoore.github.io/mini-moonboard/?model=split-center-development) | 195.2 | 430.4 | audited CAD |
| [vertical-principal-development](https://mckayreedmoore.github.io/mini-moonboard/?model=vertical-principal-development) | 189.7 | 418.1 | mesh estimate |
| [paired-rail-base-development](https://mckayreedmoore.github.io/mini-moonboard/?model=paired-rail-base-development) | 165.3 | 364.4 | mesh estimate |
| [selective-2x6-development](https://mckayreedmoore.github.io/mini-moonboard/?model=selective-2x6-development) | 161.4 | 355.9 | audited CAD |
| [single-2x6-development](https://mckayreedmoore.github.io/mini-moonboard/?model=single-2x6-development) | 146.2 | 322.2 | mesh estimate |
| [2x10](https://mckayreedmoore.github.io/mini-moonboard/?model=2x10) | 214.6 | 473.0 | mesh estimate |
| [2x12](https://mckayreedmoore.github.io/mini-moonboard/?model=2x12) | 225.7 | 497.7 | mesh estimate |
| [2x8-foot100](https://mckayreedmoore.github.io/mini-moonboard/?model=2x8-foot100) | 204.7 | 451.2 | mesh estimate |
| [2x8-shallow](https://mckayreedmoore.github.io/mini-moonboard/?model=2x8-shallow) | 204.4 | 450.6 | mesh estimate |
| [base-bearing-concept](https://mckayreedmoore.github.io/mini-moonboard/?model=base-bearing-concept) | 162.3 | 357.7 | mesh estimate |
| [bearing-lean-frame](https://mckayreedmoore.github.io/mini-moonboard/?model=bearing-lean-frame) | 186.7 | 411.6 | mesh estimate |
| [bolted-block-frame](https://mckayreedmoore.github.io/mini-moonboard/?model=bolted-block-frame) | 295.5 | 651.5 | mesh estimate |
| [bolted-clip-frame](https://mckayreedmoore.github.io/mini-moonboard/?model=bolted-clip-frame) | 289.2 | 637.5 | mesh estimate |
| [commercial-bracket-mvp](https://mckayreedmoore.github.io/mini-moonboard/?model=commercial-bracket-mvp) | 192.4 | 424.1 | mesh estimate |
| [continuous-lean-frame](https://mckayreedmoore.github.io/mini-moonboard/?model=continuous-lean-frame) | 185.5 | 408.9 | mesh estimate |
| [independent-leg-development](https://mckayreedmoore.github.io/mini-moonboard/?model=independent-leg-development) | 224.7 | 495.4 | mesh estimate |
| [joint-development](https://mckayreedmoore.github.io/mini-moonboard/?model=joint-development) | 224.2 | 494.4 | mesh estimate |
| [lean-38mm-frame](https://mckayreedmoore.github.io/mini-moonboard/?model=lean-38mm-frame) | 185.0 | 407.9 | mesh estimate |
| [lower-transition-development](https://mckayreedmoore.github.io/mini-moonboard/?model=lower-transition-development) | 233.7 | 515.2 | mesh estimate |
| [lumber-leg-2x10-e0](https://mckayreedmoore.github.io/mini-moonboard/?model=lumber-leg-2x10-e0) | 207.2 | 456.8 | mesh estimate |
| [lumber-leg-2x10-e150](https://mckayreedmoore.github.io/mini-moonboard/?model=lumber-leg-2x10-e150) | 207.7 | 457.9 | mesh estimate |
| [lumber-leg-2x10-e300](https://mckayreedmoore.github.io/mini-moonboard/?model=lumber-leg-2x10-e300) | 208.3 | 459.2 | mesh estimate |
| [lumber-leg-2x12-e0](https://mckayreedmoore.github.io/mini-moonboard/?model=lumber-leg-2x12-e0) | 211.3 | 465.8 | mesh estimate |
| [lumber-leg-2x12-e150](https://mckayreedmoore.github.io/mini-moonboard/?model=lumber-leg-2x12-e150) | 211.9 | 467.1 | mesh estimate |
| [lumber-leg-2x12-e300](https://mckayreedmoore.github.io/mini-moonboard/?model=lumber-leg-2x12-e300) | 212.6 | 468.7 | mesh estimate |
| [lumber-leg-2x6-e0](https://mckayreedmoore.github.io/mini-moonboard/?model=lumber-leg-2x6-e0) | 199.5 | 439.9 | mesh estimate |
| [lumber-leg-2x6-e150](https://mckayreedmoore.github.io/mini-moonboard/?model=lumber-leg-2x6-e150) | 199.8 | 440.5 | mesh estimate |
| [lumber-leg-2x6-e300](https://mckayreedmoore.github.io/mini-moonboard/?model=lumber-leg-2x6-e300) | 200.2 | 441.3 | mesh estimate |
| [lumber-leg-2x8-e0](https://mckayreedmoore.github.io/mini-moonboard/?model=lumber-leg-2x8-e0) | 203.1 | 447.8 | mesh estimate |
| [lumber-leg-2x8-e150](https://mckayreedmoore.github.io/mini-moonboard/?model=lumber-leg-2x8-e150) | 203.5 | 448.6 | mesh estimate |
| [lumber-leg-2x8-e300](https://mckayreedmoore.github.io/mini-moonboard/?model=lumber-leg-2x8-e300) | 204.0 | 449.7 | mesh estimate |
| [lumber-leg-hardware-2x6-e0](https://mckayreedmoore.github.io/mini-moonboard/?model=lumber-leg-hardware-2x6-e0) | 200.0 | 441.0 | mesh estimate |
| [lumber-leg-spread-2x6-e300](https://mckayreedmoore.github.io/mini-moonboard/?model=lumber-leg-spread-2x6-e300) | 200.4 | 441.8 | mesh estimate |
| [lumber-leg-spread-2x8-e300](https://mckayreedmoore.github.io/mini-moonboard/?model=lumber-leg-spread-2x8-e300) | 204.2 | 450.2 | mesh estimate |
| [mid-batten-clip-development](https://mckayreedmoore.github.io/mini-moonboard/?model=mid-batten-clip-development) | 226.0 | 498.3 | mesh estimate |
| [panel-insert-development](https://mckayreedmoore.github.io/mini-moonboard/?model=panel-insert-development) | 180.5 | 398.0 | mesh estimate |
| [plywood](https://mckayreedmoore.github.io/mini-moonboard/?model=plywood) | 191.9 | 423.0 | mesh estimate |
| [screw-spacing-development](https://mckayreedmoore.github.io/mini-moonboard/?model=screw-spacing-development) | 225.9 | 497.9 | mesh estimate |
| [selected-hardware-development](https://mckayreedmoore.github.io/mini-moonboard/?model=selected-hardware-development) | 233.3 | 514.3 | mesh estimate |
| [square-2x6-development](https://mckayreedmoore.github.io/mini-moonboard/?model=square-2x6-development) | 165.1 | 364.0 | mesh estimate |
| [square-2x6-revised-development](https://mckayreedmoore.github.io/mini-moonboard/?model=square-2x6-revised-development) | 163.3 | 360.0 | mesh estimate |
| [square-cut-bracket](https://mckayreedmoore.github.io/mini-moonboard/?model=square-cut-bracket) | 192.5 | 424.4 | mesh estimate |
| [square-cut-wood-blocks](https://mckayreedmoore.github.io/mini-moonboard/?model=square-cut-wood-blocks) | 195.9 | 431.8 | mesh estimate |
| [timber-base-development](https://mckayreedmoore.github.io/mini-moonboard/?model=timber-base-development) | 180.1 | 397.0 | mesh estimate |
| [top-joint-development](https://mckayreedmoore.github.io/mini-moonboard/?model=top-joint-development) | 233.4 | 514.6 | mesh estimate |
| [wide-principal-development](https://mckayreedmoore.github.io/mini-moonboard/?model=wide-principal-development) | 204.5 | 450.7 | mesh estimate |
| [wood-first-mvp](https://mckayreedmoore.github.io/mini-moonboard/?model=wood-first-mvp) | 189.5 | 417.8 | mesh estimate |

The current horizontal-service estimate excludes all 263 displayed electrical
parts: 132 lights and 131 cable/connector bodies. Their purchased masses are
unknown; no material density or zero-mass claim is assigned. Their names,
counts and authenticated mesh hashes remain in the catalog.

The [catalog](../site/prototype-weights.json) records source/mesh hashes and mass
components. Deployment regenerates it after exporting the four historical hybrid
models. To regenerate locally, generate those viewer meshes first, then run:

```sh
uv run python scripts/build_prototype_weights.py
uv run pytest tests/test_prototype_weights.py -q
```
