mckayreedmoore/mini-moonboard/docs/history/current-goal.md

# Audited next design milestone

> **Historical document — superseded as current guidance on September 12, 2026.**
> Start with the [current design basis](current-design-basis.md) and
> [current design review](current-design-review.md) for `no-shoes-development`.
> The original text below preserves its candidate-specific decisions and evidence;
> “current,” “next,” and release requirements below refer to that historical scope.
> Its dimensions, schedules and results do not qualify the latest candidate.

## Goal statement

Deliver one independently reviewed, product-specific Mini MoonBoard design candidate ready for human audit, not construction approval. Build on the current 2×8-foot100 transition design; incorporate the purchased Roseburg Lowe’s item 12235/model 119055 23/32-CAT face plywood as a documented nominal assumption pending actual sheet measurements, separately specify leg/splice plywood, and integrate the selected DF-L lumber and real fastener families. Complete joints, hole/head/washer/tool clearances, front-driven panel screws, LED/wiring and hold-hardware provisions; distinguish sourced geometry from explicit allowances. Preserve all earlier variants/results and other agents’ changes. Test member orientation, floor seating, unintended intersections, bearing/contact, edge/end distances and fastener engagement; publish synchronized CAD, viewer, metric/imperial cut lists, hardware schedule and assembly/audit notes. Preserve one-climber 250 lb intended maximum, 150/200 lb comparisons and 300 lb sensitivity; no anchors, pad support, assumed ballast or unverified composite-action credit. Separate geometric readiness from structural qualification. Use existing failed FEA evidence honestly; permit only bounded numerical work with stated acceptance criteria that answers a design decision, and never size joints from rejected force recovery. Defer 2×6 and tied-base comparisons until the product-specific joint baseline and numerical prerequisites are ready. Use independent subagent design/software reviews, fix confirmed findings, verify publication, and commit/push reasonably sized increments. Finish this milestone with an inspectable candidate, clear retain/change recommendation and exact unresolved product/human/structural verification list; do not imply use approval or mark failed safety checks passed.

## Why revise the previous goal?

The previous objective combined product integration, complete joint design,
unanchored contact qualification, force-recovery research and variant comparison
into one completion gate. Preserve those long-term requirements, but sequence
them: an inspectable product-specific candidate is the next deliverable, not a
claim that unresolved structural qualification has succeeded.

## Ordered work and completion evidence

1. Integrate the [purchased stock and selected lumber](purchased-materials.md),
   [bolts](selected-bolt-hardware.md) and [wood fasteners](selected-wood-fasteners.md).
   Resolve product/proxy differences explicitly, including US A21 geometry and
   custom-angle screw seating. Include dispositions for hold bolts, T-nut
   retainers and wiring hardware outside the frame-fastener inventory.
2. Complete the joint layout and geometric checks. Distinguish intentional
   engagement from unintended collisions. Unknown limits remain unknown, not
   passed. No unresolved finding may contradict the claimed geometric milestone.
3. Publish matching viewer geometry, holes, hardware, parts lists, metric/imperial
   dimensions and assembly notes. Verify the published candidate, not only local
   files. Preserve reference variants and their numerical evidence.
4. Independently review design and software; fix confirmed findings. Serialize
   heavy checks and commit/push coherent increments.
5. Hand off the retain/change recommendation, usable and rejected numerical
   evidence, and exact remaining verification gates. No room measurement or
   offcut test is a prerequisite for this design phase. No construction or use
   approval is implied.

## Structural work remains open

Product-compatible material properties, connection resistance, local unanchored
contact, reliable force recovery and global stability still require qualification.
Separate these from geometric readiness; do not remove them to declare success.
Revisit 2×6 or tied-base alternatives only when a qualified baseline makes the
comparison meaningful. Every new numerical experiment needs a specific design
question, bounded run plan and acceptance criteria established before running.

This document records the revised work plan. It does not itself change the
application's goal status or retire the previous structural-qualification work.
